NZFunGi/micro-radar/include/EmbeddedAirportCodes.h

#pragma once

// ICAO -> IATA airport code lookup, generated from OurAirports' public
// dataset (https://davidmegginson.github.io/ourairports-data/airports.csv,
// public domain) via a one-off filter (keep rows with both a valid 4-char
// ICAO and 3-char IATA code, sorted by ICAO for binary search). Regenerate
// by re-running that filter against a fresh copy of the CSV if this ever
// needs updating - not something this project re-derives at build time.
//
// Exists because OpenSky's /api/routes is ICAO-only (confirmed against its
// docs, not assumed) - RouteLookupManager tries hexdb.io first, which has a
// native IATA endpoint and needs no conversion, and only reaches for this
// table to convert OpenSky's ICAO fallback result to IATA for a consistent
// display format regardless of which source actually resolved a route.

#include <cstddef>
#include <cstring>

struct AirportCode {
    char icao[5]; // 4 chars + null terminator
    char iata[4]; // 3 chars + null terminator
};

constexpr size_t EMBEDDED_AIRPORT_CODE_COUNT = 7819;

// Sorted by icao - EmbeddedAirportLookup() below relies on this for binary search.
static const AirportCode EMBEDDED_AIRPORT_CODES[EMBEDDED_AIRPORT_CODE_COUNT] = {
    {"AGAF", "AFT"}, {"AGAR", "RNA"}, {"AGAT", "ATD"}, {"AGBA", "VEV"}, {"AGBT", "BPF"}, {"AGEV", "GEF"},
    {"AGGA", "AKS"}, {"AGGB", "BNY"}, {"AGGC", "CHY"}, {"AGGE", "BAS"}, {"AGGF", "FRE"}, {"AGGH", "HIR"},
    {"AGGI", "MBU"}, {"AGGJ", "AVU"}, {"AGGK", "IRA"}, {"AGGL", "SCZ"}, {"AGGM", "MUA"}, {"AGGN", "GZO"},
    {"AGGO", "MNY"}, {"AGGP", "PRS"}, {"AGGR", "RNL"}, {"AGGS", "EGM"}, {"AGGT", "NNB"}, {"AGGU", "RUS"},
    {"AGGV", "VAO"}, {"AGGY", "XYA"}, {"AGKG", "KGE"}, {"AGKU", "KUE"}, {"AGKW", "KWS"}, {"AGLM", "LLM"},
    {"AGNA", "NAZ"}, {"AGOB", "MHM"}, {"AGOK", "GTA"}, {"AGRC", "RIN"}, {"AGRM", "RBV"}, {"AGTI", "TLG"},
    {"AGVH", "VIU"}, {"ANYN", "INU"}, {"AYAA", "AMF"}, {"AYAE", "UAE"}, {"AYAF", "AFR"}, {"AYAG", "AUP"},
    {"AYAI", "ATP"}, {"AYAK", "AIH"}, {"AYAM", "AMU"}, {"AYAN", "ADC"}, {"AYAO", "AIE"}, {"AYAQ", "KPM"},
    {"AYAT", "AUJ"}, {"AYAW", "AWB"}, {"AYAX", "AEK"}, {"AYAY", "AYU"}, {"AYBA", "VMU"}, {"AYBC", "BCP"},
    {"AYBD", "BNM"}, {"AYBF", "BMZ"}, {"AYBG", "BDZ"}, {"AYBH", "BSP"}, {"AYBI", "BWP"}, {"AYBK", "BUA"},
    {"AYBL", "BAA"}, {"AYBM", "OPU"}, {"AYBO", "BMH"}, {"AYBP", "BPD"}, {"AYBQ", "BPK"}, {"AYBR", "BRP"},
    {"AYBU", "BUL"}, {"AYBZ", "XBN"}, {"AYCB", "CVB"}, {"AYCG", "CGC"}, {"AYCH", "CMU"}, {"AYCS", "SQT"},
    {"AYDB", "DBP"}, {"AYDE", "DER"}, {"AYDI", "BNT"}, {"AYDK", "MDM"}, {"AYDL", "KPF"}, {"AYDN", "DNU"},
    {"AYDO", "DOI"}, {"AYDR", "DOO"}, {"AYDU", "DAU"}, {"AYEA", "KRU"}, {"AYEB", "EMS"}, {"AYED", "XYR"},
    {"AYEE", "EMI"}, {"AYEF", "EFG"}, {"AYEH", "MHY"}, {"AYEL", "EPT"}, {"AYEN", "EGA"}, {"AYEO", "EMO"},
    {"AYER", "ERU"}, {"AYES", "MFZ"}, {"AYET", "BOT"}, {"AYEV", "ERE"}, {"AYEW", "SWE"}, {"AYFA", "FNE"},
    {"AYFI", "FIN"}, {"AYFR", "FAQ"}, {"AYFU", "FUM"}, {"AYGA", "GKA"}, {"AYGC", "GEW"}, {"AYGF", "GUG"},
    {"AYGG", "GRL"}, {"AYGI", "GAR"}, {"AYGJ", "GAZ"}, {"AYGL", "GOE"}, {"AYGN", "GUR"}, {"AYGP", "GAP"},
    {"AYGR", "PNP"}, {"AYGS", "GBC"}, {"AYGT", "GMI"}, {"AYGU", "AKG"}, {"AYGV", "GVI"}, {"AYGX", "GOC"},
    {"AYHB", "HBD"}, {"AYHE", "HNI"}, {"AYHF", "HYF"}, {"AYHH", "HNN"}, {"AYHK", "HKN"}, {"AYHO", "HIT"},
    {"AYHU", "HWA"}, {"AYIA", "IIS"}, {"AYID", "IDN"}, {"AYII", "IMN"}, {"AYIM", "KGM"}, {"AYIO", "IMD"},
    {"AYIQ", "KIE"}, {"AYIW", "WSA"}, {"AYIX", "WIU"}, {"AYIY", "MPX"}, {"AYJO", "KGH"}, {"AYJS", "JOP"},
    {"AYKA", "LSA"}, {"AYKB", "KBM"}, {"AYKC", "KDR"}, {"AYKD", "KMF"}, {"AYKG", "KPA"}, {"AYKH", "KAQ"},
    {"AYKI", "UNG"}, {"AYKJ", "KNE"}, {"AYKK", "KRI"}, {"AYKM", "KMA"}, {"AYKO", "KKD"}, {"AYKQ", "KGW"},
    {"AYKR", "KRX"}, {"AYKT", "KZF"}, {"AYKU", "KUQ"}, {"AYKV", "KVG"}, {"AYKW", "KWO"}, {"AYKY", "LNV"},
    {"AYLB", "LAB"}, {"AYLG", "KEG"}, {"AYLI", "KII"}, {"AYLL", "LGN"}, {"AYLM", "LMY"}, {"AYLN", "LNM"},
    {"AYLO", "LWI"}, {"AYLP", "LPN"}, {"AYLS", "LNG"}, {"AYLT", "LNC"}, {"AYLU", "LMI"}, {"AYLX", "LSJ"},
    {"AYMA", "MRM"}, {"AYMB", "OBM"}, {"AYMC", "MYX"}, {"AYMD", "MAG"}, {"AYMH", "HGU"}, {"AYMI", "MXK"},
    {"AYMJ", "MPG"}, {"AYML", "GUV"}, {"AYMN", "MDU"}, {"AYMO", "MAS"}, {"AYMP", "MLQ"}, {"AYMQ", "MQO"},
    {"AYMR", "MXH"}, {"AYMS", "MIS"}, {"AYMV", "MKN"}, {"AYMW", "MWG"}, {"AYMZ", "MPU"}, {"AYNA", "NKN"},
    {"AYNB", "KEX"}, {"AYNC", "NDN"}, {"AYND", "AUI"}, {"AYNE", "GBF"}, {"AYNI", "NUG"}, {"AYNJ", "NDI"},
    {"AYNM", "KSB"}, {"AYNN", "KDP"}, {"AYNO", "NMN"}, {"AYNS", "BXZ"}, {"AYNU", "UKU"}, {"AYNX", "ATN"},
    {"AYNY", "NBA"}, {"AYNZ", "LAE"}, {"AYOB", "OBX"}, {"AYOE", "KGB"}, {"AYOF", "OKV"}, {"AYOG", "OGE"},
    {"AYOJ", "OKP"}, {"AYOK", "HOC"}, {"AYOL", "KQL"}, {"AYOM", "OSE"}, {"AYOO", "KOM"}, {"AYOP", "KSP"},
    {"AYOQ", "KCJ"}, {"AYOV", "OLQ"}, {"AYOW", "KDE"}, {"AYPB", "PLE"}, {"AYPC", "PGB"}, {"AYPD", "PDI"},
    {"AYPE", "APR"}, {"AYPG", "PGN"}, {"AYPJ", "PMP"}, {"AYPO", "MPF"}, {"AYPQ", "PMN"}, {"AYPY", "POM"},
    {"AYQA", "KRJ"}, {"AYQL", "TLP"}, {"AYQO", "SPH"}, {"AYQQ", "ONB"}, {"AYQS", "SXA"}, {"AYRA", "KIQ"},
    {"AYRE", "RBP"}, {"AYRG", "RMN"}, {"AYRI", "KMR"}, {"AYRK", "RKU"}, {"AYRM", "MWI"}, {"AYRO", "KOR"},
    {"AYSA", "SBE"}, {"AYSD", "SDI"}, {"AYSE", "NIS"}, {"AYSF", "SFU"}, {"AYSG", "SIL"}, {"AYSH", "SBV"},
    {"AYSJ", "SIM"}, {"AYSK", "SGK"}, {"AYSL", "SXH"}, {"AYSO", "SBC"}, {"AYSP", "SMH"}, {"AYSS", "TDS"},
    {"AYSU", "SKC"}, {"AYSV", "SXW"}, {"AYSW", "SWG"}, {"AYSX", "MBV"}, {"AYTA", "TIZ"}, {"AYTB", "TBG"},
    {"AYTE", "TFM"}, {"AYTF", "TDB"}, {"AYTG", "TGL"}, {"AYTH", "TFB"}, {"AYTI", "TPI"}, {"AYTK", "RAB"},
    {"AYTN", "TKW"}, {"AYTO", "KDQ"}, {"AYTP", "TEP"}, {"AYTR", "TBQ"}, {"AYTS", "TSW"}, {"AYTT", "TRJ"},
    {"AYTU", "TFI"}, {"AYTV", "TBE"}, {"AYTW", "TWY"}, {"AYTY", "TEO"}, {"AYTZ", "TKB"}, {"AYUC", "UMC"},
    {"AYUE", "URU"}, {"AYUI", "UBI"}, {"AYUM", "AUV"}, {"AYUP", "GLP"}, {"AYUR", "UPR"}, {"AYUY", "KUX"},
    {"AYUZ", "UVO"}, {"AYVL", "TLW"}, {"AYVM", "TCJ"}, {"AYVN", "VAI"}, {"AYVO", "TON"}, {"AYVW", "WUV"},
    {"AYWB", "WAO"}, {"AYWC", "WTT"}, {"AYWD", "WBM"}, {"AYWF", "WAJ"}, {"AYWG", "AGL"}, {"AYWH", "WNU"},
    {"AYWJ", "WBC"}, {"AYWK", "WWK"}, {"AYWO", "WOA"}, {"AYWQ", "WKN"}, {"AYWS", "WSU"}, {"AYWT", "WTP"},
    {"AYWU", "WUG"}, {"AYXE", "YVD"}, {"AYXI", "SMJ"}, {"AYXO", "TLO"}, {"AYXP", "WPM"}, {"AYXW", "WEP"},
    {"AYYE", "KYX"}, {"AYYK", "YEQ"}, {"AYYL", "TCK"}, {"AYYM", "LNF"}, {"AYYO", "RAX"}, {"AYYP", "KPE"},
    {"AYYR", "KSX"}, {"AYZA", "ZEN"}, {"AYZI", "SWR"}, {"AYZN", "SIZ"}, {"AYZS", "OSG"}, {"BGAA", "JEG"},
    {"BGBW", "UAK"}, {"BGCH", "JCH"}, {"BGCO", "CNP"}, {"BGGH", "GOH"}, {"BGIG", "QFI"}, {"BGJN", "JAV"},
    {"BGKK", "KUS"}, {"BGMQ", "JSU"}, {"BGPT", "JFR"}, {"BGQO", "JJU"}, {"BGQQ", "NAQ"}, {"BGSF", "SFJ"},
    {"BGSG", "SGG"}, {"BGSI", "SRK"}, {"BGSO", "QOQ"}, {"BGSS", "JHS"}, {"BGST", "SAE"}, {"BGSV", "SVR"},
    {"BGTA", "TQA"}, {"BGTL", "THU"}, {"BGTN", "TQI"}, {"BGTQ", "XEQ"}, {"BGUK", "JUV"}, {"BGUM", "UMD"},
    {"BGUQ", "JQA"}, {"BGUT", "JUK"}, {"BIAR", "AEY"}, {"BIBD", "BIU"}, {"BIBF", "BGJ"}, {"BIBL", "BLO"},
    {"BIBV", "BXV"}, {"BIDV", "DJU"}, {"BIEG", "EGS"}, {"BIFM", "FAG"}, {"BIGF", "GUU"}, {"BIGJ", "GJR"},
    {"BIGR", "GRY"}, {"BIHK", "HVK"}, {"BIHN", "HFN"}, {"BIHU", "HZK"}, {"BIIS", "IFJ"}, {"BIKF", "KEF"},
    {"BIKP", "OPA"}, {"BIKR", "SAK"}, {"BINF", "NOR"}, {"BIRE", "RHA"}, {"BIRF", "OLI"}, {"BIRG", "RFN"},
    {"BIRK", "RKV"}, {"BIRL", "MVA"}, {"BISI", "SIJ"}, {"BIST", "SYK"}, {"BITE", "TEY"}, {"BITN", "THO"},
    {"BIVM", "VEY"}, {"BIVO", "VPN"}, {"BKPR", "PRN"}, {"CBBC", "ZEL"}, {"CYAB", "YAB"}, {"CYAC", "YAC"},
    {"CYAD", "YAR"}, {"CYAG", "YAG"}, {"CYAH", "YAH"}, {"CYAL", "YAL"}, {"CYAM", "YAM"}, {"CYAQ", "XKS"},
    {"CYAS", "YKG"}, {"CYAT", "YAT"}, {"CYAY", "YAY"}, {"CYAZ", "YAZ"}, {"CYBA", "YBA"}, {"CYBB", "YBB"},
    {"CYBC", "YBC"}, {"CYBD", "QBC"}, {"CYBE", "YBE"}, {"CYBF", "YBY"}, {"CYBG", "YBG"}, {"CYBK", "YBK"},
    {"CYBL", "YBL"}, {"CYBQ", "XTL"}, {"CYBR", "YBR"}, {"CYBT", "YBT"}, {"CYBV", "YBV"}, {"CYBX", "YBX"},
    {"CYCA", "YRF"}, {"CYCB", "YCB"}, {"CYCC", "YCC"}, {"CYCD", "YCD"}, {"CYCE", "YCE"}, {"CYCG", "YCG"},
    {"CYCH", "YCH"}, {"CYCK", "XCM"}, {"CYCL", "YCL"}, {"CYCN", "YCN"}, {"CYCO", "YCO"}, {"CYCQ", "YCQ"},
    {"CYCR", "YCR"}, {"CYCS", "YCS"}, {"CYCT", "YCT"}, {"CYCW", "YCW"}, {"CYCY", "YCY"}, {"CYCZ", "YCZ"},
    {"CYDA", "YDA"}, {"CYDB", "YDB"}, {"CYDF", "YDF"}, {"CYDL", "YDL"}, {"CYDM", "XRR"}, {"CYDN", "YDN"},
    {"CYDO", "YDO"}, {"CYDP", "YDP"}, {"CYDQ", "YDQ"}, {"CYEG", "YEG"}, {"CYEK", "YEK"}, {"CYEL", "YEL"},
    {"CYEM", "YEM"}, {"CYEN", "YEN"}, {"CYER", "YER"}, {"CYET", "YET"}, {"CYEU", "YEU"}, {"CYEV", "YEV"},
    {"CYEY", "YEY"}, {"CYFA", "YFA"}, {"CYFB", "YFB"}, {"CYFC", "YFC"}, {"CYFE", "YFE"}, {"CYFH", "YFH"},
    {"CYFJ", "YTM"}, {"CYFO", "YFO"}, {"CYFR", "YFR"}, {"CYFS", "YFS"}, {"CYFT", "YMN"}, {"CYGB", "YGB"},
    {"CYGH", "YGH"}, {"CYGK", "YGK"}, {"CYGL", "YGL"}, {"CYGM", "YGM"}, {"CYGO", "YGO"}, {"CYGP", "YGP"},
    {"CYGQ", "YGQ"}, {"CYGR", "YGR"}, {"CYGT", "YGT"}, {"CYGV", "YGV"}, {"CYGW", "YGW"}, {"CYGX", "YGX"},
    {"CYGZ", "YGZ"}, {"CYHA", "YQC"}, {"CYHB", "YHB"}, {"CYHC", "CXH"}, {"CYHD", "YHD"}, {"CYHE", "YHE"},
    {"CYHF", "YHF"}, {"CYHH", "YNS"}, {"CYHI", "YHI"}, {"CYHK", "YHK"}, {"CYHM", "YHM"}, {"CYHN", "YHN"},
    {"CYHO", "YHO"}, {"CYHP", "YHP"}, {"CYHR", "YHR"}, {"CYHT", "YHT"}, {"CYHU", "YHU"}, {"CYHY", "YHY"},
    {"CYHZ", "YHZ"}, {"CYIB", "YIB"}, {"CYID", "YDG"}, {"CYIF", "YIF"}, {"CYIK", "YIK"}, {"CYIO", "YIO"},
    {"CYIV", "YIV"}, {"CYJA", "YJA"}, {"CYJF", "YJF"}, {"CYJN", "YJN"}, {"CYJT", "YJT"}, {"CYKA", "YKA"},
    {"CYKC", "YKC"}, {"CYKD", "LAK"}, {"CYKF", "YKF"}, {"CYKG", "YWB"}, {"CYKJ", "YKJ"}, {"CYKL", "YKL"},
    {"CYKM", "YKD"}, {"CYKO", "AKV"}, {"CYKP", "YOG"}, {"CYKQ", "YKQ"}, {"CYKX", "YKX"}, {"CYKY", "YKY"},
    {"CYLA", "YPJ"}, {"CYLB", "YLB"}, {"CYLC", "YLC"}, {"CYLD", "YLD"}, {"CYLH", "YLH"}, {"CYLJ", "YLJ"},
    {"CYLK", "YSG"}, {"CYLL", "YLL"}, {"CYLQ", "YLQ"}, {"CYLR", "YLR"}, {"CYLS", "YLK"}, {"CYLT", "YLT"},
    {"CYLU", "XGR"}, {"CYLW", "YLW"}, {"CYMA", "YMA"}, {"CYME", "YME"}, {"CYMG", "YMG"}, {"CYMH", "YMH"},
    {"CYMJ", "YMJ"}, {"CYML", "YML"}, {"CYMM", "YMM"}, {"CYMO", "YMO"}, {"CYMT", "YMT"}, {"CYMU", "YUD"},
    {"CYMW", "YMW"}, {"CYMX", "YMX"}, {"CYNA", "YNA"}, {"CYNC", "YNC"}, {"CYND", "YND"}, {"CYNE", "YNE"},
    {"CYNH", "YNH"}, {"CYNJ", "YLY"}, {"CYNL", "YNL"}, {"CYNM", "YNM"}, {"CYNR", "HZP"}, {"CYOA", "YOA"},
    {"CYOC", "YOC"}, {"CYOD", "YOD"}, {"CYOH", "YOH"}, {"CYOJ", "YOJ"}, {"CYOO", "YOO"}, {"CYOP", "YOP"},
    {"CYOS", "YOS"}, {"CYOW", "YOW"}, {"CYPA", "YPA"}, {"CYPC", "YPC"}, {"CYPD", "YPS"}, {"CYPE", "YPE"},
    {"CYPG", "YPG"}, {"CYPH", "YPH"}, {"CYPL", "YPL"}, {"CYPM", "YPM"}, {"CYPN", "YPN"}, {"CYPO", "YPO"},
    {"CYPQ", "YPQ"}, {"CYPR", "YPR"}, {"CYPW", "YPW"}, {"CYPX", "YPX"}, {"CYPY", "YPY"}, {"CYPZ", "YPZ"},
    {"CYQA", "YQA"}, {"CYQB", "YQB"}, {"CYQD", "YQD"}, {"CYQF", "YQF"}, {"CYQG", "YQG"}, {"CYQH", "YQH"},
    {"CYQI", "YQI"}, {"CYQK", "YQK"}, {"CYQL", "YQL"}, {"CYQM", "YQM"}, {"CYQN", "YQN"}, {"CYQQ", "YQQ"},
    {"CYQR", "YQR"}, {"CYQS", "YQS"}, {"CYQT", "YQT"}, {"CYQU", "YQU"}, {"CYQV", "YQV"}, {"CYQW", "YQW"},
    {"CYQX", "YQX"}, {"CYQY", "YQY"}, {"CYQZ", "YQZ"}, {"CYRA", "YRA"}, {"CYRB", "YRB"}, {"CYRI", "YRI"},
    {"CYRJ", "YRJ"}, {"CYRL", "YRL"}, {"CYRM", "YRM"}, {"CYRO", "YRO"}, {"CYRQ", "YRQ"}, {"CYRS", "YRS"},
    {"CYRT", "YRT"}, {"CYRV", "YRV"}, {"CYSB", "YSB"}, {"CYSC", "YSC"}, {"CYSD", "YSD"}, {"CYSE", "YSE"},
    {"CYSF", "YSF"}, {"CYSH", "YSH"}, {"CYSJ", "YSJ"}, {"CYSK", "YSK"}, {"CYSL", "YSL"}, {"CYSM", "YSM"},
    {"CYSN", "YCM"}, {"CYSP", "YSP"}, {"CYST", "YST"}, {"CYSU", "YSU"}, {"CYSY", "YSY"}, {"CYTA", "YTA"},
    {"CYTE", "YTE"}, {"CYTF", "YTF"}, {"CYTH", "YTH"}, {"CYTL", "YTL"}, {"CYTQ", "YTQ"}, {"CYTR", "YTR"},
    {"CYTS", "YTS"}, {"CYTZ", "YTZ"}, {"CYUB", "YUB"}, {"CYUL", "YUL"}, {"CYUT", "YUT"}, {"CYUX", "YUX"},
    {"CYUY", "YUY"}, {"CYVB", "YVB"}, {"CYVC", "YVC"}, {"CYVG", "YVG"}, {"CYVK", "YVE"}, {"CYVL", "YCK"},
    {"CYVM", "YVM"}, {"CYVO", "YVO"}, {"CYVP", "YVP"}, {"CYVQ", "YVQ"}, {"CYVR", "YVR"}, {"CYVT", "YVT"},
    {"CYVV", "YVV"}, {"CYVZ", "YVZ"}, {"CYWA", "YWA"}, {"CYWE", "YFJ"}, {"CYWG", "YWG"}, {"CYWH", "YWH"},
    {"CYWJ", "YWJ"}, {"CYWK", "YWK"}, {"CYWL", "YWL"}, {"CYWP", "YWP"}, {"CYWY", "YWY"}, {"CYXC", "YXC"},
    {"CYXE", "YXE"}, {"CYXH", "YXH"}, {"CYXJ", "YXJ"}, {"CYXK", "YXK"}, {"CYXL", "YXL"}, {"CYXN", "YXN"},
    {"CYXP", "YXP"}, {"CYXQ", "YXQ"}, {"CYXR", "YXR"}, {"CYXS", "YXS"}, {"CYXT", "YXT"}, {"CYXU", "YXU"},
    {"CYXX", "YXX"}, {"CYXY", "YXY"}, {"CYXZ", "YXZ"}, {"CYYB", "YYB"}, {"CYYC", "YYC"}, {"CYYD", "YYD"},
    {"CYYE", "YYE"}, {"CYYF", "YYF"}, {"CYYG", "YYG"}, {"CYYH", "YYH"}, {"CYYJ", "YYJ"}, {"CYYL", "YYL"},
    {"CYYM", "YYM"}, {"CYYN", "YYN"}, {"CYYQ", "YYQ"}, {"CYYR", "YYR"}, {"CYYT", "YYT"}, {"CYYU", "YYU"},
    {"CYYW", "YYW"}, {"CYYY", "YYY"}, {"CYYZ", "YYZ"}, {"CYZE", "YZE"}, {"CYZF", "YZF"}, {"CYZG", "YZG"},
    {"CYZH", "YZH"}, {"CYZP", "YZP"}, {"CYZR", "YZR"}, {"CYZS", "YZS"}, {"CYZT", "YZT"}, {"CYZU", "YZU"},
    {"CYZV", "YZV"}, {"CYZW", "YZW"}, {"CYZX", "YZX"}, {"CZAC", "ZAC"}, {"CZAM", "YSN"}, {"CZBB", "YDT"},
    {"CZBD", "ILF"}, {"CZBF", "ZBF"}, {"CZBM", "ZBM"}, {"CZEE", "KES"}, {"CZEM", "ZEM"}, {"CZFA", "ZFA"},
    {"CZFD", "ZFD"}, {"CZFG", "XPK"}, {"CZFM", "ZFM"}, {"CZFN", "ZFN"}, {"CZGF", "ZGF"}, {"CZGI", "ZGI"},
    {"CZGR", "ZGR"}, {"CZHP", "ZHP"}, {"CZJG", "ZJG"}, {"CZJN", "ZJN"}, {"CZKE", "ZKE"}, {"CZLQ", "YTD"},
    {"CZMD", "MSA"}, {"CZML", "ZMH"}, {"CZMN", "PIW"}, {"CZMT", "ZMT"}, {"CZNG", "XPP"}, {"CZPB", "ZPB"},
    {"CZPC", "WPC"}, {"CZPO", "ZPO"}, {"CZRJ", "ZRJ"}, {"CZSJ", "ZSJ"}, {"CZSN", "XSI"}, {"CZST", "ZST"},
    {"CZSW", "ZSW"}, {"CZTA", "YDV"}, {"CZTM", "ZTM"}, {"CZUC", "ZUC"}, {"CZUM", "ZUM"}, {"CZWH", "XLB"},
    {"CZWL", "ZWL"}, {"DAAD", "BUJ"}, {"DAAE", "BJA"}, {"DAAG", "ALG"}, {"DAAJ", "DJG"}, {"DAAP", "VVZ"},
    {"DAAS", "QSF"}, {"DAAT", "TMR"}, {"DAAV", "GJL"}, {"DAAY", "MZW"}, {"DABB", "AAE"}, {"DABC", "CZL"},
    {"DABS", "TEE"}, {"DABT", "BLJ"}, {"DAFH", "HRM"}, {"DAOB", "TID"}, {"DAOF", "TIN"}, {"DAOI", "CFK"},
    {"DAOL", "TAF"}, {"DAON", "TLM"}, {"DAOO", "ORN"}, {"DAOR", "CBH"}, {"DAOS", "BFW"}, {"DAOV", "MUW"},
    {"DAOY", "EBH"}, {"DATG", "INF"}, {"DATM", "BMW"}, {"DAUA", "AZR"}, {"DAUB", "BSK"}, {"DAUE", "ELG"},
    {"DAUG", "GHA"}, {"DAUH", "HME"}, {"DAUI", "INZ"}, {"DAUK", "TGR"}, {"DAUL", "LOO"}, {"DAUO", "ELU"},
    {"DAUT", "TMX"}, {"DAUU", "OGX"}, {"DAUZ", "IAM"}, {"DBBB", "COO"}, {"DBBD", "DJA"}, {"DBBK", "KDC"},
    {"DBBN", "NAE"}, {"DBBP", "PKO"}, {"DBBS", "SVF"}, {"DFCA", "XKY"}, {"DFCC", "OUG"}, {"DFCJ", "XDJ"},
    {"DFCL", "XLU"}, {"DFCP", "PUP"}, {"DFEA", "XBO"}, {"DFEB", "XBG"}, {"DFED", "DIP"}, {"DFEE", "DOR"},
    {"DFEF", "FNG"}, {"DFEG", "XGG"}, {"DFEL", "XKA"}, {"DFEM", "TMQ"}, {"DFEP", "XPA"}, {"DFER", "ARL"},
    {"DFES", "XSE"}, {"DFET", "TEG"}, {"DFEZ", "XZA"}, {"DFFD", "OUA"}, {"DFOB", "BNR"}, {"DFOD", "DGU"},
    {"DFOG", "XGA"}, {"DFON", "XNU"}, {"DFOO", "BOY"}, {"DFOT", "TUQ"}, {"DFOU", "XDE"}, {"DFOY", "XAR"},
    {"DGAA", "ACC"}, {"DGLE", "TML"}, {"DGLW", "WZA"}, {"DGSI", "KMS"}, {"DGSN", "NYI"}, {"DGTK", "TKD"},
    {"DIAO", "ABO"}, {"DIAP", "ABJ"}, {"DIAU", "OGO"}, {"DIBI", "BXI"}, {"DIBK", "BYK"}, {"DIBN", "BQO"},
    {"DIBU", "BDK"}, {"DIDK", "DIM"}, {"DIDL", "DJO"}, {"DIGA", "GGN"}, {"DIGL", "GGO"}, {"DIGN", "BBV"},
    {"DIKO", "HGO"}, {"DIMN", "MJC"}, {"DIOD", "KEO"}, {"DIOF", "OFI"}, {"DISG", "SEO"}, {"DISP", "SPY"},
    {"DISS", "ZSS"}, {"DITB", "TXU"}, {"DITM", "TOZ"}, {"DIYO", "ASK"}, {"DNAA", "ABV"}, {"DNAI", "QUO"},
    {"DNAK", "AKR"}, {"DNAS", "ABB"}, {"DNBC", "BCU"}, {"DNBE", "BNI"}, {"DNCA", "CBQ"}, {"DNEN", "ENU"},
    {"DNGO", "GMO"}, {"DNIB", "IBA"}, {"DNIL", "ILR"}, {"DNIM", "QOW"}, {"DNJO", "JOS"}, {"DNKA", "KAD"},
    {"DNKN", "KAN"}, {"DNKT", "DKA"}, {"DNMA", "MIU"}, {"DNMK", "MDI"}, {"DNMM", "LOS"}, {"DNMN", "MXJ"},
    {"DNPM", "PHG"}, {"DNPO", "PHC"}, {"DNSO", "SKO"}, {"DNSU", "QRW"}, {"DNYO", "YOL"}, {"DNZA", "ZAR"},
    {"DRRM", "MFQ"}, {"DRRN", "NIM"}, {"DRRT", "THZ"}, {"DRZA", "AJY"}, {"DRZL", "RLT"}, {"DRZR", "ZND"},
    {"DTKA", "TBJ"}, {"DTMB", "MIR"}, {"DTNH", "NBE"}, {"DTTA", "TUN"}, {"DTTF", "GAF"}, {"DTTG", "GAE"},
    {"DTTJ", "DJE"}, {"DTTR", "EBM"}, {"DTTX", "SFA"}, {"DTTZ", "TOE"}, {"DXNG", "LRL"}, {"DXXX", "LFW"},
    {"EBAW", "ANR"}, {"EBBR", "BRU"}, {"EBCI", "CRL"}, {"EBKT", "KJK"}, {"EBLG", "LGG"}, {"EBOS", "OST"},
    {"EBZR", "OBL"}, {"EDAC", "AOC"}, {"EDAH", "HDF"}, {"EDAU", "IES"}, {"EDAX", "REB"}, {"EDBC", "CSO"},
    {"EDBH", "BBH"}, {"EDBN", "FNB"}, {"EDCG", "GTI"}, {"EDCK", "KOQ"}, {"EDCP", "PEF"}, {"EDDB", "BER"},
    {"EDDC", "DRS"}, {"EDDE", "ERF"}, {"EDDF", "FRA"}, {"EDDG", "FMO"}, {"EDDH", "HAM"}, {"EDDK", "CGN"},
    {"EDDL", "DUS"}, {"EDDM", "MUC"}, {"EDDN", "NUE"}, {"EDDP", "LEJ"}, {"EDDR", "SCN"}, {"EDDS", "STR"},
    {"EDDV", "HAJ"}, {"EDDW", "BRE"}, {"EDFH", "HHN"}, {"EDFM", "MHG"}, {"EDGE", "EIB"}, {"EDGS", "SGE"},
    {"EDHI", "XFW"}, {"EDHK", "KEL"}, {"EDHL", "LBC"}, {"EDHN", "EUM"}, {"EDJA", "FMM"}, {"EDKA", "AAH"},
    {"EDLE", "ESS"}, {"EDLI", "BFE"}, {"EDLN", "MGL"}, {"EDLP", "PAD"}, {"EDLV", "NRN"}, {"EDLW", "DTM"},
    {"EDMA", "AGB"}, {"EDMO", "OBF"}, {"EDMS", "RBM"}, {"EDNY", "FDH"}, {"EDQD", "BYU"}, {"EDQE", "URD"},
    {"EDQG", "GHF"}, {"EDQM", "HOQ"}, {"EDRB", "BBJ"}, {"EDRZ", "ZQW"}, {"EDSB", "FKB"}, {"EDTL", "LHA"},
    {"EDVE", "BWE"}, {"EDVK", "KSF"}, {"EDWE", "EME"}, {"EDWG", "AGE"}, {"EDWI", "WVN"}, {"EDWJ", "JUI"},
    {"EDWL", "LGO"}, {"EDWR", "BMK"}, {"EDWS", "NOD"}, {"EDWU", "VAC"}, {"EDWY", "NRD"}, {"EDWZ", "BMR"},
    {"EDXB", "HEI"}, {"EDXF", "FLF"}, {"EDXH", "HGL"}, {"EDXJ", "QHU"}, {"EDXO", "PSH"}, {"EDXW", "GWT"},
    {"EDXY", "OHR"}, {"EECL", "CHE"}, {"EEKA", "KDL"}, {"EEKE", "URE"}, {"EEPU", "EPU"}, {"EETN", "TLL"},
    {"EETU", "TAY"}, {"EFET", "ENF"}, {"EFHA", "KEV"}, {"EFHK", "HEL"}, {"EFHV", "HYV"}, {"EFIT", "KTQ"},
    {"EFIV", "IVL"}, {"EFJO", "JOE"}, {"EFJY", "JYV"}, {"EFKA", "KAU"}, {"EFKE", "KEM"}, {"EFKI", "KAJ"},
    {"EFKJ", "KHJ"}, {"EFKK", "KOK"}, {"EFKS", "KAO"}, {"EFKT", "KTT"}, {"EFKU", "KUO"}, {"EFLP", "LPP"},
    {"EFMA", "MHQ"}, {"EFMI", "MIK"}, {"EFOU", "OUL"}, {"EFPO", "POR"}, {"EFRO", "RVN"}, {"EFSA", "SVL"},
    {"EFSI", "SJY"}, {"EFSO", "SOT"}, {"EFTP", "TMP"}, {"EFTU", "TKU"}, {"EFUT", "UTI"}, {"EFVA", "VAA"},
    {"EFVR", "VRK"}, {"EFYL", "YLI"}, {"EGAA", "BFS"}, {"EGAB", "ENK"}, {"EGAC", "BHD"}, {"EGAE", "LDY"},
    {"EGBB", "BHX"}, {"EGBJ", "GLO"}, {"EGBK", "ORM"}, {"EGBN", "NQT"}, {"EGBP", "GBA"}, {"EGCC", "MAN"},
    {"EGDJ", "UPV"}, {"EGDY", "YEO"}, {"EGEC", "CAL"}, {"EGED", "EOI"}, {"EGEF", "FIE"}, {"EGEH", "WHS"},
    {"EGEI", "SKL"}, {"EGEL", "COL"}, {"EGEN", "NRL"}, {"EGEO", "OBN"}, {"EGEP", "PPW"}, {"EGER", "SOY"},
    {"EGES", "NDY"}, {"EGET", "LWK"}, {"EGEW", "WRY"}, {"EGEY", "CSA"}, {"EGFE", "HAW"}, {"EGFF", "CWL"},
    {"EGFH", "SWS"}, {"EGGD", "BRS"}, {"EGGP", "LPL"}, {"EGGW", "LTN"}, {"EGHC", "LEQ"}, {"EGHE", "ISC"},
    {"EGHH", "BOH"}, {"EGHI", "SOU"}, {"EGHJ", "BBP"}, {"EGHK", "PZE"}, {"EGHQ", "NQY"}, {"EGHR", "QUG"},
    {"EGJA", "ACI"}, {"EGJB", "GCI"}, {"EGJJ", "JER"}, {"EGKA", "ESH"}, {"EGKB", "BQH"}, {"EGKK", "LGW"},
    {"EGLC", "LCY"}, {"EGLF", "FAB"}, {"EGLK", "BBS"}, {"EGLL", "LHR"}, {"EGMC", "SEN"}, {"EGMD", "LYX"},
    {"EGNC", "CAX"}, {"EGNH", "BLK"}, {"EGNJ", "HUY"}, {"EGNL", "BWF"}, {"EGNM", "LBA"}, {"EGNO", "WRT"},
    {"EGNR", "CEG"}, {"EGNS", "IOM"}, {"EGNT", "NCL"}, {"EGNV", "MME"}, {"EGNX", "EMA"}, {"EGOV", "VLY"},
    {"EGPA", "KOI"}, {"EGPB", "LSI"}, {"EGPC", "WIC"}, {"EGPD", "ABZ"}, {"EGPE", "INV"}, {"EGPF", "GLA"},
    {"EGPH", "EDI"}, {"EGPI", "ILY"}, {"EGPK", "PIK"}, {"EGPL", "BEB"}, {"EGPN", "DND"}, {"EGPO", "SYY"},
    {"EGPR", "BRR"}, {"EGPT", "PSL"}, {"EGPU", "TRE"}, {"EGQL", "ADX"}, {"EGQS", "LMO"}, {"EGSC", "CBG"},
    {"EGSH", "NWI"}, {"EGSS", "STN"}, {"EGTB", "HYC"}, {"EGTE", "EXT"}, {"EGTK", "OXF"}, {"EGTO", "RCS"},
    {"EGUB", "BEX"}, {"EGUL", "LKZ"}, {"EGUN", "MHZ"}, {"EGUY", "QUY"}, {"EGVA", "FFD"}, {"EGVN", "BZZ"},
    {"EGVO", "ODH"}, {"EGWU", "NHT"}, {"EGXC", "QCY"}, {"EGXH", "BEQ"}, {"EGXW", "WTN"}, {"EGYM", "KNF"},
    {"EGYP", "MPN"}, {"EHAM", "AMS"}, {"EHBK", "MST"}, {"EHEH", "EIN"}, {"EHGG", "GRQ"}, {"EHGR", "GLZ"},
    {"EHKD", "DHR"}, {"EHLE", "LEY"}, {"EHLW", "LWR"}, {"EHRD", "RTM"}, {"EHTW", "ENS"}, {"EHVK", "UDE"},
    {"EHWO", "WOE"}, {"EIBN", "BYT"}, {"EIBT", "BLY"}, {"EICA", "NNR"}, {"EICK", "ORK"}, {"EIDL", "CFN"},
    {"EIDW", "DUB"}, {"EIIM", "IOR"}, {"EIIR", "INQ"}, {"EIKK", "KKY"}, {"EIKN", "NOC"}, {"EIKY", "KIR"},
    {"EIMN", "IIA"}, {"EINN", "SNN"}, {"EISG", "SXL"}, {"EIWF", "WAT"}, {"EKAH", "AAR"}, {"EKBI", "BLL"},
    {"EKCH", "CPH"}, {"EKEB", "EBJ"}, {"EKKA", "KRP"}, {"EKLS", "BYR"}, {"EKMB", "MRW"}, {"EKOD", "ODE"},
    {"EKRK", "RKE"}, {"EKRN", "RNN"}, {"EKSB", "SGD"}, {"EKSN", "CNL"}, {"EKSP", "SKS"}, {"EKSV", "SQW"},
    {"EKTS", "TED"}, {"EKVG", "FAE"}, {"EKVJ", "STA"}, {"EKYT", "AAL"}, {"ELLX", "LUX"}, {"ENAL", "AES"},
    {"ENAN", "ANX"}, {"ENAT", "ALF"}, {"ENBL", "FDE"}, {"ENBN", "BNN"}, {"ENBO", "BOO"}, {"ENBR", "BGO"},
    {"ENBS", "BJF"}, {"ENBV", "BVG"}, {"ENCN", "KRS"}, {"ENDU", "BDU"}, {"ENEV", "EVE"}, {"ENFL", "FRO"},
    {"ENGM", "OSL"}, {"ENHA", "HMR"}, {"ENHD", "HAU"}, {"ENHF", "HFT"}, {"ENHK", "HAA"}, {"ENHV", "HVG"},
    {"ENKB", "KSU"}, {"ENKL", "GLL"}, {"ENKR", "KKN"}, {"ENLK", "LKN"}, {"ENMH", "MEH"}, {"ENML", "MOL"},
    {"ENMS", "MJF"}, {"ENNA", "LKL"}, {"ENNM", "OSY"}, {"ENNO", "NTB"}, {"ENOL", "OLA"}, {"ENOV", "HOV"},
    {"ENRA", "MQN"}, {"ENRM", "RVK"}, {"ENRO", "RRS"}, {"ENRS", "RET"}, {"ENSB", "LYR"}, {"ENSD", "SDN"},
    {"ENSG", "SOG"}, {"ENSH", "SVJ"}, {"ENSK", "SKN"}, {"ENSO", "SRP"}, {"ENSR", "SOJ"}, {"ENSS", "VAW"},
    {"ENST", "SSJ"}, {"ENTC", "TOS"}, {"ENTO", "TRF"}, {"ENVA", "TRD"}, {"ENVD", "VDS"}, {"ENZV", "SVG"},
    {"EPBY", "BZG"}, {"EPGD", "GDN"}, {"EPKK", "KRK"}, {"EPKT", "KTW"}, {"EPLB", "LUZ"}, {"EPLL", "LCJ"},
    {"EPMO", "WMI"}, {"EPPO", "POZ"}, {"EPRA", "RDO"}, {"EPRZ", "RZE"}, {"EPSC", "SZZ"}, {"EPSY", "SZY"},
    {"EPWA", "WAW"}, {"EPWR", "WRO"}, {"EPZG", "IEG"}, {"ESDF", "RNB"}, {"ESGG", "GOT"}, {"ESGJ", "JKG"},
    {"ESGL", "LDK"}, {"ESGP", "GSE"}, {"ESGR", "KVB"}, {"ESGT", "THN"}, {"ESKK", "KSK"}, {"ESKM", "MXX"},
    {"ESKN", "NYO"}, {"ESKS", "SCR"}, {"ESMK", "KID"}, {"ESMO", "OSK"}, {"ESMQ", "KLR"}, {"ESMS", "MMX"},
    {"ESMT", "HAD"}, {"ESMX", "VXO"}, {"ESND", "EVG"}, {"ESNG", "GEV"}, {"ESNH", "HUV"}, {"ESNK", "KRF"},
    {"ESNL", "LYC"}, {"ESNN", "SDL"}, {"ESNO", "OER"}, {"ESNQ", "KRN"}, {"ESNS", "SFT"}, {"ESNU", "UME"},
    {"ESNV", "VHM"}, {"ESNX", "AJR"}, {"ESNY", "SOO"}, {"ESNZ", "OSD"}, {"ESOE", "ORB"}, {"ESOH", "HFS"},
    {"ESOK", "KSD"}, {"ESOW", "VST"}, {"ESPA", "LLA"}, {"ESSA", "ARN"}, {"ESSB", "BMA"}, {"ESSD", "BLE"},
    {"ESSF", "HLF"}, {"ESSL", "LPI"}, {"ESSP", "NRK"}, {"ESST", "TYF"}, {"ESSU", "EKT"}, {"ESSV", "VBY"},
    {"ESSW", "VVK"}, {"ESTA", "AGH"}, {"ESUD", "SQO"}, {"ESUE", "IDB"}, {"ESUP", "PJA"}, {"ESUT", "HMV"},
    {"ETAD", "SPM"}, {"ETAR", "RMS"}, {"ETHF", "FRZ"}, {"ETIK", "ILH"}, {"ETMN", "FCN"}, {"ETNG", "GKE"},
    {"ETNL", "RLG"}, {"ETNS", "WBG"}, {"ETOU", "WIE"}, {"ETSI", "IGS"}, {"EVLA", "LPX"}, {"EVRA", "RIX"},
    {"EVVA", "VNT"}, {"EYKA", "KUN"}, {"EYPA", "PLQ"}, {"EYPP", "PNV"}, {"EYSA", "SQQ"}, {"EYVI", "VNO"},
    {"FAAB", "ALJ"}, {"FAAG", "AGZ"}, {"FAAL", "ADY"}, {"FAAR", "ASS"}, {"FABE", "BIY"}, {"FABL", "BFN"},
    {"FABU", "UTE"}, {"FACD", "CDO"}, {"FACT", "CPT"}, {"FADK", "DUK"}, {"FADQ", "PZL"}, {"FAEL", "ELS"},
    {"FAEM", "EMG"}, {"FAER", "ELL"}, {"FAFB", "FCB"}, {"FAGC", "GCJ"}, {"FAGG", "GRJ"}, {"FAGI", "GIY"},
    {"FAGM", "QRA"}, {"FAHL", "HLW"}, {"FAHR", "HRS"}, {"FAHS", "HDS"}, {"FAKD", "KXE"}, {"FAKM", "KIM"},
    {"FAKN", "MQP"}, {"FAKP", "KOF"}, {"FAKU", "KMH"}, {"FAKZ", "KLZ"}, {"FALA", "HLA"}, {"FALC", "LMR"},
    {"FALD", "LDZ"}, {"FALE", "DUR"}, {"FALO", "LCD"}, {"FALW", "SDB"}, {"FALY", "LAY"}, {"FAMD", "AAM"},
    {"FAMG", "MGH"}, {"FAMM", "MBD"}, {"FAMN", "LLE"}, {"FAMO", "MZY"}, {"FAMU", "MZQ"}, {"FANC", "NCS"},
    {"FANG", "NGL"}, {"FANS", "NLP"}, {"FAOB", "OVG"}, {"FAOH", "OUH"}, {"FAOR", "JNB"}, {"FAPA", "AFD"},
    {"FAPE", "PLZ"}, {"FAPG", "PBZ"}, {"FAPH", "PHW"}, {"FAPJ", "JOH"}, {"FAPK", "PRK"}, {"FAPM", "PZB"},
    {"FAPN", "NTY"}, {"FAPP", "PTG"}, {"FAPS", "PCF"}, {"FAQT", "UTW"}, {"FARB", "RCB"}, {"FARI", "RVO"},
    {"FARS", "ROD"}, {"FASB", "SBU"}, {"FASC", "ZEC"}, {"FASS", "SIS"}, {"FASZ", "SZK"}, {"FATH", "THY"},
    {"FATN", "TCU"}, {"FATZ", "LTA"}, {"FAUL", "ULD"}, {"FAUP", "UTN"}, {"FAUS", "ULX"}, {"FAUT", "UTT"},
    {"FAVB", "VRU"}, {"FAVG", "VIR"}, {"FAVR", "VRE"}, {"FAVY", "VYD"}, {"FAWB", "PRY"}, {"FAWK", "WKF"},
    {"FAWM", "WEL"}, {"FBGZ", "GNZ"}, {"FBJW", "JWA"}, {"FBKE", "BBK"}, {"FBKR", "KHW"}, {"FBMN", "MUB"},
    {"FBOR", "ORP"}, {"FBPM", "FRW"}, {"FBSK", "GBE"}, {"FBSN", "SXN"}, {"FBSP", "PKW"}, {"FBSV", "SVT"},
    {"FBSW", "SWX"}, {"FBTL", "TLD"}, {"FBTS", "TBY"}, {"FCBB", "BZV"}, {"FCBD", "DJM"}, {"FCBK", "KNJ"},
    {"FCBL", "LCO"}, {"FCBM", "MUY"}, {"FCBS", "SIB"}, {"FCBY", "NKY"}, {"FCBZ", "ANJ"}, {"FCMM", "MSX"},
    {"FCOB", "BOE"}, {"FCOD", "OLL"}, {"FCOE", "EWO"}, {"FCOG", "GMM"}, {"FCOI", "ION"}, {"FCOK", "KEE"},
    {"FCOM", "MKJ"}, {"FCOO", "FTX"}, {"FCOS", "SOE"}, {"FCOT", "BTB"}, {"FCOU", "OUE"}, {"FCPA", "KMK"},
    {"FCPD", "DIS"}, {"FCPP", "PNR"}, {"FDMS", "MTS"}, {"FDSK", "SHO"}, {"FEFC", "CRF"}, {"FEFF", "BGF"},
    {"FEFG", "BGU"}, {"FEFI", "IRO"}, {"FEFM", "BBY"}, {"FEFN", "NDL"}, {"FEFO", "BOP"}, {"FEFR", "BIV"},
    {"FEFS", "BSN"}, {"FEFT", "BBT"}, {"FEFW", "ODA"}, {"FEFY", "AIG"}, {"FEFZ", "IMO"}, {"FEGE", "MKI"},
    {"FEGF", "BTG"}, {"FEGL", "GDI"}, {"FEGM", "BMF"}, {"FEGO", "ODJ"}, {"FEGR", "RFA"}, {"FEGU", "BCF"},
    {"FEGZ", "BOZ"}, {"FGAN", "NBN"}, {"FGBT", "BSG"}, {"FGCO", "OCS"}, {"FGMY", "GEM"}, {"FGSL", "SSG"},
    {"FHAW", "ASI"}, {"FHSH", "HLE"}, {"FIMP", "MRU"}, {"FIMR", "RRG"}, {"FKKB", "KBI"}, {"FKKC", "TKC"},
    {"FKKD", "DLA"}, {"FKKF", "MMF"}, {"FKKG", "BLC"}, {"FKKH", "KLE"}, {"FKKI", "OUR"}, {"FKKJ", "GXX"},
    {"FKKL", "MVR"}, {"FKKM", "FOM"}, {"FKKN", "NGE"}, {"FKKO", "BTA"}, {"FKKR", "GOU"}, {"FKKS", "DSC"},
    {"FKKU", "BFX"}, {"FKKV", "BPC"}, {"FKKW", "EBW"}, {"FKKY", "YAO"}, {"FKYS", "NSI"}, {"FLBA", "MMQ"},
    {"FLCP", "CIP"}, {"FLCU", "CGX"}, {"FLHN", "LVI"}, {"FLKE", "CGJ"}, {"FLKK", "LUN"}, {"FLKL", "KLB"},
    {"FLKO", "KMZ"}, {"FLKS", "KAA"}, {"FLKY", "ZKB"}, {"FLLK", "LXU"}, {"FLMA", "MNS"}, {"FLMF", "MFU"},
    {"FLMG", "MNR"}, {"FLNA", "ZGM"}, {"FLSK", "NLA"}, {"FLSN", "SXG"}, {"FLSO", "KIW"}, {"FLSS", "SJQ"},
    {"FLSW", "SLI"}, {"FLZB", "BBZ"}, {"FMCH", "HAH"}, {"FMCI", "NWA"}, {"FMCV", "AJN"}, {"FMCZ", "DZA"},
    {"FMEE", "RUN"}, {"FMEP", "ZSE"}, {"FMFE", "OHB"}, {"FMMB", "AMY"}, {"FMMC", "WML"}, {"FMME", "ATJ"},
    {"FMMG", "WAQ"}, {"FMMH", "VVB"}, {"FMMI", "TNR"}, {"FMMK", "JVA"}, {"FMML", "BMD"}, {"FMMN", "ZVA"},
    {"FMMO", "MXT"}, {"FMMQ", "ILK"}, {"FMMR", "TVA"}, {"FMMS", "SMS"}, {"FMMT", "TMM"}, {"FMMU", "WTA"},
    {"FMMV", "MOQ"}, {"FMMX", "WTS"}, {"FMMY", "VAT"}, {"FMMZ", "WAM"}, {"FMNA", "DIE"}, {"FMNC", "WMR"},
    {"FMND", "ZWA"}, {"FMNE", "AMB"}, {"FMNF", "WBD"}, {"FMNG", "WPB"}, {"FMNH", "ANM"}, {"FMNL", "HVA"},
    {"FMNM", "MJN"}, {"FMNN", "NOS"}, {"FMNO", "DWB"}, {"FMNP", "WMP"}, {"FMNQ", "BPY"}, {"FMNR", "WMN"},
    {"FMNS", "SVB"}, {"FMNT", "TTS"}, {"FMNV", "VOH"}, {"FMNW", "WAI"}, {"FMNX", "WMA"}, {"FMSB", "WBO"},
    {"FMSC", "WMD"}, {"FMSD", "FTU"}, {"FMSF", "WFI"}, {"FMSG", "RVA"}, {"FMSI", "IHO"}, {"FMSJ", "MJA"},
    {"FMSK", "WVK"}, {"FMSL", "OVA"}, {"FMSM", "MNJ"}, {"FMSN", "TDV"}, {"FMSR", "MXM"}, {"FMST", "TLE"},
    {"FMSU", "VND"}, {"FMSV", "BKU"}, {"FMSY", "AMP"}, {"FMSZ", "WAK"}, {"FNAM", "AZZ"}, {"FNBC", "SSY"},
    {"FNBG", "BUG"}, {"FNBJ", "NBJ"}, {"FNBL", "GGC"}, {"FNCA", "CAB"}, {"FNCF", "CFF"}, {"FNCH", "PGI"},
    {"FNCP", "KNP"}, {"FNCT", "CBT"}, {"FNCV", "CTI"}, {"FNCZ", "CAV"}, {"FNDU", "DUE"}, {"FNGI", "VPE"},
    {"FNHU", "NOV"}, {"FNJM", "JMB"}, {"FNKU", "SVP"}, {"FNLB", "LLT"}, {"FNLK", "LBZ"}, {"FNLU", "LAD"},
    {"FNLZ", "LZM"}, {"FNMA", "MEG"}, {"FNME", "SPP"}, {"FNMO", "MSZ"}, {"FNNG", "GXG"}, {"FNPA", "PBN"},
    {"FNSA", "VHC"}, {"FNSO", "SZA"}, {"FNSU", "NDD"}, {"FNUA", "UAL"}, {"FNUB", "SDD"}, {"FNUE", "LUO"},
    {"FNUG", "UGO"}, {"FNWK", "CEO"}, {"FNXA", "XGN"}, {"FNZE", "ARZ"}, {"FNZG", "NZA"}, {"FOGA", "AKE"},
    {"FOGB", "BGB"}, {"FOGE", "KDN"}, {"FOGF", "FOU"}, {"FOGG", "MBC"}, {"FOGI", "MGX"}, {"FOGJ", "KDJ"},
    {"FOGK", "KOU"}, {"FOGM", "MJL"}, {"FOGO", "OYE"}, {"FOGQ", "OKN"}, {"FOGR", "LBQ"}, {"FOGV", "MVX"},
    {"FOGW", "AWE"}, {"FOGX", "GAX"}, {"FOOB", "BMM"}, {"FOOD", "MFF"}, {"FOOE", "MKB"}, {"FOOG", "POG"},
    {"FOOH", "OMB"}, {"FOOI", "IGE"}, {"FOOK", "MKU"}, {"FOOL", "LBV"}, {"FOOM", "MZC"}, {"FOON", "MVB"},
    {"FOOR", "LTL"}, {"FOOT", "TCH"}, {"FOOY", "MYB"}, {"FPPR", "PCP"}, {"FPST", "TMS"}, {"FQAG", "ANO"},
    {"FQBR", "BEW"}, {"FQCB", "FXO"}, {"FQCH", "VPY"}, {"FQIA", "IHC"}, {"FQIB", "IBO"}, {"FQIN", "INH"},
    {"FQLC", "VXC"}, {"FQLU", "LFB"}, {"FQMA", "MPM"}, {"FQMD", "MUD"}, {"FQMP", "MZB"}, {"FQNC", "MNC"},
    {"FQNP", "APL"}, {"FQPB", "POL"}, {"FQPO", "PDD"}, {"FQQL", "UEL"}, {"FQTT", "TET"}, {"FQVL", "VNX"},
    {"FQXA", "VJB"}, {"FSDR", "DES"}, {"FSIA", "SEZ"}, {"FSPP", "PRI"}, {"FSSB", "BDI"}, {"FSSD", "DEI"},
    {"FSSF", "FRK"}, {"FTTA", "SRH"}, {"FTTB", "OGR"}, {"FTTC", "AEH"}, {"FTTD", "MQQ"}, {"FTTH", "LTC"},
    {"FTTI", "ATV"}, {"FTTJ", "NDJ"}, {"FTTK", "BKR"}, {"FTTL", "OTC"}, {"FTTM", "MVO"}, {"FTTN", "AMC"},
    {"FTTP", "PLF"}, {"FTTS", "OUT"}, {"FTTU", "AMO"}, {"FTTY", "FYT"}, {"FVCH", "CHJ"}, {"FVCZ", "BFO"},
    {"FVFA", "VFA"}, {"FVJN", "BUQ"}, {"FVKB", "KAB"}, {"FVMH", "MJW"}, {"FVMU", "UTA"}, {"FVMV", "MVZ"},
    {"FVRG", "HRE"}, {"FVTL", "GWE"}, {"FVWN", "HWN"}, {"FVWT", "WKI"}, {"FWCD", "CEH"}, {"FWCL", "BLZ"},
    {"FWCM", "CMK"}, {"FWDW", "DWA"}, {"FWKA", "KGJ"}, {"FWKG", "KBQ"}, {"FWKI", "LLW"}, {"FWLK", "LIX"},
    {"FWMY", "MYZ"}, {"FWSM", "LMB"}, {"FWUU", "ZZU"}, {"FXLK", "LEF"}, {"FXLR", "LRB"}, {"FXLS", "LES"},
    {"FXMA", "MSG"}, {"FXMF", "MFC"}, {"FXMK", "MKH"}, {"FXMM", "MSU"}, {"FXNK", "NKU"}, {"FXPG", "PEL"},
    {"FXQG", "UTG"}, {"FXQN", "UNE"}, {"FXSH", "SHK"}, {"FXSK", "SKQ"}, {"FXSM", "SOK"}, {"FXSS", "SHZ"},
    {"FXTA", "THB"}, {"FXTK", "TKO"}, {"FYAA", "AIW"}, {"FYAR", "ADI"}, {"FYGB", "GOG"}, {"FYGF", "GFY"},
    {"FYHI", "HAL"}, {"FYKB", "KAS"}, {"FYKM", "MPA"}, {"FYKT", "KMP"}, {"FYLS", "LHU"}, {"FYLZ", "LUD"},
    {"FYME", "MJO"}, {"FYMG", "MQG"}, {"FYMO", "OKU"}, {"FYNA", "NNI"}, {"FYOA", "OND"}, {"FYOE", "OMG"},
    {"FYOG", "OMD"}, {"FYOO", "OKF"}, {"FYOP", "OPW"}, {"FYOS", "OHI"}, {"FYOW", "OTJ"}, {"FYRU", "NDU"},
    {"FYSA", "RHN"}, {"FYSM", "SWP"}, {"FYSS", "SZM"}, {"FYTE", "TCY"}, {"FYTM", "TSB"}, {"FYWB", "WVB"},
    {"FYWE", "ERS"}, {"FYWH", "WDH"}, {"FZAA", "FIH"}, {"FZAB", "NLO"}, {"FZAG", "MNB"}, {"FZAJ", "BOA"},
    {"FZAL", "LZI"}, {"FZAM", "MAT"}, {"FZAR", "NKL"}, {"FZBA", "INO"}, {"FZBI", "NIO"}, {"FZBO", "FDU"},
    {"FZBT", "KRZ"}, {"FZCA", "KKW"}, {"FZCB", "IDF"}, {"FZCV", "MSM"}, {"FZEA", "MDK"}, {"FZEN", "BSU"},
    {"FZFA", "LIE"}, {"FZFD", "BDT"}, {"FZFK", "GMA"}, {"FZFP", "KLI"}, {"FZFU", "BMB"}, {"FZGA", "LIQ"},
    {"FZGN", "BNB"}, {"FZGV", "IKL"}, {"FZIC", "FKI"}, {"FZIR", "YAN"}, {"FZJH", "IRP"}, {"FZKA", "BUX"},
    {"FZKJ", "BZU"}, {"FZMA", "BKY"}, {"FZNA", "GOM"}, {"FZNP", "BNC"}, {"FZOA", "KND"}, {"FZOD", "KLY"},
    {"FZOP", "PUN"}, {"FZQA", "FBM"}, {"FZQC", "PWO"}, {"FZQG", "KEC"}, {"FZQM", "KWZ"}, {"FZRA", "MNO"},
    {"FZRB", "BDV"}, {"FZRF", "FMI"}, {"FZRM", "KBO"}, {"FZRQ", "KOO"}, {"FZSB", "KMN"}, {"FZSK", "KAP"},
    {"FZTK", "KNM"}, {"FZUA", "KGA"}, {"FZUG", "LZA"}, {"FZUK", "TSH"}, {"FZVA", "LJA"}, {"FZVI", "LBO"},
    {"FZVM", "MEW"}, {"FZVR", "BAN"}, {"FZVS", "PFR"}, {"FZWA", "MJM"}, {"FZWT", "KBN"}, {"GABS", "BKO"},
    {"GAGM", "GUD"}, {"GAGO", "GAQ"}, {"GAKA", "KNZ"}, {"GAKD", "KYS"}, {"GAMB", "MZI"}, {"GANK", "NRM"},
    {"GANR", "NIX"}, {"GASO", "KSS"}, {"GATB", "TOM"}, {"GAYE", "EYL"}, {"GBYD", "BJL"}, {"GCFV", "FUE"},
    {"GCGM", "GMZ"}, {"GCHI", "VDE"}, {"GCLA", "SPC"}, {"GCLP", "LPA"}, {"GCRR", "ACE"}, {"GCTS", "TFS"},
    {"GCXO", "TFN"}, {"GECE", "JCU"}, {"GEML", "MLN"}, {"GFBO", "KBS"}, {"GFGK", "GBK"}, {"GFHA", "HGS"},
    {"GFKB", "KBA"}, {"GFKE", "KEN"}, {"GFLL", "FNA"}, {"GFYE", "WYE"}, {"GGBU", "BQE"}, {"GGOV", "OXB"},
    {"GLBU", "UCN"}, {"GLCP", "CPA"}, {"GLGE", "SNI"}, {"GLMR", "MLW"}, {"GLNA", "NIA"}, {"GLRB", "ROB"},
    {"GLST", "SAZ"}, {"GLTN", "THC"}, {"GLVA", "VOI"}, {"GMAD", "AGA"}, {"GMAG", "GLN"}, {"GMAT", "TTA"},
    {"GMAZ", "OZG"}, {"GMFB", "UAR"}, {"GMFF", "FEZ"}, {"GMFK", "ERH"}, {"GMFM", "MEK"}, {"GMFO", "OUD"},
    {"GMMA", "SMW"}, {"GMMB", "GMD"}, {"GMMD", "BEM"}, {"GMME", "RBA"}, {"GMMH", "VIL"}, {"GMMI", "ESU"},
    {"GMML", "EUN"}, {"GMMN", "CMN"}, {"GMMP", "NNA"}, {"GMMW", "NDR"}, {"GMMX", "RAK"}, {"GMMZ", "OZZ"},
    {"GMTA", "AHU"}, {"GMTN", "TTU"}, {"GMTT", "TNG"}, {"GOBD", "DSS"}, {"GODK", "KDA"}, {"GOGG", "ZIG"},
    {"GOGS", "CSK"}, {"GOOK", "KLC"}, {"GOOY", "DKR"}, {"GOSM", "MAX"}, {"GOSP", "POD"}, {"GOSR", "RDT"},
    {"GOSS", "XLS"}, {"GOTB", "BXE"}, {"GOTK", "KGG"}, {"GOTS", "SMY"}, {"GOTT", "TUD"}, {"GQNA", "AEO"},
    {"GQNB", "OTL"}, {"GQNC", "THI"}, {"GQND", "TIY"}, {"GQNE", "BGH"}, {"GQNF", "KFA"}, {"GQNH", "TMD"},
    {"GQNI", "EMN"}, {"GQNJ", "AJJ"}, {"GQNK", "KED"}, {"GQNL", "MOM"}, {"GQNO", "NKC"}, {"GQNS", "SEY"},
    {"GQNT", "THT"}, {"GQPA", "ATR"}, {"GQPF", "FGD"}, {"GQPP", "NDB"}, {"GQPZ", "OUZ"}, {"GUCY", "CKY"},
    {"GUFA", "FIG"}, {"GUFH", "FAA"}, {"GUKU", "KSI"}, {"GULB", "LEK"}, {"GUMA", "MCA"}, {"GUNZ", "NZE"},
    {"GUOK", "BKJ"}, {"GUSB", "SBI"}, {"GUSI", "GII"}, {"GVAC", "SID"}, {"GVAN", "NTO"}, {"GVBA", "BVC"},
    {"GVMA", "MMO"}, {"GVMT", "MTI"}, {"GVNP", "RAI"}, {"GVSF", "SFL"}, {"GVSN", "SNE"}, {"GVSV", "VXE"},
    {"GXUD", "KNN"}, {"HAAB", "ADD"}, {"HAAM", "AMH"}, {"HAAX", "AXU"}, {"HABC", "BCO"}, {"HABD", "BJR"},
    {"HABE", "BEI"}, {"HADC", "DSE"}, {"HADD", "DEM"}, {"HADM", "DBM"}, {"HADR", "DIR"}, {"HADT", "DBT"},
    {"HAFN", "FNH"}, {"HAGB", "GOB"}, {"HAGH", "GNN"}, {"HAGM", "GMB"}, {"HAGN", "GDQ"}, {"HAGO", "GDE"},
    {"HAGR", "GOR"}, {"HAHM", "QHR"}, {"HAHU", "HUE"}, {"HAJJ", "JIJ"}, {"HAJM", "JIM"}, {"HAKD", "ABK"},
    {"HAKL", "LFO"}, {"HALA", "AWA"}, {"HALL", "LLI"}, {"HAMA", "MKS"}, {"HAMK", "MQX"}, {"HAMM", "ETE"},
    {"HAMN", "NDM"}, {"HAMR", "MUJ"}, {"HAMT", "MTF"}, {"HANG", "EGL"}, {"HANJ", "NEJ"}, {"HANK", "NEK"},
    {"HAPW", "PWI"}, {"HASD", "SXU"}, {"HASK", "SKR"}, {"HASL", "HIL"}, {"HASM", "SZE"}, {"HASO", "ASO"},
    {"HASR", "SHC"}, {"HATP", "TIE"}, {"HAWR", "WRA"}, {"HBBA", "BJM"}, {"HBBE", "GID"}, {"HBBO", "KRE"},
    {"HCAD", "AAD"}, {"HCGR", "GGR"}, {"HCMA", "ALU"}, {"HCMB", "BIB"}, {"HCMC", "CXN"}, {"HCMD", "BSY"},
    {"HCME", "HCM"}, {"HCMF", "BSA"}, {"HCMG", "GSR"}, {"HCMH", "HGA"}, {"HCMI", "BBO"}, {"HCMJ", "LGX"},
    {"HCMK", "KMU"}, {"HCMM", "MGQ"}, {"HCMN", "BLW"}, {"HCMO", "CMO"}, {"HCMR", "GLK"}, {"HCMS", "CMS"},
    {"HCMU", "ERA"}, {"HCMV", "BUO"}, {"HDAM", "JIB"}, {"HDAS", "AII"}, {"HDMO", "MHI"}, {"HDOB", "OBC"},
    {"HDTJ", "TDJ"}, {"HEAL", "DBB"}, {"HEAR", "AAC"}, {"HEAT", "ATZ"}, {"HEAX", "HBE"}, {"HEBL", "ABS"},
    {"HEBR", "EES"}, {"HECA", "CAI"}, {"HECP", "CCE"}, {"HEDK", "DAK"}, {"HEGN", "HRG"}, {"HEGR", "EGH"},
    {"HEKG", "UVL"}, {"HELX", "LXR"}, {"HEMA", "RMF"}, {"HEMM", "MUH"}, {"HEOW", "GSQ"}, {"HEPS", "PSD"},
    {"HESC", "SKV"}, {"HESG", "HMB"}, {"HESH", "SSH"}, {"HESN", "ASW"}, {"HESX", "SPX"}, {"HETB", "TCP"},
    {"HETR", "ELT"}, {"HHAS", "ASM"}, {"HHMS", "MSW"}, {"HHSB", "ASA"}, {"HHTS", "TES"}, {"HJJJ", "JUB"},
    {"HKAM", "ASV"}, {"HKEL", "EDL"}, {"HKES", "EYS"}, {"HKFG", "KLK"}, {"HKGA", "GAS"}, {"HKHO", "HOA"},
    {"HKIU", "KIU"}, {"HKJK", "NBO"}, {"HKKE", "KEU"}, {"HKKG", "GGM"}, {"HKKI", "KIS"}, {"HKKL", "ILU"},
    {"HKKR", "KEY"}, {"HKKT", "KTL"}, {"HKLK", "LKG"}, {"HKLO", "LOK"}, {"HKLU", "LAU"}, {"HKLY", "LOY"},
    {"HKMA", "NDE"}, {"HKMB", "RBT"}, {"HKMK", "JJM"}, {"HKML", "MYD"}, {"HKMO", "MBA"}, {"HKMS", "MRE"},
    {"HKMY", "OYL"}, {"HKNI", "NYE"}, {"HKNK", "NUU"}, {"HKNL", "NYK"}, {"HKNW", "WIL"}, {"HKOK", "OLX"},
    {"HKOY", "OSJ"}, {"HKSB", "UAS"}, {"HKSJ", "MDR"}, {"HKUK", "UKA"}, {"HKWJ", "WJR"}, {"HKWY", "KWY"},
    {"HLGD", "SRX"}, {"HLGT", "GHT"}, {"HLKF", "AKF"}, {"HLLB", "BEN"}, {"HLLM", "MJI"}, {"HLLQ", "LAQ"},
    {"HLLS", "SEB"}, {"HLMB", "LMQ"}, {"HLMS", "MRA"}, {"HLNR", "NFR"}, {"HLON", "HUQ"}, {"HLTD", "LTD"},
    {"HLTQ", "TOB"}, {"HLUB", "QUB"}, {"HLZN", "ZIS"}, {"HLZW", "WAX"}, {"HRYG", "GYI"}, {"HRYI", "BTQ"},
    {"HRYR", "KGL"}, {"HRYU", "RHG"}, {"HRZA", "KME"}, {"HSAT", "ATB"}, {"HSDB", "EDB"}, {"HSDN", "DOG"},
    {"HSDZ", "RSS"}, {"HSFS", "ELF"}, {"HSGG", "DNX"}, {"HSGN", "EGN"}, {"HSHG", "HEG"}, {"HSKA", "KSL"},
    {"HSKG", "GBU"}, {"HSLI", "KDX"}, {"HSMN", "MWE"}, {"HSNH", "NUD"}, {"HSNN", "UYL"}, {"HSNW", "NHF"},
    {"HSOB", "EBD"}, {"HSPN", "PZU"}, {"HSSK", "KRT"}, {"HSSM", "MAK"}, {"HSSW", "WHF"}, {"HSWW", "WUU"},
    {"HSZA", "ZLX"}, {"HTAR", "ARK"}, {"HTBU", "BKZ"}, {"HTDA", "DAR"}, {"HTDO", "DOD"}, {"HTGE", "GTC"},
    {"HTGR", "GTZ"}, {"HTGW", "MBI"}, {"HTIR", "IRI"}, {"HTKA", "TKQ"}, {"HTKI", "KIY"}, {"HTKJ", "JRO"},
    {"HTLI", "LDI"}, {"HTLM", "LKY"}, {"HTMA", "MFA"}, {"HTMD", "MWN"}, {"HTMI", "XMI"}, {"HTMP", "NPY"},
    {"HTMS", "QSI"}, {"HTMT", "MYW"}, {"HTMU", "MUZ"}, {"HTMW", "MWZ"}, {"HTNA", "NCH"}, {"HTNJ", "JOM"},
    {"HTPE", "PMA"}, {"HTSN", "SEU"}, {"HTSO", "SGX"}, {"HTSU", "SUT"}, {"HTSY", "SHY"}, {"HTTB", "TBO"},
    {"HTTG", "TGT"}, {"HTZA", "ZNZ"}, {"HUAR", "RUA"}, {"HUEN", "EBB"}, {"HUGU", "ULU"}, {"HUJI", "JIN"},
    {"HUKI", "KXO"}, {"HUKS", "KSE"}, {"HUMA", "MBQ"}, {"HUMI", "KCU"}, {"HUPA", "PAF"}, {"HUSO", "SRT"},
    {"HUTO", "TRY"}, {"KAAF", "AAF"}, {"KABE", "ABE"}, {"KABI", "ABI"}, {"KABQ", "ABQ"}, {"KABR", "ABR"},
    {"KABY", "ABY"}, {"KACB", "ACB"}, {"KACK", "ACK"}, {"KACT", "ACT"}, {"KACV", "ACV"}, {"KACY", "ACY"},
    {"KADG", "ADG"}, {"KADH", "ADT"}, {"KADM", "ADM"}, {"KADS", "ADS"}, {"KADW", "ADW"}, {"KAEL", "AEL"},
    {"KAEX", "AEX"}, {"KAFF", "AFF"}, {"KAFJ", "WSG"}, {"KAFN", "AFN"}, {"KAFO", "AFO"}, {"KAFW", "AFW"},
    {"KAGC", "AGC"}, {"KAGO", "AGO"}, {"KAGS", "AGS"}, {"KAHC", "AHC"}, {"KAHH", "AHH"}, {"KAHN", "AHN"},
    {"KAIA", "AIA"}, {"KAID", "AID"}, {"KAIK", "AIK"}, {"KAIO", "AIO"}, {"KAIV", "AIV"}, {"KAIZ", "AIZ"},
    {"KAKO", "AKO"}, {"KAKR", "AKC"}, {"KALB", "ALB"}, {"KALI", "ALI"}, {"KALM", "ALM"}, {"KALN", "ALN"},
    {"KALO", "ALO"}, {"KALS", "ALS"}, {"KALW", "ALW"}, {"KALX", "ALX"}, {"KAMA", "AMA"}, {"KAMN", "AMN"},
    {"KAMW", "AMW"}, {"KANB", "ANB"}, {"KAND", "AND"}, {"KANK", "SLT"}, {"KANP", "ANP"}, {"KANQ", "ANQ"},
    {"KANW", "ANW"}, {"KANY", "ANY"}, {"KAOH", "AOH"}, {"KAOO", "AOO"}, {"KAPA", "APA"}, {"KAPC", "APC"},
    {"KAPF", "APF"}, {"KAPG", "APG"}, {"KAPH", "APH"}, {"KAPN", "APN"}, {"KAPT", "APT"}, {"KAPV", "APV"},
    {"KARA", "ARA"}, {"KARB", "ARB"}, {"KARG", "ARG"}, {"KARM", "WHT"}, {"KARR", "AUZ"}, {"KART", "ART"},
    {"KARV", "ARV"}, {"KARW", "BFT"}, {"KASE", "ASE"}, {"KASG", "SPZ"}, {"KASH", "ASH"}, {"KASL", "ASL"},
    {"KASN", "ASN"}, {"KAST", "AST"}, {"KASX", "ASX"}, {"KASY", "ASY"}, {"KATL", "ATL"}, {"KATS", "ATS"},
    {"KATW", "ATW"}, {"KATY", "ATY"}, {"KAUG", "AUG"}, {"KAUM", "AUM"}, {"KAUN", "AUN"}, {"KAUO", "AUO"},
    {"KAUS", "AUS"}, {"KAUW", "AUW"}, {"KAVL", "AVL"}, {"KAVO", "AVO"}, {"KAVP", "AVP"}, {"KAVQ", "AVW"},
    {"KAVX", "AVX"}, {"KAWM", "AWM"}, {"KAXA", "AXG"}, {"KAXN", "AXN"}, {"KAXS", "AXS"}, {"KAXV", "AXV"},
    {"KAXX", "AXX"}, {"KAYS", "AYS"}, {"KAZO", "AZO"}, {"KBAB", "BAB"}, {"KBAD", "BAD"}, {"KBAF", "BAF"},
    {"KBAK", "CLU"}, {"KBAM", "BAM"}, {"KBBB", "BBB"}, {"KBBD", "BBD"}, {"KBBG", "BKG"}, {"KBBP", "BTN"},
    {"KBBW", "BBW"}, {"KBCB", "BCB"}, {"KBCE", "BCE"}, {"KBCT", "BCT"}, {"KBDE", "BDE"}, {"KBDG", "BDG"},
    {"KBDH", "ILL"}, {"KBDL", "BDL"}, {"KBDR", "BDR"}, {"KBDU", "WBU"}, {"KBEC", "BEC"}, {"KBED", "BED"},
    {"KBEH", "BEH"}, {"KBFD", "BFD"}, {"KBFF", "BFF"}, {"KBFI", "BFI"}, {"KBFL", "BFL"}, {"KBFM", "BFM"},
    {"KBFR", "BFR"}, {"KBGD", "BGD"}, {"KBGE", "BGE"}, {"KBGM", "BGM"}, {"KBGR", "BGR"}, {"KBHB", "BHB"},
    {"KBHM", "BHM"}, {"KBID", "BID"}, {"KBIE", "BIE"}, {"KBIF", "BIF"}, {"KBIH", "BIH"}, {"KBIL", "BIL"},
    {"KBIS", "BIS"}, {"KBIX", "BIX"}, {"KBJC", "BJC"}, {"KBJI", "BJI"}, {"KBJJ", "BJJ"}, {"KBKD", "BKD"},
    {"KBKE", "BKE"}, {"KBKF", "BFK"}, {"KBKL", "BKL"}, {"KBKN", "BWL"}, {"KBKT", "BKT"}, {"KBKW", "BKW"},
    {"KBKX", "BKX"}, {"KBLF", "BLF"}, {"KBLH", "BLH"}, {"KBLI", "BLI"}, {"KBLM", "BLM"}, {"KBLU", "BLU"},
    {"KBLV", "BLV"}, {"KBMC", "BMC"}, {"KBMG", "BMG"}, {"KBMI", "BMI"}, {"KBML", "BML"}, {"KBMT", "BMT"},
    {"KBNA", "BNA"}, {"KBNG", "BNG"}, {"KBNL", "BNL"}, {"KBNO", "BNO"}, {"KBNW", "BNW"}, {"KBOI", "BOI"},
    {"KBOK", "BOK"}, {"KBOS", "BOS"}, {"KBOW", "BOW"}, {"KBPD", "XFT"}, {"KBPG", "HCA"}, {"KBPI", "BPI"},
    {"KBPK", "WMH"}, {"KBPT", "BPT"}, {"KBQK", "BQK"}, {"KBRD", "BRD"}, {"KBRL", "BRL"}, {"KBRO", "BRO"},
    {"KBRY", "BRY"}, {"KBTF", "BTF"}, {"KBTL", "BTL"}, {"KBTM", "BTM"}, {"KBTN", "TTO"}, {"KBTP", "BTP"},
    {"KBTR", "BTR"}, {"KBTV", "BTV"}, {"KBTY", "BTY"}, {"KBUB", "BUB"}, {"KBUF", "BUF"}, {"KBUM", "BUM"},
    {"KBUR", "BUR"}, {"KBVI", "BFP"}, {"KBVO", "BVO"}, {"KBVS", "MVW"}, {"KBVU", "BLD"}, {"KBVX", "BVX"},
    {"KBVY", "BVY"}, {"KBWC", "BWC"}, {"KBWD", "BWD"}, {"KBWG", "BWG"}, {"KBWI", "BWI"}, {"KBWP", "WAH"},
    {"KBXA", "BXA"}, {"KBXK", "BXK"}, {"KBXM", "NHZ"}, {"KBYG", "BYG"}, {"KBYH", "BYH"}, {"KBYI", "BYI"},
    {"KBYS", "BYS"}, {"KBYY", "BBC"}, {"KBZN", "BZN"}, {"KCAD", "CAD"}, {"KCAE", "CAE"}, {"KCAG", "CIG"},
    {"KCAK", "CAK"}, {"KCAO", "CAO"}, {"KCAR", "CAR"}, {"KCBE", "CBE"}, {"KCBF", "CBF"}, {"KCBK", "CBK"},
    {"KCBM", "CBM"}, {"KCCB", "CCB"}, {"KCCR", "CCR"}, {"KCCY", "CCY"}, {"KCDA", "LLX"}, {"KCDC", "CDC"},
    {"KCDH", "CDH"}, {"KCDK", "CDK"}, {"KCDN", "CDN"}, {"KCDR", "CDR"}, {"KCDS", "CDS"}, {"KCDW", "CDW"},
    {"KCEA", "CEA"}, {"KCEC", "CEC"}, {"KCEU", "CEU"}, {"KCEV", "CEV"}, {"KCEW", "CEW"}, {"KCEY", "CEY"},
    {"KCEZ", "CEZ"}, {"KCFD", "CFD"}, {"KCFS", "TZC"}, {"KCFT", "CFT"}, {"KCFV", "CFV"}, {"KCGE", "CGE"},
    {"KCGF", "CGF"}, {"KCGI", "CGI"}, {"KCGS", "CGS"}, {"KCGZ", "CGZ"}, {"KCHA", "CHA"}, {"KCHK", "CHK"},
    {"KCHO", "CHO"}, {"KCHS", "CHS"}, {"KCIC", "CIC"}, {"KCID", "CID"}, {"KCIN", "CIN"}, {"KCIR", "CIR"},
    {"KCIU", "CIU"}, {"KCKA", "CKA"}, {"KCKB", "CKB"}, {"KCKC", "GRM"}, {"KCKM", "CKM"}, {"KCKN", "CKN"},
    {"KCKV", "CKV"}, {"KCLE", "CLE"}, {"KCLI", "CLI"}, {"KCLK", "CLK"}, {"KCLL", "CLL"}, {"KCLM", "CLM"},
    {"KCLR", "CLR"}, {"KCLS", "CLS"}, {"KCLT", "CLT"}, {"KCLW", "CLW"}, {"KCMH", "CMH"}, {"KCMI", "CMI"},
    {"KCMX", "CMX"}, {"KCMY", "CMY"}, {"KCNH", "CNH"}, {"KCNK", "CNK"}, {"KCNM", "CNM"}, {"KCNO", "CNO"},
    {"KCNU", "CNU"}, {"KCNW", "CNW"}, {"KCNY", "CNY"}, {"KCOD", "COD"}, {"KCOE", "COE"}, {"KCOF", "COF"},
    {"KCOI", "COI"}, {"KCOM", "COM"}, {"KCON", "CON"}, {"KCOS", "COS"}, {"KCOT", "COT"}, {"KCOU", "COU"},
    {"KCPM", "CPM"}, {"KCPR", "CPR"}, {"KCPS", "CPS"}, {"KCQW", "HCW"}, {"KCRE", "CRE"}, {"KCRG", "CRG"},
    {"KCRP", "CRP"}, {"KCRQ", "CLD"}, {"KCRS", "CRS"}, {"KCRT", "CRT"}, {"KCRW", "CRW"}, {"KCRX", "CRX"},
    {"KCSG", "CSG"}, {"KCSM", "CSM"}, {"KCSQ", "CSQ"}, {"KCSV", "CSV"}, {"KCTB", "CTB"}, {"KCTY", "CTY"},
    {"KCTZ", "CTZ"}, {"KCUB", "CUB"}, {"KCUH", "CUH"}, {"KCVG", "CVG"}, {"KCVH", "HLI"}, {"KCVK", "CKK"},
    {"KCVN", "CVN"}, {"KCVO", "CVO"}, {"KCVS", "CVS"}, {"KCWA", "CWA"}, {"KCWC", "KIP"}, {"KCWF", "CWF"},
    {"KCWI", "CWI"}, {"KCXL", "CXL"}, {"KCXO", "CXO"}, {"KCXP", "CSN"}, {"KCXY", "HAR"}, {"KCYS", "CYS"},
    {"KCZK", "CZK"}, {"KCZT", "CZT"}, {"KDAA", "DAA"}, {"KDAB", "DAB"}, {"KDAG", "DAG"}, {"KDAL", "DAL"},
    {"KDAN", "DAN"}, {"KDAY", "DAY"}, {"KDBN", "DBN"}, {"KDBQ", "DBQ"}, {"KDCA", "DCA"}, {"KDCU", "DCU"},
    {"KDDC", "DDC"}, {"KDEC", "DEC"}, {"KDEH", "DEH"}, {"KDEN", "DEN"}, {"KDFI", "DFI"}, {"KDFW", "DFW"},
    {"KDGL", "DGL"}, {"KDGW", "DGW"}, {"KDHN", "DHN"}, {"KDHT", "DHT"}, {"KDIK", "DIK"}, {"KDJT", "PBI"},
    {"KDKK", "DKK"}, {"KDLC", "DLL"}, {"KDLF", "DLF"}, {"KDLH", "DLH"}, {"KDLN", "DLN"}, {"KDLS", "DLS"},
    {"KDMA", "DMA"}, {"KDMN", "DMN"}, {"KDMO", "DMO"}, {"KDNL", "DNL"}, {"KDNN", "DNN"}, {"KDNS", "DNS"},
    {"KDNV", "DNV"}, {"KDOV", "DOV"}, {"KDPA", "DPA"}, {"KDPG", "DPG"}, {"KDRA", "DRA"}, {"KDRI", "DRI"},
    {"KDRM", "DRE"}, {"KDRO", "DRO"}, {"KDRT", "DRT"}, {"KDSM", "DSM"}, {"KDSV", "DSV"}, {"KDTA", "DTA"},
    {"KDTL", "DTL"}, {"KDTN", "DTN"}, {"KDTS", "DSI"}, {"KDTW", "DTW"}, {"KDUA", "DUA"}, {"KDUC", "DUC"},
    {"KDUG", "DUG"}, {"KDUJ", "DUJ"}, {"KDVL", "DVL"}, {"KDVN", "DVN"}, {"KDVO", "NOT"}, {"KDVP", "NSL"},
    {"KDVT", "DVT"}, {"KDWH", "DWH"}, {"KDXR", "DXR"}, {"KDYL", "DYL"}, {"KDYS", "DYS"}, {"KEAN", "EAN"},
    {"KEAR", "EAR"}, {"KEAT", "EAT"}, {"KEAU", "EAU"}, {"KEBS", "EBS"}, {"KECG", "ECG"}, {"KECP", "ECP"},
    {"KECS", "ECS"}, {"KEDE", "EDE"}, {"KEDN", "ETS"}, {"KEDW", "EDW"}, {"KEED", "EED"}, {"KEEN", "EEN"},
    {"KEFD", "EFD"}, {"KEFK", "EFK"}, {"KEFW", "EFW"}, {"KEGE", "EGE"}, {"KEGI", "EGI"}, {"KEGV", "EGV"},
    {"KEKA", "EKA"}, {"KEKM", "EKI"}, {"KEKN", "EKN"}, {"KEKO", "EKO"}, {"KEKX", "EKX"}, {"KELA", "ELA"},
    {"KELD", "ELD"}, {"KELK", "ELK"}, {"KELM", "ELM"}, {"KELN", "ELN"}, {"KELO", "LYU"}, {"KELP", "ELP"},
    {"KELY", "ELY"}, {"KELZ", "ELZ"}, {"KEMM", "EMM"}, {"KEMP", "EMP"}, {"KEMT", "EMT"}, {"KEND", "END"},
    {"KENL", "ENL"}, {"KENV", "ENV"}, {"KENW", "ENW"}, {"KEOK", "EOK"}, {"KEOS", "EOS"}, {"KEPH", "EPH"},
    {"KEQA", "EDK"}, {"KERI", "ERI"}, {"KERR", "ERR"}, {"KERV", "ERV"}, {"KESC", "ESC"}, {"KESF", "ESF"},
    {"KESN", "ESN"}, {"KEST", "EST"}, {"KESW", "ESW"}, {"KETB", "ETB"}, {"KETN", "ETN"}, {"KEUF", "EUF"},
    {"KEUG", "EUG"}, {"KEVM", "EVM"}, {"KEVV", "EVV"}, {"KEVW", "EVW"}, {"KEWB", "EWB"}, {"KEWK", "EWK"},
    {"KEWN", "EWN"}, {"KEWR", "EWR"}, {"KEYW", "EYW"}, {"KFAF", "FAF"}, {"KFAM", "FAM"}, {"KFAR", "FAR"},
    {"KFAT", "FAT"}, {"KFAY", "FAY"}, {"KFBG", "FBG"}, {"KFBL", "FBL"}, {"KFBR", "FBR"}, {"KFBY", "FBY"},
    {"KFCH", "FCH"}, {"KFCM", "FCM"}, {"KFCS", "FCS"}, {"KFCY", "FCY"}, {"KFDK", "FDK"}, {"KFDR", "FDR"},
    {"KFDY", "FDY"}, {"KFEP", "FEP"}, {"KFET", "FET"}, {"KFFA", "FFA"}, {"KFFL", "FFL"}, {"KFFM", "FFM"},
    {"KFFO", "FFO"}, {"KFFT", "FFT"}, {"KFFZ", "MSC"}, {"KFHR", "FRD"}, {"KFHU", "FHU"}, {"KFKL", "FKL"},
    {"KFKN", "FKN"}, {"KFLD", "FLD"}, {"KFLG", "FLG"}, {"KFLL", "FLL"}, {"KFLO", "FLO"}, {"KFLP", "FLP"},
    {"KFLV", "FLV"}, {"KFLX", "FLX"}, {"KFME", "FME"}, {"KFMH", "FMH"}, {"KFMN", "FMN"}, {"KFMY", "FMY"},
    {"KFNL", "FNL"}, {"KFNT", "FNT"}, {"KFOD", "FOD"}, {"KFOE", "FOE"}, {"KFOK", "FOK"}, {"KFOM", "FIL"},
    {"KFPR", "FPR"}, {"KFRG", "FRG"}, {"KFRH", "FRH"}, {"KFRI", "FRI"}, {"KFRM", "FRM"}, {"KFRR", "FRR"},
    {"KFSD", "FSD"}, {"KFSI", "FSI"}, {"KFSK", "FSK"}, {"KFSM", "FSM"}, {"KFST", "FST"}, {"KFSU", "FSU"},
    {"KFSW", "FMS"}, {"KFTK", "FTK"}, {"KFTW", "FTW"}, {"KFTY", "FTY"}, {"KFUL", "FUL"}, {"KFVE", "WFK"},
    {"KFWA", "FWA"}, {"KFXE", "FXE"}, {"KFXY", "FXY"}, {"KFYM", "FYM"}, {"KFYV", "FYV"}, {"KGAB", "GAB"},
    {"KGAD", "GAD"}, {"KGAG", "GAG"}, {"KGAI", "GAI"}, {"KGBD", "GBD"}, {"KGBG", "GBG"}, {"KGBR", "GBR"},
    {"KGCC", "GCC"}, {"KGCD", "JDA"}, {"KGCK", "GCK"}, {"KGCN", "GCN"}, {"KGCY", "GCY"}, {"KGDM", "GDM"},
    {"KGDV", "GDV"}, {"KGDW", "GDW"}, {"KGED", "GED"}, {"KGEG", "GEG"}, {"KGEY", "GEY"}, {"KGFD", "GFD"},
    {"KGFK", "GFK"}, {"KGFL", "GFL"}, {"KGGE", "GGE"}, {"KGGG", "GGG"}, {"KGGW", "GGW"}, {"KGHM", "GHM"},
    {"KGIC", "IDH"}, {"KGIF", "GIF"}, {"KGJT", "GJT"}, {"KGKJ", "MEJ"}, {"KGKT", "GKT"}, {"KGLD", "GLD"},
    {"KGLE", "GLE"}, {"KGLH", "GLH"}, {"KGLR", "GLR"}, {"KGLS", "GLS"}, {"KGLW", "GLW"}, {"KGMU", "GMU"},
    {"KGNG", "GNG"}, {"KGNT", "GNT"}, {"KGNV", "GNV"}, {"KGOK", "GOK"}, {"KGON", "GON"}, {"KGPI", "FCA"},
    {"KGPT", "GPT"}, {"KGPZ", "GPZ"}, {"KGQQ", "GQQ"}, {"KGRB", "GRB"}, {"KGRD", "GRD"}, {"KGRE", "GRE"},
    {"KGRF", "GRF"}, {"KGRI", "GRI"}, {"KGRK", "GRK"}, {"KGRN", "GRN"}, {"KGRR", "GRR"}, {"KGSB", "GSB"},
    {"KGSH", "GSH"}, {"KGSO", "GSO"}, {"KGSP", "GSP"}, {"KGTF", "GTF"}, {"KGTG", "GTG"}, {"KGTR", "GTR"},
    {"KGUC", "GUC"}, {"KGUP", "GUP"}, {"KGUS", "GUS"}, {"KGUY", "GUY"}, {"KGVE", "GVE"}, {"KGVL", "GVL"},
    {"KGVT", "GVT"}, {"KGWO", "GWO"}, {"KGWS", "GWS"}, {"KGXY", "GXY"}, {"KGYH", "GDC"}, {"KGYI", "PNX"},
    {"KGYR", "GYR"}, {"KGYY", "GYY"}, {"KHAB", "HAB"}, {"KHAF", "HAF"}, {"KHAI", "HAI"}, {"KHAO", "HAO"},
    {"KHBG", "HBG"}, {"KHBR", "HBR"}, {"KHDE", "HDE"}, {"KHDN", "HDN"}, {"KHEE", "HEE"}, {"KHEF", "MNZ"},
    {"KHEZ", "HEZ"}, {"KHFD", "HFD"}, {"KHFF", "HFF"}, {"KHGR", "HGR"}, {"KHHR", "HHR"}, {"KHHW", "HUJ"},
    {"KHIB", "HIB"}, {"KHIE", "HIE"}, {"KHIF", "HIF"}, {"KHII", "HII"}, {"KHIO", "HIO"}, {"KHKA", "HKA"},
    {"KHKS", "HKS"}, {"KHKY", "HKY"}, {"KHLB", "HLB"}, {"KHLC", "HLC"}, {"KHLG", "HLG"}, {"KHLN", "HLN"},
    {"KHLR", "HLR"}, {"KHMN", "HMN"}, {"KHMT", "HMT"}, {"KHNB", "HNB"}, {"KHND", "HSH"}, {"KHOB", "HOB"},
    {"KHON", "HON"}, {"KHOP", "HOP"}, {"KHOT", "HOT"}, {"KHOU", "HOU"}, {"KHPN", "HPN"}, {"KHPT", "HPT"},
    {"KHPY", "HPY"}, {"KHQM", "HQM"}, {"KHRI", "HES"}, {"KHRL", "HRL"}, {"KHRO", "HRO"}, {"KHSB", "HSB"},
    {"KHSE", "HNC"}, {"KHSI", "HSI"}, {"KHSP", "HSP"}, {"KHST", "HST"}, {"KHSV", "HSV"}, {"KHTH", "HTH"},
    {"KHTL", "HTL"}, {"KHTS", "HTS"}, {"KHTW", "HTW"}, {"KHUA", "HUA"}, {"KHUL", "HUL"}, {"KHUM", "HUM"},
    {"KHUT", "HUT"}, {"KHVE", "HVE"}, {"KHVN", "HVN"}, {"KHVR", "HVR"}, {"KHVS", "HVS"}, {"KHWD", "HWD"},
    {"KHWO", "HWO"}, {"KHWV", "WSH"}, {"KHXD", "HHH"}, {"KHYA", "HYA"}, {"KHYR", "HYR"}, {"KHYS", "HYS"},
    {"KHZL", "HZL"}, {"KHZY", "JFN"}, {"KIAB", "IAB"}, {"KIAD", "IAD"}, {"KIAG", "IAG"}, {"KIAH", "IAH"},
    {"KICL", "ICL"}, {"KICT", "ICT"}, {"KIDA", "IDA"}, {"KIDG", "IDG"}, {"KIDI", "IDI"}, {"KIDP", "IDP"},
    {"KIEN", "XPR"}, {"KIFA", "IFA"}, {"KIFP", "IFP"}, {"KIGM", "IGM"}, {"KIJX", "IJX"}, {"KIKK", "IKK"},
    {"KILE", "ILE"}, {"KILG", "ILG"}, {"KILM", "ILM"}, {"KILN", "ILN"}, {"KIML", "IML"}, {"KIMM", "IMM"},
    {"KIMS", "MDN"}, {"KIMT", "IMT"}, {"KIND", "IND"}, {"KINK", "INK"}, {"KINL", "INL"}, {"KINS", "INS"},
    {"KINT", "INT"}, {"KINW", "INW"}, {"KIOW", "IOW"}, {"KIPL", "IPL"}, {"KIPT", "IPT"}, {"KIRK", "IRK"},
    {"KIRS", "IRS"}, {"KISM", "ISM"}, {"KISO", "ISO"}, {"KISP", "ISP"}, {"KISQ", "ISQ"}, {"KISW", "ISW"},
    {"KITH", "ITH"}, {"KIWA", "AZA"}, {"KIWD", "IWD"}, {"KIWI", "ISS"}, {"KIWS", "IWS"}, {"KIXD", "JCI"},
    {"KIYK", "IYK"}, {"KIZA", "SQA"}, {"KIZG", "FRY"}, {"KJAC", "JAC"}, {"KJAN", "JAN"}, {"KJAS", "JAS"},
    {"KJAX", "JAX"}, {"KJBR", "JBR"}, {"KJCT", "JCT"}, {"KJDN", "JDN"}, {"KJEF", "JEF"}, {"KJFK", "JFK"},
    {"KJHW", "JHW"}, {"KJKA", "GUF"}, {"KJLN", "JLN"}, {"KJMS", "JMS"}, {"KJOT", "JOT"}, {"KJPX", "HTO"},
    {"KJQF", "USA"}, {"KJSO", "JKV"}, {"KJST", "JST"}, {"KJVL", "JVL"}, {"KJXN", "JXN"}, {"KKIC", "KIC"},
    {"KKLS", "KLS"}, {"KKNB", "KNB"}, {"KLAA", "LAA"}, {"KLAF", "LAF"}, {"KLAL", "LAL"}, {"KLAM", "LAM"},
    {"KLAN", "LAN"}, {"KLAR", "LAR"}, {"KLAS", "LAS"}, {"KLAW", "LAW"}, {"KLAX", "LAX"}, {"KLBB", "LBB"},
    {"KLBE", "LBE"}, {"KLBF", "LBF"}, {"KLBL", "LBL"}, {"KLBT", "LBT"}, {"KLBX", "LJN"}, {"KLCH", "LCH"},
    {"KLCI", "LCI"}, {"KLCK", "LCK"}, {"KLCQ", "LCQ"}, {"KLDJ", "LDJ"}, {"KLDM", "LDM"}, {"KLEB", "LEB"},
    {"KLEE", "LEE"}, {"KLEM", "LEM"}, {"KLEW", "LEW"}, {"KLEX", "LEX"}, {"KLFI", "LFI"}, {"KLFK", "LFK"},
    {"KLFT", "LFT"}, {"KLGA", "LGA"}, {"KLGB", "LGB"}, {"KLGC", "LGC"}, {"KLGD", "LGD"}, {"KLGF", "LGF"},
    {"KLGU", "LGU"}, {"KLHV", "LHV"}, {"KLHW", "LIY"}, {"KLHZ", "LFN"}, {"KLIC", "LIC"}, {"KLIT", "LIT"},
    {"KLKP", "LKP"}, {"KLKU", "LOW"}, {"KLKV", "LKV"}, {"KLLJ", "CHL"}, {"KLMS", "LMS"}, {"KLMT", "LMT"},
    {"KLNA", "LNA"}, {"KLND", "LND"}, {"KLNK", "LNK"}, {"KLNN", "LNN"}, {"KLNP", "LNP"}, {"KLNR", "LNR"},
    {"KLNS", "LNS"}, {"KLOL", "LOL"}, {"KLOM", "BBX"}, {"KLOT", "LOT"}, {"KLOU", "LOU"}, {"KLOZ", "LOZ"},
    {"KLPC", "LPC"}, {"KLQK", "LQK"}, {"KLRD", "LRD"}, {"KLRF", "LRF"}, {"KLRJ", "LRJ"}, {"KLRU", "LRU"},
    {"KLSB", "LSB"}, {"KLSE", "LSE"}, {"KLSF", "LSF"}, {"KLSK", "LSK"}, {"KLSN", "LSN"}, {"KLSV", "LSV"},
    {"KLTS", "LTS"}, {"KLUF", "LUF"}, {"KLUK", "LUK"}, {"KLUL", "LUL"}, {"KLVK", "LVK"}, {"KLVL", "LVL"},
    {"KLVM", "LVM"}, {"KLVS", "LVS"}, {"KLWB", "LWB"}, {"KLWC", "LWC"}, {"KLWL", "LWL"}, {"KLWM", "LWM"},
    {"KLWS", "LWS"}, {"KLWT", "LWT"}, {"KLWV", "LWV"}, {"KLXN", "LXN"}, {"KLXV", "LXV"}, {"KLYH", "LYH"},
    {"KLYO", "LYO"}, {"KLZU", "LZU"}, {"KMAC", "MAC"}, {"KMAE", "MAE"}, {"KMAF", "MAF"}, {"KMAW", "MAW"},
    {"KMBG", "MBG"}, {"KMBL", "MBL"}, {"KMBO", "DXE"}, {"KMBS", "MBS"}, {"KMBY", "MBY"}, {"KMCB", "MCB"},
    {"KMCC", "MCC"}, {"KMCD", "MCD"}, {"KMCE", "MCE"}, {"KMCF", "MCF"}, {"KMCI", "MCI"}, {"KMCK", "MCK"},
    {"KMCN", "MCN"}, {"KMCO", "MCO"}, {"KMCW", "MCW"}, {"KMDD", "MDD"}, {"KMDH", "MDH"}, {"KMDS", "XMD"},
    {"KMDT", "MDT"}, {"KMDW", "MDW"}, {"KMDZ", "MDF"}, {"KMEB", "MXE"}, {"KMEI", "MEI"}, {"KMEM", "MEM"},
    {"KMER", "MER"}, {"KMEV", "MEV"}, {"KMFD", "MFD"}, {"KMFE", "MFE"}, {"KMFI", "MFI"}, {"KMFR", "MFR"},
    {"KMFV", "MFV"}, {"KMGC", "MGC"}, {"KMGE", "MGE"}, {"KMGJ", "MGJ"}, {"KMGM", "MGM"}, {"KMGR", "MGR"},
    {"KMGW", "MGW"}, {"KMGY", "MGY"}, {"KMHE", "MHE"}, {"KMHK", "MHK"}, {"KMHL", "MHL"}, {"KMHR", "MHR"},
    {"KMHT", "MHT"}, {"KMHV", "MHV"}, {"KMIA", "MIA"}, {"KMIB", "MIB"}, {"KMIC", "MIC"}, {"KMIE", "MIE"},
    {"KMIO", "MIO"}, {"KMIT", "MIT"}, {"KMIV", "MIV"}, {"KMIW", "MIW"}, {"KMJQ", "MJQ"}, {"KMJX", "MJX"},
    {"KMKC", "MKC"}, {"KMKE", "MKE"}, {"KMKG", "MKG"}, {"KMKL", "MKL"}, {"KMKO", "MKO"}, {"KMKT", "MKT"},
    {"KMKY", "MRK"}, {"KMLB", "MLB"}, {"KMLC", "MLC"}, {"KMLD", "MLD"}, {"KMLE", "MIQ"}, {"KMLF", "MLF"},
    {"KMLI", "MLI"}, {"KMLJ", "MLJ"}, {"KMLS", "MLS"}, {"KMLT", "MLT"}, {"KMLU", "MLU"}, {"KMMH", "MMH"},
    {"KMMI", "MMI"}, {"KMML", "MML"}, {"KMMS", "MMS"}, {"KMMT", "MMT"}, {"KMMU", "MMU"}, {"KMNM", "MNM"},
    {"KMNN", "MNN"}, {"KMOB", "MOB"}, {"KMOD", "MOD"}, {"KMOP", "MOP"}, {"KMOR", "MOR"}, {"KMOT", "MOT"},
    {"KMOX", "MOX"}, {"KMPI", "RMY"}, {"KMPJ", "MPJ"}, {"KMPO", "MPO"}, {"KMPR", "MPR"}, {"KMPV", "MPV"},
    {"KMPZ", "MPZ"}, {"KMQB", "MQB"}, {"KMQI", "MEO"}, {"KMQS", "CTH"}, {"KMQW", "MQW"}, {"KMQY", "MQY"},
    {"KMRB", "MRB"}, {"KMRC", "MRC"}, {"KMRF", "MRF"}, {"KMRN", "MRN"}, {"KMRY", "MRY"}, {"KMSL", "MSL"},
    {"KMSN", "MSN"}, {"KMSO", "MSO"}, {"KMSP", "MSP"}, {"KMSS", "MSS"}, {"KMSV", "MSV"}, {"KMSY", "MSY"},
    {"KMTC", "MTC"}, {"KMTH", "MTH"}, {"KMTJ", "MTJ"}, {"KMTN", "MTN"}, {"KMTO", "MTO"}, {"KMTP", "MTP"},
    {"KMTW", "MTW"}, {"KMUI", "MUI"}, {"KMUL", "MUL"}, {"KMUO", "MUO"}, {"KMUT", "MUT"}, {"KMVC", "MVC"},
    {"KMVE", "MVE"}, {"KMVL", "MVL"}, {"KMVN", "MVN"}, {"KMVY", "MVY"}, {"KMWA", "MWA"}, {"KMWC", "MWC"},
    {"KMWH", "MWH"}, {"KMWL", "MWL"}, {"KMWM", "MWM"}, {"KMWO", "MWO"}, {"KMXA", "MXA"}, {"KMXF", "MXF"},
    {"KMXO", "MXO"}, {"KMYF", "MYF"}, {"KMYL", "MYL"}, {"KMYR", "MYR"}, {"KMYV", "MYV"}, {"KMZJ", "MZJ"},
    {"KMZZ", "MZZ"}, {"KNBG", "NBG"}, {"KNBJ", "NHX"}, {"KNDY", "DGN"}, {"KNEL", "NEL"}, {"KNEN", "NEN"},
    {"KNEW", "NEW"}, {"KNFL", "NFL"}, {"KNFW", "FWH"}, {"KNGP", "NGP"}, {"KNGU", "NGU"}, {"KNGW", "NGW"},
    {"KNHK", "NHK"}, {"KNIP", "NIP"}, {"KNJK", "NJK"}, {"KNKX", "NKX"}, {"KNLC", "NLC"}, {"KNPA", "NPA"},
    {"KNQA", "NQA"}, {"KNQI", "NQI"}, {"KNQX", "NQX"}, {"KNRB", "NRB"}, {"KNRS", "NRS"}, {"KNSE", "NSE"},
    {"KNTD", "NTD"}, {"KNTU", "NTU"}, {"KNUQ", "NUQ"}, {"KNUW", "NUW"}, {"KNVD", "NVD"}, {"KNYG", "NYG"},
    {"KNYL", "YUM"}, {"KNZY", "NZY"}, {"KOAJ", "OAJ"}, {"KOAK", "OAK"}, {"KOAR", "OAR"}, {"KOBE", "OBE"},
    {"KOCF", "OCF"}, {"KOCH", "OCH"}, {"KOCW", "OCW"}, {"KOEO", "OEO"}, {"KOFF", "OFF"}, {"KOFK", "OFK"},
    {"KOGA", "OGA"}, {"KOGB", "OGB"}, {"KOGD", "OGD"}, {"KOGS", "OGS"}, {"KOIC", "OIC"}, {"KOJC", "OJC"},
    {"KOKB", "OCN"}, {"KOKC", "OKC"}, {"KOKH", "ODW"}, {"KOKK", "OKK"}, {"KOKM", "OKM"}, {"KOKS", "OKS"},
    {"KOKV", "WGO"}, {"KOLD", "OLD"}, {"KOLE", "OLE"}, {"KOLF", "OLF"}, {"KOLM", "OLM"}, {"KOLS", "OLS"},
    {"KOLU", "OLU"}, {"KOLV", "OLV"}, {"KOLY", "OLY"}, {"KOMA", "OMA"}, {"KOMK", "OMK"}, {"KONA", "ONA"},
    {"KONL", "ONL"}, {"KONM", "ONM"}, {"KONO", "ONO"}, {"KONP", "ONP"}, {"KONT", "ONT"}, {"KONY", "ONY"},
    {"KOOA", "OOA"}, {"KOPF", "OPF"}, {"KOPL", "OPL"}, {"KOQU", "NCO"}, {"KORD", "ORD"}, {"KORF", "ORF"},
    {"KORH", "ORH"}, {"KORL", "ORL"}, {"KORS", "ESD"}, {"KOSA", "MPS"}, {"KOSC", "OSC"}, {"KOSH", "OSH"},
    {"KOSU", "OSU"}, {"KOSX", "OSX"}, {"KOTG", "OTG"}, {"KOTH", "OTH"}, {"KOTM", "OTM"}, {"KOUN", "OUN"},
    {"KOVE", "OVE"}, {"KOWA", "OWA"}, {"KOWB", "OWB"}, {"KOWD", "OWD"}, {"KOWK", "OWK"}, {"KOXB", "OCE"},
    {"KOXC", "OXC"}, {"KOXD", "OXD"}, {"KOXR", "OXR"}, {"KOYM", "STQ"}, {"KOZA", "OZA"}, {"KOZR", "OZR"},
    {"KPAE", "PAE"}, {"KPAH", "PAH"}, {"KPAM", "PAM"}, {"KPAN", "PJB"}, {"KPAO", "PAO"}, {"KPBF", "PBF"},
    {"KPBG", "PBG"}, {"KPBX", "PVL"}, {"KPDC", "PCD"}, {"KPDK", "PDK"}, {"KPDT", "PDT"}, {"KPDX", "PDX"},
    {"KPEQ", "PEQ"}, {"KPFC", "PFC"}, {"KPGA", "PGA"}, {"KPGD", "PGD"}, {"KPGR", "PGR"}, {"KPGV", "PGV"},
    {"KPHD", "PHD"}, {"KPHF", "PHF"}, {"KPHH", "ADR"}, {"KPHK", "PHK"}, {"KPHL", "PHL"}, {"KPHN", "PHN"},
    {"KPHP", "PHP"}, {"KPHT", "PHT"}, {"KPHX", "PHX"}, {"KPIA", "PIA"}, {"KPIB", "PIB"}, {"KPIE", "PIE"},
    {"KPIH", "PIH"}, {"KPIM", "PIM"}, {"KPIR", "PIR"}, {"KPIT", "PIT"}, {"KPKB", "PKB"}, {"KPKD", "PKD"},
    {"KPKF", "PKF"}, {"KPLK", "PLK"}, {"KPLN", "PLN"}, {"KPLR", "PLR"}, {"KPMB", "PMB"}, {"KPMD", "PMD"},
    {"KPMH", "PMH"}, {"KPMP", "PPM"}, {"KPNA", "PWY"}, {"KPNC", "PNC"}, {"KPNE", "PNE"}, {"KPNN", "PNN"},
    {"KPNS", "PNS"}, {"KPOB", "POB"}, {"KPOC", "POC"}, {"KPOE", "POE"}, {"KPOF", "POF"}, {"KPOH", "POH"},
    {"KPOU", "POU"}, {"KPOY", "POY"}, {"KPPA", "PPA"}, {"KPPF", "PPF"}, {"KPPO", "LPO"}, {"KPQI", "PQI"},
    {"KPQL", "PGL"}, {"KPRB", "PRB"}, {"KPRC", "PRC"}, {"KPRO", "PRO"}, {"KPRX", "PRX"}, {"KPSB", "PSB"},
    {"KPSC", "PSC"}, {"KPSF", "PSF"}, {"KPSK", "PSK"}, {"KPSM", "PSM"}, {"KPSN", "PSN"}, {"KPSO", "PGO"},
    {"KPSP", "PSP"}, {"KPSX", "PSX"}, {"KPTB", "PTB"}, {"KPTK", "PTK"}, {"KPTN", "PTN"}, {"KPTS", "PTS"},
    {"KPTT", "PTT"}, {"KPTV", "PTV"}, {"KPTW", "PTW"}, {"KPUB", "PUB"}, {"KPUC", "PUC"}, {"KPUW", "PUW"},
    {"KPVC", "PVC"}, {"KPVD", "PVD"}, {"KPVF", "PVF"}, {"KPVU", "PVU"}, {"KPVW", "PVW"}, {"KPWA", "PWA"},
    {"KPWD", "PWD"}, {"KPWM", "PWM"}, {"KPWT", "PWT"}, {"KPYM", "PYM"}, {"KRAC", "RAC"}, {"KRAL", "RAL"},
    {"KRAP", "RAP"}, {"KRBD", "RBD"}, {"KRBG", "RBG"}, {"KRBL", "RBL"}, {"KRBW", "RBW"}, {"KRCA", "RCA"},
    {"KRCK", "RCK"}, {"KRCR", "RCR"}, {"KRDD", "RDD"}, {"KRDG", "RDG"}, {"KRDM", "RDM"}, {"KRDR", "RDR"},
    {"KRDU", "RDU"}, {"KREO", "REO"}, {"KRFD", "RFD"}, {"KRFG", "RFG"}, {"KRHI", "RHI"}, {"KRHV", "RHV"},
    {"KRIC", "RIC"}, {"KRID", "RID"}, {"KRIF", "RIF"}, {"KRIL", "RIL"}, {"KRIR", "RIR"}, {"KRIV", "RIV"},
    {"KRIW", "RIW"}, {"KRKD", "RKD"}, {"KRKP", "RKP"}, {"KRKR", "RKR"}, {"KRKS", "RKS"}, {"KRKW", "RKW"},
    {"KRLD", "RLD"}, {"KRME", "RME"}, {"KRMG", "RMG"}, {"KRNC", "RNC"}, {"KRND", "RND"}, {"KRNH", "RNH"},
    {"KRNO", "RNO"}, {"KRNT", "RNT"}, {"KROA", "ROA"}, {"KROC", "ROC"}, {"KROG", "ROG"}, {"KROW", "ROW"},
    {"KROX", "ROX"}, {"KRPD", "RIE"}, {"KRPX", "RPX"}, {"KRQB", "WBR"}, {"KRRL", "RRL"}, {"KRRT", "RRT"},
    {"KRSL", "RSL"}, {"KRSN", "RSN"}, {"KRST", "RST"}, {"KRSW", "RSW"}, {"KRTN", "RTN"}, {"KRUQ", "SRW"},
    {"KRUT", "RUT"}, {"KRVL", "RED"}, {"KRVS", "RVS"}, {"KRWF", "RWF"}, {"KRWI", "RWI"}, {"KRWL", "RWL"},
    {"KRXE", "RXE"}, {"KRZL", "RNZ"}, {"KSAA", "SAA"}, {"KSAC", "SAC"}, {"KSAD", "SAD"}, {"KSAF", "SAF"},
    {"KSAN", "SAN"}, {"KSAR", "SAR"}, {"KSAS", "SAS"}, {"KSAT", "SAT"}, {"KSAV", "SAV"}, {"KSAW", "MQT"},
    {"KSBA", "SBA"}, {"KSBD", "SBD"}, {"KSBM", "SBM"}, {"KSBN", "SBN"}, {"KSBP", "SBP"}, {"KSBS", "SBS"},
    {"KSBX", "SBX"}, {"KSBY", "SBY"}, {"KSCB", "SCB"}, {"KSCH", "SCH"}, {"KSCK", "SCK"}, {"KSDF", "SDF"},
    {"KSDL", "SCF"}, {"KSDM", "SDM"}, {"KSDY", "SDY"}, {"KSEA", "SEA"}, {"KSEE", "SEE"}, {"KSEF", "SEF"},
    {"KSEG", "SEG"}, {"KSEM", "SEM"}, {"KSEP", "SEP"}, {"KSER", "SER"}, {"KSEZ", "SDX"}, {"KSFB", "SFB"},
    {"KSFF", "SFF"}, {"KSFM", "SFM"}, {"KSFO", "SFO"}, {"KSFZ", "SFZ"}, {"KSGF", "SGF"}, {"KSGH", "SGH"},
    {"KSGJ", "UST"}, {"KSGR", "SGR"}, {"KSGT", "SGT"}, {"KSGU", "SGU"}, {"KSHD", "SHD"}, {"KSHN", "SHN"},
    {"KSHR", "SHR"}, {"KSHV", "SHV"}, {"KSIK", "SIK"}, {"KSIV", "SIV"}, {"KSIY", "SIY"}, {"KSJC", "SJC"},
    {"KSJN", "SJN"}, {"KSJT", "SJT"}, {"KSKA", "SKA"}, {"KSKF", "SKF"}, {"KSKX", "TSM"}, {"KSLB", "SLB"},
    {"KSLC", "SLC"}, {"KSLE", "SLE"}, {"KSLG", "SLG"}, {"KSLK", "SLK"}, {"KSLN", "SLN"}, {"KSLO", "SLO"},
    {"KSLR", "SLR"}, {"KSMD", "SMD"}, {"KSME", "SME"}, {"KSMF", "SMF"}, {"KSMN", "SMN"}, {"KSMO", "SMO"},
    {"KSMS", "SUM"}, {"KSMX", "SMX"}, {"KSNA", "SNA"}, {"KSNK", "SNK"}, {"KSNL", "SNL"}, {"KSNS", "SNS"},
    {"KSNY", "SNY"}, {"KSOP", "SOP"}, {"KSOW", "SOW"}, {"KSPA", "SPA"}, {"KSPF", "SPF"}, {"KSPG", "SPG"},
    {"KSPI", "SPI"}, {"KSPS", "SPS"}, {"KSPW", "SPW"}, {"KSQI", "SQI"}, {"KSQL", "SQL"}, {"KSRC", "SRC"},
    {"KSRQ", "SRQ"}, {"KSRR", "RUI"}, {"KSSC", "SSC"}, {"KSSF", "SSF"}, {"KSSI", "SSI"}, {"KSTC", "STC"},
    {"KSTE", "STE"}, {"KSTJ", "STJ"}, {"KSTK", "STK"}, {"KSTL", "STL"}, {"KSTP", "STP"}, {"KSTS", "STS"},
    {"KSUA", "SUA"}, {"KSUD", "SUD"}, {"KSUE", "SUE"}, {"KSUN", "SUN"}, {"KSUS", "SUS"}, {"KSUU", "SUU"},
    {"KSUW", "SUW"}, {"KSUX", "SUX"}, {"KSVC", "SVC"}, {"KSVE", "SVE"}, {"KSVH", "SVH"}, {"KSVN", "SVN"},
    {"KSWF", "SWF"}, {"KSWO", "SWO"}, {"KSWW", "SWW"}, {"KSYI", "SYI"}, {"KSYN", "SYN"}, {"KSYR", "SYR"},
    {"KSYV", "SYV"}, {"KSZL", "SZL"}, {"KSZN", "SZN"}, {"KSZP", "SZP"}, {"KTAD", "TAD"}, {"KTBN", "TBN"},
    {"KTBR", "TBR"}, {"KTCC", "TCC"}, {"KTCL", "TCL"}, {"KTCM", "TCM"}, {"KTCS", "TCS"}, {"KTDO", "TDO"},
    {"KTDW", "TDW"}, {"KTDZ", "TDZ"}, {"KTEB", "TEB"}, {"KTEX", "TEX"}, {"KTHA", "THA"}, {"KTHM", "THM"},
    {"KTHV", "THV"}, {"KTIK", "TIK"}, {"KTIW", "TIW"}, {"KTIX", "TIX"}, {"KTKI", "DTX"}, {"KTKX", "KNT"},
    {"KTLH", "TLH"}, {"KTLR", "TLR"}, {"KTMA", "TMA"}, {"KTMB", "TMB"}, {"KTMK", "OTK"}, {"KTNP", "TNP"},
    {"KTNT", "TNT"}, {"KTNU", "TNU"}, {"KTNX", "XSD"}, {"KTOA", "TOA"}, {"KTOC", "TOC"}, {"KTOI", "TOI"},
    {"KTOL", "TOL"}, {"KTOP", "TOP"}, {"KTOR", "TOR"}, {"KTPA", "TPA"}, {"KTPF", "TPF"}, {"KTPH", "TPH"},
    {"KTPL", "TPL"}, {"KTRI", "TRI"}, {"KTRK", "TKF"}, {"KTRL", "TRL"}, {"KTRM", "TRM"}, {"KTRX", "TRX"},
    {"KTSP", "TSP"}, {"KTTD", "TTD"}, {"KTTN", "TTN"}, {"KTUL", "TUL"}, {"KTUP", "TUP"}, {"KTUS", "TUS"},
    {"KTVC", "TVC"}, {"KTVF", "TVF"}, {"KTVI", "TVI"}, {"KTVL", "TVL"}, {"KTWF", "TWF"}, {"KTXK", "TXK"},
    {"KTYL", "TYZ"}, {"KTYR", "TYR"}, {"KTYS", "TYS"}, {"KUBS", "UBS"}, {"KUCY", "UCY"}, {"KUDD", "UDD"},
    {"KUES", "UES"}, {"KUGN", "UGN"}, {"KUIL", "UIL"}, {"KUIN", "UIN"}, {"KUKF", "IKB"}, {"KUKI", "UKI"},
    {"KUKT", "UKT"}, {"KULM", "ULM"}, {"KUNI", "ATO"}, {"KUNU", "UNU"}, {"KUNV", "SCE"}, {"KUOS", "UOS"},
    {"KUOX", "UOX"}, {"KUTA", "UTM"}, {"KUTS", "HTV"}, {"KUUU", "NPT"}, {"KUVA", "UVA"}, {"KUZA", "RKH"},
    {"KVAD", "VAD"}, {"KVAY", "LLY"}, {"KVBG", "VBG"}, {"KVCT", "VCT"}, {"KVCV", "VCV"}, {"KVDI", "VDI"},
    {"KVEL", "VEL"}, {"KVGT", "VGT"}, {"KVHN", "VHN"}, {"KVIH", "VIH"}, {"KVIS", "VIS"}, {"KVJI", "VJI"},
    {"KVKS", "VKS"}, {"KVLA", "VLA"}, {"KVLD", "VLD"}, {"KVNC", "VNC"}, {"KVNY", "VNY"}, {"KVOK", "VOK"},
    {"KVPS", "VPS"}, {"KVPZ", "VPZ"}, {"KVQQ", "VQQ"}, {"KVRB", "VRB"}, {"KVSF", "VSF"}, {"KVTN", "VTN"},
    {"KVYS", "VYS"}, {"KWAL", "WAL"}, {"KWAY", "WAY"}, {"KWBW", "WBW"}, {"KWDG", "WDG"}, {"KWDR", "WDR"},
    {"KWEA", "WEA"}, {"KWHP", "WHP"}, {"KWJF", "WJF"}, {"KWLD", "WLD"}, {"KWLW", "WLW"}, {"KWMC", "WMC"},
    {"KWRB", "WRB"}, {"KWRI", "WRI"}, {"KWRL", "WRL"}, {"KWST", "WST"}, {"KWVI", "WVI"}, {"KWVL", "WVL"},
    {"KWWD", "WWD"}, {"KWWR", "WWR"}, {"KWYS", "WYS"}, {"KXNA", "XNA"}, {"KXWA", "XWA"}, {"KYIP", "YIP"},
    {"KYKM", "YKM"}, {"KYKN", "YKN"}, {"KYNG", "YNG"}, {"KZPH", "ZPH"}, {"KZZV", "ZZV"}, {"LAKU", "KFZ"},
    {"LATI", "TIA"}, {"LBBG", "BOJ"}, {"LBGO", "GOZ"}, {"LBPD", "PDV"}, {"LBRS", "ROU"}, {"LBSF", "SOF"},
    {"LBWN", "VAR"}, {"LCEN", "ECN"}, {"LCGK", "GEC"}, {"LCLK", "LCA"}, {"LCPH", "PFO"}, {"LCRA", "AKT"},
    {"LDDU", "DBV"}, {"LDLO", "LSZ"}, {"LDOS", "OSI"}, {"LDPL", "PUY"}, {"LDRI", "RJK"}, {"LDSB", "BWK"},
    {"LDSP", "SPU"}, {"LDZA", "ZAG"}, {"LDZD", "ZAD"}, {"LEAB", "ABC"}, {"LEAL", "ALC"}, {"LEAM", "LEI"},
    {"LEAS", "OVD"}, {"LEBA", "ODB"}, {"LEBB", "BIO"}, {"LEBG", "RGS"}, {"LEBL", "BCN"}, {"LEBZ", "BJZ"},
    {"LECH", "CDT"}, {"LECO", "LCG"}, {"LEDA", "ILD"}, {"LEGE", "GRO"}, {"LEGR", "GRX"}, {"LEHC", "HSK"},
    {"LEIB", "IBZ"}, {"LEJR", "XRY"}, {"LELN", "LEN"}, {"LEMD", "MAD"}, {"LEMG", "AGP"}, {"LEMH", "MAH"},
    {"LEMI", "RMU"}, {"LEMO", "OZP"}, {"LEPA", "PMI"}, {"LEPP", "PNA"}, {"LERL", "CQM"}, {"LERS", "REU"},
    {"LERT", "ROZ"}, {"LESA", "SLM"}, {"LESO", "EAS"}, {"LEST", "SCQ"}, {"LESU", "LEU"}, {"LETL", "TEV"},
    {"LETO", "TOJ"}, {"LEVC", "VLC"}, {"LEVD", "VLL"}, {"LEVT", "VIT"}, {"LEVX", "VGO"}, {"LEXJ", "SDR"},
    {"LEZG", "ZAZ"}, {"LEZL", "SVQ"}, {"LFAB", "DPE"}, {"LFAC", "CQF"}, {"LFAQ", "BYF"}, {"LFAT", "LTQ"},
    {"LFBA", "AGF"}, {"LFBD", "BOD"}, {"LFBE", "EGC"}, {"LFBG", "CNG"}, {"LFBH", "LRH"}, {"LFBI", "PIS"},
    {"LFBK", "MCU"}, {"LFBL", "LIG"}, {"LFBN", "NIT"}, {"LFBO", "TLS"}, {"LFBP", "PUF"}, {"LFBT", "LDE"},
    {"LFBU", "ANG"}, {"LFBX", "PGX"}, {"LFBZ", "BIQ"}, {"LFCC", "ZAO"}, {"LFCI", "LBI"}, {"LFCK", "DCM"},
    {"LFCR", "RDZ"}, {"LFCY", "RYN"}, {"LFDN", "RCO"}, {"LFEA", "BIC"}, {"LFEC", "OUI"}, {"LFEY", "IDY"},
    {"LFGA", "CMR"}, {"LFGJ", "DLE"}, {"LFHM", "MVV"}, {"LFHO", "OBS"}, {"LFHP", "LPY"}, {"LFHU", "AHZ"},
    {"LFJL", "ETZ"}, {"LFJR", "ANE"}, {"LFKB", "BIA"}, {"LFKC", "CLY"}, {"LFKF", "FSC"}, {"LFKJ", "AJA"},
    {"LFKO", "PRP"}, {"LFKS", "SOZ"}, {"LFKX", "MFX"}, {"LFLA", "AUF"}, {"LFLB", "CMF"}, {"LFLC", "CFE"},
    {"LFLD", "BOU"}, {"LFLJ", "CVF"}, {"LFLL", "LYS"}, {"LFLN", "SYT"}, {"LFLO", "RNE"}, {"LFLP", "NCY"},
    {"LFLS", "GNB"}, {"LFLU", "VAF"}, {"LFLV", "VHY"}, {"LFLW", "AUR"}, {"LFLX", "CHR"}, {"LFLY", "LYN"},
    {"LFMD", "CEQ"}, {"LFMH", "EBU"}, {"LFMK", "CCF"}, {"LFML", "MRS"}, {"LFMN", "NCE"}, {"LFMP", "PGF"},
    {"LFMQ", "CTT"}, {"LFMR", "BAE"}, {"LFMT", "MPL"}, {"LFMU", "BZR"}, {"LFMV", "AVN"}, {"LFNA", "GAT"},
    {"LFNB", "MEN"}, {"LFNC", "SCP"}, {"LFOB", "BVA"}, {"LFOE", "EVX"}, {"LFOH", "LEH"}, {"LFOK", "XCR"},
    {"LFOO", "LSO"}, {"LFOP", "URO"}, {"LFOT", "TUF"}, {"LFOU", "CET"}, {"LFOV", "LVA"}, {"LFOZ", "ORE"},
    {"LFPB", "LBG"}, {"LFPC", "CSF"}, {"LFPG", "CDG"}, {"LFPN", "TNF"}, {"LFPO", "ORY"}, {"LFPT", "POX"},
    {"LFQG", "NVS"}, {"LFQQ", "LIL"}, {"LFQT", "HZB"}, {"LFRB", "BES"}, {"LFRC", "CER"}, {"LFRD", "DNR"},
    {"LFRE", "LBY"}, {"LFRF", "GFR"}, {"LFRG", "DOL"}, {"LFRH", "LRT"}, {"LFRI", "EDM"}, {"LFRJ", "LDV"},
    {"LFRK", "CFR"}, {"LFRM", "LME"}, {"LFRN", "RNS"}, {"LFRO", "LAI"}, {"LFRQ", "UIP"}, {"LFRS", "NTE"},
    {"LFRT", "SBK"}, {"LFRU", "MXN"}, {"LFRV", "VNE"}, {"LFRZ", "SNR"}, {"LFSB", "BSL"}, {"LFSD", "DIJ"},
    {"LFSG", "EPL"}, {"LFSL", "BVE"}, {"LFSN", "ENC"}, {"LFST", "SXB"}, {"LFTH", "TLN"}, {"LFTW", "FNI"},
    {"LFTZ", "LTT"}, {"LFVM", "MQC"}, {"LFVP", "FSP"}, {"LGAD", "PYR"}, {"LGAL", "AXD"}, {"LGAV", "ATH"},
    {"LGBL", "VOL"}, {"LGHI", "JKH"}, {"LGIK", "JIK"}, {"LGIO", "IOA"}, {"LGIR", "HER"}, {"LGKA", "KSO"},
    {"LGKC", "KIT"}, {"LGKF", "EFL"}, {"LGKJ", "KZS"}, {"LGKL", "KLX"}, {"LGKO", "KGS"}, {"LGKP", "AOK"},
    {"LGKR", "CFU"}, {"LGKS", "KSJ"}, {"LGKV", "KVA"}, {"LGKY", "JKL"}, {"LGKZ", "KZI"}, {"LGLE", "LRS"},
    {"LGLM", "LXS"}, {"LGLR", "LRA"}, {"LGMK", "JMK"}, {"LGML", "MLO"}, {"LGMT", "MJT"}, {"LGNX", "JNX"},
    {"LGPA", "PAS"}, {"LGPL", "JTY"}, {"LGPZ", "PVK"}, {"LGRP", "RHO"}, {"LGRX", "GPA"}, {"LGSA", "CHQ"},
    {"LGSK", "JSI"}, {"LGSM", "SMI"}, {"LGSO", "JSY"}, {"LGSR", "JTR"}, {"LGST", "JSH"}, {"LGSY", "SKU"},
    {"LGTS", "SKG"}, {"LGZA", "ZTH"}, {"LHBP", "BUD"}, {"LHDC", "DEB"}, {"LHPP", "PEV"}, {"LHSM", "SOB"},
    {"LIBC", "CRV"}, {"LIBD", "BRI"}, {"LIBF", "FOG"}, {"LIBG", "TAR"}, {"LIBN", "LCC"}, {"LIBP", "PSR"},
    {"LIBR", "BDS"}, {"LICA", "SUF"}, {"LICB", "CIY"}, {"LICC", "CTA"}, {"LICD", "LMP"}, {"LICG", "PNL"},
    {"LICJ", "PMO"}, {"LICR", "REG"}, {"LICT", "TPS"}, {"LIDB", "BLX"}, {"LIDR", "RAN"}, {"LIEA", "AHO"},
    {"LIED", "DCI"}, {"LIEE", "CAG"}, {"LIEO", "OLB"}, {"LIER", "FNU"}, {"LIMC", "MXP"}, {"LIME", "BGY"},
    {"LIMF", "TRN"}, {"LIMJ", "GOA"}, {"LIML", "LIN"}, {"LIMP", "PMF"}, {"LIMW", "AOT"}, {"LIMZ", "CUF"},
    {"LINI", "TQR"}, {"LIPA", "AVB"}, {"LIPB", "BZO"}, {"LIPE", "BLQ"}, {"LIPH", "TSF"}, {"LIPK", "FRL"},
    {"LIPO", "VBS"}, {"LIPQ", "TRS"}, {"LIPR", "RMI"}, {"LIPX", "VRN"}, {"LIPY", "AOI"}, {"LIPZ", "VCE"},
    {"LIRA", "CIA"}, {"LIRF", "FCO"}, {"LIRI", "QSR"}, {"LIRJ", "EBA"}, {"LIRN", "NAP"}, {"LIRP", "PSA"},
    {"LIRQ", "FLR"}, {"LIRS", "GRS"}, {"LIRZ", "PEG"}, {"LJLJ", "LJU"}, {"LJMB", "MBX"}, {"LJPZ", "POW"},
    {"LKCS", "JCL"}, {"LKKU", "UHE"}, {"LKKV", "KLV"}, {"LKMH", "HRA"}, {"LKMT", "OSR"}, {"LKOL", "OLO"},
    {"LKPD", "PED"}, {"LKPO", "PRV"}, {"LKPR", "PRG"}, {"LKTB", "BRQ"}, {"LKVO", "VOD"}, {"LKZA", "ZBE"},
    {"LLBG", "TLV"}, {"LLBS", "BEV"}, {"LLER", "ETM"}, {"LLEY", "EIY"}, {"LLHA", "HFA"}, {"LLIB", "RPN"},
    {"LLKS", "KSW"}, {"LLMR", "MIP"}, {"LLMZ", "MTZ"}, {"LLNV", "VTM"}, {"LLOV", "VDA"}, {"LMMG", "GZM"},
    {"LMML", "MLA"}, {"LNMC", "MCM"}, {"LOIC", "ANT"}, {"LOIH", "HOH"}, {"LOWG", "GRZ"}, {"LOWI", "INN"},
    {"LOWK", "KLU"}, {"LOWL", "LNZ"}, {"LOWS", "SZG"}, {"LOWW", "VIE"}, {"LPAZ", "SMA"}, {"LPBG", "BGC"},
    {"LPBJ", "BYJ"}, {"LPCR", "CVU"}, {"LPCS", "CAT"}, {"LPFL", "FLW"}, {"LPFR", "FAO"}, {"LPGR", "GRW"},
    {"LPHR", "HOR"}, {"LPLA", "TER"}, {"LPMA", "FNC"}, {"LPPD", "PDL"}, {"LPPI", "PIX"}, {"LPPM", "PRM"},
    {"LPPR", "OPO"}, {"LPPS", "PXO"}, {"LPPT", "LIS"}, {"LPSJ", "SJZ"}, {"LPVR", "VRL"}, {"LPVZ", "VSE"},
    {"LQBK", "BNX"}, {"LQMO", "OMO"}, {"LQSA", "SJJ"}, {"LQTZ", "TZL"}, {"LRAR", "ARW"}, {"LRBC", "BCM"},
    {"LRBM", "BAY"}, {"LRBS", "BBU"}, {"LRBV", "GHV"}, {"LRCK", "CND"}, {"LRCL", "CLJ"}, {"LRCS", "CSB"},
    {"LRCV", "CRA"}, {"LRIA", "IAS"}, {"LROD", "OMR"}, {"LROP", "OTP"}, {"LRSB", "SBZ"}, {"LRSM", "SUJ"},
    {"LRSV", "SCV"}, {"LRTC", "TCE"}, {"LRTM", "TGM"}, {"LRTR", "TSR"}, {"LSGG", "GVA"}, {"LSGS", "SIR"},
    {"LSME", "EML"}, {"LSMP", "VIP"}, {"LSZA", "LUG"}, {"LSZB", "BRN"}, {"LSZC", "BXO"}, {"LSZH", "ZRH"},
    {"LSZR", "ACH"}, {"LSZS", "SMV"}, {"LTAC", "ESB"}, {"LTAD", "ANK"}, {"LTAF", "ADA"}, {"LTAG", "UAB"},
    {"LTAH", "AFY"}, {"LTAI", "AYT"}, {"LTAJ", "GZT"}, {"LTAL", "KFS"}, {"LTAN", "KYA"}, {"LTAP", "MZH"},
    {"LTAR", "VAS"}, {"LTAS", "ONQ"}, {"LTAT", "MLX"}, {"LTAU", "ASR"}, {"LTAW", "TJK"}, {"LTAY", "DNZ"},
    {"LTAZ", "NAV"}, {"LTBA", "ISL"}, {"LTBD", "CII"}, {"LTBF", "BZI"}, {"LTBG", "BDM"}, {"LTBH", "CKZ"},
    {"LTBI", "ESK"}, {"LTBJ", "ADB"}, {"LTBO", "USQ"}, {"LTBQ", "KCO"}, {"LTBR", "YEI"}, {"LTBS", "DLM"},
    {"LTBU", "TEQ"}, {"LTBV", "BXN"}, {"LTBY", "AOE"}, {"LTBZ", "KZR"}, {"LTCA", "EZS"}, {"LTCB", "OGU"},
    {"LTCC", "DIY"}, {"LTCD", "ERC"}, {"LTCE", "ERZ"}, {"LTCF", "KSY"}, {"LTCG", "TZX"}, {"LTCI", "VAN"},
    {"LTCJ", "BAL"}, {"LTCK", "MSR"}, {"LTCL", "SXZ"}, {"LTCM", "NOP"}, {"LTCN", "KCM"}, {"LTCO", "AJI"},
    {"LTCP", "ADF"}, {"LTCR", "MQM"}, {"LTCS", "GNY"}, {"LTCT", "IGD"}, {"LTCU", "BGG"}, {"LTCV", "NKT"},
    {"LTCW", "YKO"}, {"LTDA", "HTY"}, {"LTDB", "COV"}, {"LTFB", "IZM"}, {"LTFC", "ISE"}, {"LTFD", "EDO"},
    {"LTFE", "BJV"}, {"LTFG", "GZP"}, {"LTFH", "SZF"}, {"LTFJ", "SAW"}, {"LTFK", "GKD"}, {"LTFM", "IST"},
    {"LTFO", "RZV"}, {"LUBL", "BZY"}, {"LUKK", "RMO"}, {"LWOH", "OHD"}, {"LWSK", "SKP"}, {"LXGB", "GIB"},
    {"LYBE", "BEG"}, {"LYBR", "IVG"}, {"LYBT", "BJY"}, {"LYKV", "KVO"}, {"LYNI", "INI"}, {"LYPG", "TGD"},
    {"LYTV", "TIV"}, {"LYUZ", "UZC"}, {"LZIB", "BTS"}, {"LZKZ", "KSC"}, {"LZLU", "LUE"}, {"LZPP", "PZY"},
    {"LZPW", "POV"}, {"LZSL", "SLD"}, {"LZTT", "TAT"}, {"LZZI", "ILZ"}, {"MBGT", "GDT"}, {"MBMC", "MDS"},
    {"MBNC", "NCA"}, {"MBPI", "PIC"}, {"MBPV", "PLS"}, {"MBSC", "XSC"}, {"MBSY", "SLX"}, {"MDBH", "BRX"},
    {"MDCR", "CBJ"}, {"MDCY", "AZS"}, {"MDCZ", "COZ"}, {"MDJB", "JBQ"}, {"MDLR", "LRM"}, {"MDPC", "PUJ"},
    {"MDPP", "POP"}, {"MDSD", "SDQ"}, {"MDST", "STI"}, {"MGCB", "CBV"}, {"MGCR", "CMM"}, {"MGCT", "CTF"},
    {"MGGT", "GUA"}, {"MGHT", "HUG"}, {"MGMM", "FRS"}, {"MGPB", "PBR"}, {"MGPG", "PKJ"}, {"MGPP", "PON"},
    {"MGQC", "AQB"}, {"MGQZ", "AAZ"}, {"MGRB", "RUV"}, {"MGRD", "LCF"}, {"MGRT", "RER"}, {"MGSJ", "GSJ"},
    {"MHAH", "AHS"}, {"MHCS", "CYL"}, {"MHEA", "OAN"}, {"MHGE", "CAA"}, {"MHIR", "IRN"}, {"MHJU", "JUT"},
    {"MHLC", "LCE"}, {"MHLE", "LEZ"}, {"MHLM", "SAP"}, {"MHNJ", "GJA"}, {"MHPC", "PCH"}, {"MHPL", "PEU"},
    {"MHPR", "XPL"}, {"MHRO", "RTB"}, {"MHTE", "TEA"}, {"MHTG", "TGU"}, {"MHTJ", "TJI"}, {"MHUL", "SCD"},
    {"MHUT", "UII"}, {"MHYR", "ORO"}, {"MKBS", "OCJ"}, {"MKJP", "KIN"}, {"MKJS", "MBJ"}, {"MKKJ", "POT"},
    {"MKNG", "NEG"}, {"MKTP", "KTP"}, {"MMAA", "ACA"}, {"MMAN", "NTR"}, {"MMAS", "AGU"}, {"MMBT", "HUX"},
    {"MMCA", "CNA"}, {"MMCB", "CVJ"}, {"MMCC", "ACN"}, {"MMCE", "CME"}, {"MMCG", "NCG"}, {"MMCL", "CUL"},
    {"MMCM", "CTM"}, {"MMCN", "CEN"}, {"MMCO", "CJT"}, {"MMCP", "CPE"}, {"MMCS", "CJS"}, {"MMCT", "CZA"},
    {"MMCU", "CUU"}, {"MMCV", "CVM"}, {"MMCY", "CYW"}, {"MMCZ", "CZM"}, {"MMDA", "CUA"}, {"MMDM", "MMC"},
    {"MMDO", "DGO"}, {"MMEP", "TPQ"}, {"MMES", "ESE"}, {"MMGL", "GDL"}, {"MMGM", "GYM"}, {"MMGR", "GUB"},
    {"MMHC", "TCN"}, {"MMHO", "HMO"}, {"MMIA", "CLQ"}, {"MMIM", "ISJ"}, {"MMIO", "SLW"}, {"MMIT", "IZT"},
    {"MMJA", "JAL"}, {"MMJC", "AZP"}, {"MMLC", "LZC"}, {"MMLM", "LMM"}, {"MMLO", "BJX"}, {"MMLP", "LAP"},
    {"MMLT", "LTO"}, {"MMMA", "MAM"}, {"MMMD", "MID"}, {"MMMG", "MUG"}, {"MMML", "MXL"}, {"MMMM", "MLM"},
    {"MMMT", "MTT"}, {"MMMV", "LOV"}, {"MMMX", "MEX"}, {"MMMY", "MTY"}, {"MMMZ", "MZT"}, {"MMNG", "NOG"},
    {"MMNL", "NLD"}, {"MMOX", "OAX"}, {"MMPA", "PAZ"}, {"MMPB", "PBC"}, {"MMPE", "PPE"}, {"MMPG", "PDS"},
    {"MMPL", "PCO"}, {"MMPN", "UPN"}, {"MMPQ", "PQM"}, {"MMPR", "PVR"}, {"MMPS", "PXM"}, {"MMQT", "QRO"},
    {"MMRX", "REX"}, {"MMSD", "SJD"}, {"MMSF", "SFH"}, {"MMSL", "CSW"}, {"MMSM", "NLU"}, {"MMSP", "SLP"},
    {"MMSZ", "SCX"}, {"MMTC", "TRC"}, {"MMTG", "TGZ"}, {"MMTJ", "TIJ"}, {"MMTL", "TQO"}, {"MMTM", "TAM"},
    {"MMTN", "TSL"}, {"MMTO", "TLC"}, {"MMTP", "TAP"}, {"MMTU", "TUY"}, {"MMUN", "CUN"}, {"MMVA", "VSA"},
    {"MMVR", "VER"}, {"MMZC", "ZCL"}, {"MMZH", "ZIH"}, {"MMZM", "ZMM"}, {"MMZO", "ZLO"}, {"MNBL", "BEF"},
    {"MNBZ", "BZA"}, {"MNCE", "ECI"}, {"MNCI", "RNI"}, {"MNMG", "MGA"}, {"MNPC", "PUZ"}, {"MNRT", "RFS"},
    {"MNSC", "NCR"}, {"MNSI", "SIU"}, {"MNWP", "WSP"}, {"MPBO", "BOC"}, {"MPCE", "CTD"}, {"MPCH", "CHX"},
    {"MPDA", "DAV"}, {"MPEJ", "ONX"}, {"MPJE", "JQE"}, {"MPMG", "PAC"}, {"MPOA", "PUE"}, {"MPPA", "BLB"},
    {"MPPD", "PDM"}, {"MPPI", "BFQ"}, {"MPRA", "OTD"}, {"MPSA", "SYP"}, {"MPSM", "RIH"}, {"MPTO", "PTY"},
    {"MPWN", "NBL"}, {"MRAN", "FON"}, {"MRBA", "BAI"}, {"MRBC", "BCL"}, {"MRCC", "OTR"}, {"MRCH", "JAP"},
    {"MRCR", "PLD"}, {"MRDK", "DRK"}, {"MRGF", "GLF"}, {"MRGP", "GPL"}, {"MRIA", "PBP"}, {"MRLB", "LIR"},
    {"MRLC", "LSL"}, {"MRLM", "LIO"}, {"MRMJ", "CSC"}, {"MRNC", "NCT"}, {"MRNS", "NOB"}, {"MROC", "SJO"},
    {"MRPJ", "PJM"}, {"MRPM", "PMZ"}, {"MRPV", "SYQ"}, {"MRQP", "XQP"}, {"MRRF", "RFR"}, {"MRSI", "IPZ"},
    {"MRSV", "TOO"}, {"MRTM", "TNO"}, {"MRTR", "TMU"}, {"MRUP", "UPL"}, {"MSLP", "SAL"}, {"MSSS", "ILS"},
    {"MTCA", "CYA"}, {"MTCH", "CAP"}, {"MTJA", "JAK"}, {"MTJE", "JEE"}, {"MTPP", "PAP"}, {"MTPX", "PAX"},
    {"MUBA", "BCA"}, {"MUBR", "BWW"}, {"MUBY", "BYM"}, {"MUCA", "AVI"}, {"MUCC", "CCC"}, {"MUCF", "CFG"},
    {"MUCL", "CYO"}, {"MUCM", "CMW"}, {"MUCU", "SCU"}, {"MUGM", "NBW"}, {"MUGT", "GAO"}, {"MUHA", "HAV"},
    {"MUHG", "HOG"}, {"MUKW", "VRO"}, {"MUMO", "MOA"}, {"MUMZ", "MZO"}, {"MUNG", "GER"}, {"MUPB", "UPB"},
    {"MUSC", "SNU"}, {"MUSJ", "SNJ"}, {"MUSN", "SZJ"}, {"MUSS", "USS"}, {"MUTD", "TND"}, {"MUVR", "VRA"},
    {"MUVT", "VTU"}, {"MWCB", "CYB"}, {"MWCL", "LYB"}, {"MWCR", "GCM"}, {"MYAB", "MAY"}, {"MYAF", "ASD"},
    {"MYAK", "TZN"}, {"MYAM", "MHH"}, {"MYAN", "SAQ"}, {"MYAP", "AXP"}, {"MYAT", "TCB"}, {"MYAW", "WKR"},
    {"MYBC", "CCZ"}, {"MYBG", "GHC"}, {"MYBS", "BIM"}, {"MYCA", "ATC"}, {"MYCB", "TBI"}, {"MYCC", "CXY"},
    {"MYCI", "CRI"}, {"MYCP", "PWN"}, {"MYEF", "GGT"}, {"MYEH", "ELH"}, {"MYEM", "GHB"}, {"MYEN", "NMC"},
    {"MYER", "RSD"}, {"MYES", "TYM"}, {"MYGF", "FPO"}, {"MYGW", "WTD"}, {"MYIG", "IGA"}, {"MYLD", "LGI"},
    {"MYLS", "SML"}, {"MYMM", "MYG"}, {"MYNN", "NAS"}, {"MYRD", "DCT"}, {"MYRP", "RCY"}, {"MYSM", "ZSA"},
    {"MZBE", "TZA"}, {"MZBG", "BGK"}, {"MZBZ", "BZE"}, {"MZCK", "CUK"}, {"MZCP", "CYC"}, {"MZCZ", "CZH"},
    {"MZPB", "DGA"}, {"MZPG", "PND"}, {"MZPL", "PLJ"}, {"MZSP", "SPR"}, {"MZSV", "INB"}, {"MZTH", "ORZ"},
    {"NCAI", "AIT"}, {"NCAT", "AIU"}, {"NCMG", "MGS"}, {"NCMH", "MHX"}, {"NCMK", "MUK"}, {"NCMR", "MOI"},
    {"NCPK", "PZK"}, {"NCPY", "PYE"}, {"NCRG", "RAR"}, {"NFCI", "ICI"}, {"NFCS", "CST"}, {"NFFN", "NAN"},
    {"NFFO", "PTF"}, {"NFFR", "RBI"}, {"NFKD", "KDV"}, {"NFMA", "MNF"}, {"NFMO", "MFJ"}, {"NFNA", "SUV"},
    {"NFNB", "LEV"}, {"NFND", "PHR"}, {"NFNG", "NGI"}, {"NFNH", "LUC"}, {"NFNK", "LKB"}, {"NFNL", "LBS"},
    {"NFNM", "TVU"}, {"NFNO", "KXF"}, {"NFNR", "RTA"}, {"NFNS", "SVU"}, {"NFNW", "KAY"}, {"NFOL", "ONU"},
    {"NFSW", "YAS"}, {"NFTE", "EUA"}, {"NFTF", "TBU"}, {"NFTL", "HPA"}, {"NFTO", "NFO"}, {"NFTP", "NTT"},
    {"NFTV", "VAV"}, {"NFVB", "VBV"}, {"NFVL", "VTF"}, {"NGAB", "ABF"}, {"NGBR", "BEZ"}, {"NGFU", "FUN"},
    {"NGKT", "KUC"}, {"NGMA", "MNK"}, {"NGMK", "MZK"}, {"NGMN", "MTK"}, {"NGNU", "NIG"}, {"NGON", "OOT"},
    {"NGTA", "TRW"}, {"NGTB", "AEA"}, {"NGTE", "TBF"}, {"NGTM", "TMN"}, {"NGTO", "NON"}, {"NGTR", "AIS"},
    {"NGTS", "TSU"}, {"NGTU", "BBG"}, {"NGUK", "AAK"}, {"NIUE", "IUE"}, {"NLWF", "FUT"}, {"NLWW", "WLS"},
    {"NSAS", "OFU"}, {"NSAU", "AAU"}, {"NSFA", "APW"}, {"NSFI", "FGI"}, {"NSFQ", "FTI"}, {"NSMA", "MXS"},
    {"NSTU", "PPG"}, {"NTAA", "PPT"}, {"NTAM", "RMT"}, {"NTAR", "RUR"}, {"NTAT", "TUB"}, {"NTAV", "RVV"},
    {"NTGA", "AAA"}, {"NTGB", "FGU"}, {"NTGC", "TIH"}, {"NTGD", "APK"}, {"NTGE", "REA"}, {"NTGF", "FAV"},
    {"NTGH", "HHZ"}, {"NTGI", "XMH"}, {"NTGJ", "GMR"}, {"NTGK", "KKR"}, {"NTGM", "MKP"}, {"NTGN", "NAU"},
    {"NTGO", "TKV"}, {"NTGP", "PKP"}, {"NTGQ", "PUK"}, {"NTGT", "TKP"}, {"NTGU", "AXR"}, {"NTGV", "MVT"},
    {"NTGW", "NUK"}, {"NTGY", "ZTA"}, {"NTHE", "AHE"}, {"NTKA", "KHZ"}, {"NTKF", "FAC"}, {"NTKH", "FHZ"},
    {"NTKK", "RKA"}, {"NTKM", "TJN"}, {"NTKN", "NIU"}, {"NTKO", "RRR"}, {"NTKR", "TKX"}, {"NTKT", "KXU"},
    {"NTMD", "NHV"}, {"NTMN", "AUQ"}, {"NTMP", "UAP"}, {"NTMU", "UAH"}, {"NTTB", "BOB"}, {"NTTE", "TTI"},
    {"NTTG", "RGI"}, {"NTTH", "HUH"}, {"NTTM", "MOZ"}, {"NTTO", "HOI"}, {"NTTP", "MAU"}, {"NTTR", "RFP"},
    {"NTTU", "TPX"}, {"NTTX", "UOA"}, {"NTUV", "VHZ"}, {"NVSA", "MTV"}, {"NVSC", "SLH"}, {"NVSD", "TOH"},
    {"NVSE", "EAE"}, {"NVSF", "CCV"}, {"NVSG", "LOD"}, {"NVSH", "SSR"}, {"NVSI", "PBJ"}, {"NVSL", "LPM"},
    {"NVSM", "LNB"}, {"NVSN", "MWF"}, {"NVSO", "LNE"}, {"NVSP", "NUS"}, {"NVSQ", "ZGU"}, {"NVSR", "RCL"},
    {"NVSS", "SON"}, {"NVST", "TGH"}, {"NVSU", "ULB"}, {"NVSV", "VLS"}, {"NVSW", "WLH"}, {"NVSX", "SWJ"},
    {"NVSZ", "OLJ"}, {"NVVA", "AUY"}, {"NVVB", "AWD"}, {"NVVD", "DLY"}, {"NVVF", "FTA"}, {"NVVI", "IPA"},
    {"NVVV", "VLI"}, {"NVVW", "TAH"}, {"NWWA", "TGJ"}, {"NWWC", "BMY"}, {"NWWD", "KNQ"}, {"NWWE", "ILP"},
    {"NWWK", "KOC"}, {"NWWL", "LIF"}, {"NWWM", "GEA"}, {"NWWP", "PUV"}, {"NWWQ", "PDC"}, {"NWWR", "MEE"},
    {"NWWU", "TOU"}, {"NWWV", "UVE"}, {"NWWW", "NOU"}, {"NZAA", "AKL"}, {"NZAP", "TUO"}, {"NZAR", "AMZ"},
    {"NZAS", "ASG"}, {"NZCH", "CHC"}, {"NZCI", "CHT"}, {"NZCX", "CMV"}, {"NZDA", "DGR"}, {"NZDN", "DUD"},
    {"NZGB", "GBZ"}, {"NZGM", "GMN"}, {"NZGS", "GIS"}, {"NZGT", "GTN"}, {"NZHK", "HKK"}, {"NZHN", "HLZ"},
    {"NZKE", "WIK"}, {"NZKI", "KBZ"}, {"NZKK", "KKE"}, {"NZKO", "KKO"}, {"NZKT", "KAT"}, {"NZLX", "ALR"},
    {"NZMA", "MTA"}, {"NZMC", "MON"}, {"NZMF", "MFN"}, {"NZMK", "MZP"}, {"NZMO", "TEU"}, {"NZMS", "MRO"},
    {"NZNP", "NPL"}, {"NZNR", "NPE"}, {"NZNS", "NSN"}, {"NZNV", "IVC"}, {"NZOH", "OHA"}, {"NZOU", "OAM"},
    {"NZPM", "PMR"}, {"NZPN", "PCN"}, {"NZPP", "PPQ"}, {"NZQN", "ZQN"}, {"NZRA", "RAG"}, {"NZRC", "SZS"},
    {"NZRO", "ROT"}, {"NZTG", "TRG"}, {"NZTH", "TMZ"}, {"NZTK", "KTF"}, {"NZTO", "TKZ"}, {"NZTU", "TIU"},
    {"NZUK", "TWZ"}, {"NZWB", "BHE"}, {"NZWF", "WKA"}, {"NZWK", "WHK"}, {"NZWN", "WLG"}, {"NZWO", "WIR"},
    {"NZWR", "WRE"}, {"NZWS", "WSZ"}, {"NZWT", "WTZ"}, {"NZWU", "WAG"}, {"OABN", "BIN"}, {"OABT", "BST"},
    {"OACC", "CCN"}, {"OADS", "SBF"}, {"OADY", "DWR"}, {"OADZ", "DAZ"}, {"OAFR", "FAH"}, {"OAFZ", "FBD"},
    {"OAGN", "GZI"}, {"OAGZ", "GRG"}, {"OAHN", "KWH"}, {"OAHR", "HEA"}, {"OAIX", "OAI"}, {"OAJL", "JAA"},
    {"OAKB", "KBL"}, {"OAKN", "KDH"}, {"OAKS", "KHT"}, {"OAMN", "MMZ"}, {"OAMS", "MZR"}, {"OANZ", "IMZ"},
    {"OAOG", "URN"}, {"OAQN", "LQN"}, {"OARG", "URZ"}, {"OARZ", "KUR"}, {"OASA", "OAS"}, {"OASD", "OAH"},
    {"OASH", "OAA"}, {"OASL", "OLR"}, {"OASN", "SGA"}, {"OATN", "TII"}, {"OATQ", "TQN"}, {"OAUZ", "UND"},
    {"OAZI", "OAZ"}, {"OBBI", "BAH"}, {"OEAB", "AHB"}, {"OEAH", "HOF"}, {"OEAO", "ULH"}, {"OEBA", "ABT"},
    {"OEBH", "BHH"}, {"OEDF", "DMM"}, {"OEDM", "DWD"}, {"OEDR", "DHA"}, {"OEGN", "GIZ"}, {"OEGS", "ELQ"},
    {"OEGT", "URY"}, {"OEHL", "HAS"}, {"OEJN", "JED"}, {"OEKK", "KMC"}, {"OEKM", "KMX"}, {"OEMA", "MED"},
    {"OENG", "EAM"}, {"OENN", "NUM"}, {"OEPA", "AQI"}, {"OEPS", "AKH"}, {"OERF", "RAH"}, {"OERK", "RUH"},
    {"OERR", "RAE"}, {"OERS", "RSI"}, {"OESH", "SHW"}, {"OESK", "AJF"}, {"OESL", "SLF"}, {"OETB", "TUU"},
    {"OETF", "TIF"}, {"OETR", "TUI"}, {"OEWD", "WAE"}, {"OEWJ", "EJH"}, {"OEYN", "YNB"}, {"OEZL", "ZUL"},
    {"OIAA", "ABD"}, {"OIAD", "DEF"}, {"OIAG", "AKW"}, {"OIAH", "GCH"}, {"OIAJ", "OMI"}, {"OIAM", "MRX"},
    {"OIAW", "AWZ"}, {"OIBA", "AEU"}, {"OIBB", "BUZ"}, {"OIBJ", "KNR"}, {"OIBK", "KIH"}, {"OIBL", "BDH"},
    {"OIBP", "PGU"}, {"OIBQ", "KHK"}, {"OIBS", "SXI"}, {"OIBV", "LVP"}, {"OICC", "KSH"}, {"OICI", "IIL"},
    {"OICK", "KHD"}, {"OICS", "SDG"}, {"OIFE", "IFH"}, {"OIFK", "KKS"}, {"OIFM", "IFN"}, {"OIFS", "CQD"},
    {"OIGG", "RAS"}, {"OIHH", "HDM"}, {"OIHR", "AJK"}, {"OIHS", "NUJ"}, {"OIIE", "IKA"}, {"OIII", "THR"},
    {"OIIK", "GZW"}, {"OIIP", "PYK"}, {"OIIS", "SNX"}, {"OIKB", "BND"}, {"OIKJ", "JYR"}, {"OIKK", "KER"},
    {"OIKM", "BXR"}, {"OIKP", "HDR"}, {"OIKQ", "GSM"}, {"OIKR", "RJN"}, {"OIKY", "SYJ"}, {"OIMB", "XBJ"},
    {"OIMC", "CKT"}, {"OIMJ", "RUD"}, {"OIMM", "MHD"}, {"OIMN", "BJB"}, {"OIMS", "AFZ"}, {"OIMT", "TCX"},
    {"OINE", "KLM"}, {"OING", "GBT"}, {"OINJ", "BSM"}, {"OINN", "NSH"}, {"OINR", "RZR"}, {"OINZ", "SRY"},
    {"OISF", "FAZ"}, {"OISJ", "JAR"}, {"OISL", "LRR"}, {"OISR", "LFM"}, {"OISS", "SYZ"}, {"OISY", "YES"},
    {"OITH", "KHA"}, {"OITK", "KHY"}, {"OITL", "ADU"}, {"OITM", "ACP"}, {"OITP", "PFQ"}, {"OITR", "OMH"},
    {"OITT", "TBZ"}, {"OITU", "IMQ"}, {"OITZ", "JWN"}, {"OIYY", "AZD"}, {"OIZB", "ACZ"}, {"OIZC", "ZBR"},
    {"OIZH", "ZAH"}, {"OIZI", "IHR"}, {"OIZJ", "JSK"}, {"OJAI", "AMM"}, {"OJAM", "ADJ"}, {"OJAQ", "AQJ"},
    {"OJMF", "OMF"}, {"OKAJ", "XIJ"}, {"OKKK", "KWI"}, {"OLBA", "BEY"}, {"OLKA", "KYE"}, {"OMAA", "AUH"},
    {"OMAD", "AZI"}, {"OMAL", "AAN"}, {"OMAM", "DHF"}, {"OMBY", "XSB"}, {"OMDB", "DXB"}, {"OMDL", "ZDY"},
    {"OMDM", "NHD"}, {"OMDW", "DWC"}, {"OMFJ", "FJR"}, {"OMRK", "RKT"}, {"OMSJ", "SHJ"}, {"OOBR", "RMB"},
    {"OODQ", "DQM"}, {"OOFD", "FAU"}, {"OOGB", "RNM"}, {"OOKB", "KHS"}, {"OOLK", "LKW"}, {"OOMA", "MSH"},
    {"OOMS", "MCT"}, {"OOMX", "OMM"}, {"OOSA", "SLL"}, {"OOSH", "OHS"}, {"OOTH", "TTH"}, {"OPBN", "BNP"},
    {"OPBW", "BHV"}, {"OPCH", "CJL"}, {"OPCL", "CHB"}, {"OPDB", "DBA"}, {"OPDG", "DEA"}, {"OPDI", "DSK"},
    {"OPFA", "LYP"}, {"OPGT", "GIL"}, {"OPGW", "GWD"}, {"OPIS", "ISB"}, {"OPJA", "JAG"}, {"OPKC", "KHI"},
    {"OPKD", "HDD"}, {"OPKH", "KDD"}, {"OPKT", "OHT"}, {"OPKW", "KCF"}, {"OPLA", "LHE"}, {"OPLL", "LRG"},
    {"OPMA", "XJM"}, {"OPMF", "MFG"}, {"OPMI", "MWD"}, {"OPMJ", "MJD"}, {"OPMP", "MPD"}, {"OPMT", "MUX"},
    {"OPNH", "WNS"}, {"OPOR", "ORW"}, {"OPPC", "PAJ"}, {"OPPG", "PJG"}, {"OPPI", "PSI"}, {"OPPS", "PEW"},
    {"OPQT", "UET"}, {"OPRK", "RYK"}, {"OPRT", "RAZ"}, {"OPSB", "SBQ"}, {"OPSD", "KDU"}, {"OPSK", "SKZ"},
    {"OPSN", "SYW"}, {"OPSR", "SGI"}, {"OPSS", "SDT"}, {"OPST", "SKT"}, {"OPSU", "SUL"}, {"OPSW", "RZS"},
    {"OPTA", "TLB"}, {"OPTH", "BDN"}, {"OPTU", "TUK"}, {"OPWN", "WAF"}, {"OPZB", "PZH"}, {"OPZM", "ZIZ"},
    {"ORAA", "IQA"}, {"ORAT", "TQD"}, {"ORBB", "BMN"}, {"ORBI", "BGW"}, {"ORBM", "OSM"}, {"ORER", "EBL"},
    {"ORKK", "KIK"}, {"ORMM", "BSR"}, {"ORNI", "NJF"}, {"ORSJ", "ISU"}, {"OSAP", "ALP"}, {"OSDI", "DAM"},
    {"OSDZ", "DEZ"}, {"OSKL", "KAC"}, {"OSLK", "LTK"}, {"OSPR", "PMS"}, {"OTBD", "DIA"}, {"OTBH", "XJD"},
    {"OTHH", "DOH"}, {"OYAA", "ADE"}, {"OYAT", "AXK"}, {"OYBN", "BHN"}, {"OYGD", "AAY"}, {"OYKM", "KAM"},
    {"OYMB", "MYN"}, {"OYMS", "UKR"}, {"OYQN", "IHN"}, {"OYRN", "RIY"}, {"OYSH", "SYE"}, {"OYSN", "SAH"},
    {"OYSQ", "SCT"}, {"OYSY", "GXF"}, {"OYTZ", "TAI"}, {"PAAK", "AKB"}, {"PAAL", "PML"}, {"PAAP", "PTD"},
    {"PAAQ", "PAQ"}, {"PAAT", "ATU"}, {"PABA", "BTI"}, {"PABE", "BET"}, {"PABG", "BVU"}, {"PABI", "BIG"},
    {"PABL", "BKC"}, {"PABM", "BMX"}, {"PABR", "BRW"}, {"PABT", "BTT"}, {"PACD", "CDB"}, {"PACE", "CEM"},
    {"PACH", "CHU"}, {"PACI", "CIK"}, {"PACJ", "CKD"}, {"PACK", "CYF"}, {"PACM", "SCM"}, {"PACR", "IRC"},
    {"PACS", "WSF"}, {"PACV", "CDV"}, {"PACX", "CXF"}, {"PACY", "CYT"}, {"PACZ", "CZF"}, {"PADE", "DRG"},
    {"PADG", "RDB"}, {"PADK", "ADK"}, {"PADL", "DLG"}, {"PADM", "MLL"}, {"PADQ", "ADQ"}, {"PADU", "DUT"},
    {"PADY", "KKH"}, {"PAED", "EDF"}, {"PAEE", "EEK"}, {"PAEG", "EAA"}, {"PAEH", "EHM"}, {"PAEI", "EIL"},
    {"PAEL", "ELV"}, {"PAEM", "EMK"}, {"PAEN", "ENA"}, {"PAEW", "WWT"}, {"PAFA", "FAI"}, {"PAFB", "FBK"},
    {"PAFM", "ABL"}, {"PAFR", "FRN"}, {"PAFS", "NIB"}, {"PAGA", "GAL"}, {"PAGB", "GBH"}, {"PAGG", "KWK"},
    {"PAGH", "SHG"}, {"PAGK", "GKN"}, {"PAGL", "GLV"}, {"PAGM", "GAM"}, {"PAGN", "AGN"}, {"PAGQ", "BGQ"},
    {"PAGS", "GST"}, {"PAGT", "NME"}, {"PAGX", "KGX"}, {"PAGY", "SGY"}, {"PAGZ", "GMT"}, {"PAHC", "HCR"},
    {"PAHL", "HSL"}, {"PAHN", "HNS"}, {"PAHO", "HOM"}, {"PAHP", "HPB"}, {"PAHU", "HUS"}, {"PAHX", "SHX"},
    {"PAHY", "HYG"}, {"PAIG", "IGG"}, {"PAII", "EGX"}, {"PAIK", "IAN"}, {"PAIL", "ILI"}, {"PAIM", "UTO"},
    {"PAIN", "MCL"}, {"PAIW", "WAA"}, {"PAJC", "KCG"}, {"PAJN", "JNU"}, {"PAJZ", "KGK"}, {"PAKA", "TEK"},
    {"PAKC", "KCC"}, {"PAKD", "KDK"}, {"PAKF", "KFP"}, {"PAKH", "AKK"}, {"PAKI", "KPN"}, {"PAKK", "KKA"},
    {"PAKL", "LKK"}, {"PAKN", "AKN"}, {"PAKO", "IKO"}, {"PAKP", "AKP"}, {"PAKT", "KTN"}, {"PAKU", "UUK"},
    {"PAKV", "KAL"}, {"PAKW", "KLW"}, {"PAKY", "KYK"}, {"PALB", "KLN"}, {"PALG", "KLG"}, {"PALJ", "PTA"},
    {"PALN", "LNI"}, {"PALR", "WCR"}, {"PALU", "LUR"}, {"PAMB", "KMO"}, {"PAMC", "MCG"}, {"PAMD", "MDO"},
    {"PAMH", "LMA"}, {"PAMK", "SMK"}, {"PAML", "MLY"}, {"PAMM", "MTM"}, {"PAMO", "MOU"}, {"PAMR", "MRI"},
    {"PAMX", "MXY"}, {"PAMY", "MYU"}, {"PANA", "WNA"}, {"PANC", "ANC"}, {"PANI", "ANI"}, {"PANN", "ENN"},
    {"PANO", "NNL"}, {"PANR", "FNR"}, {"PANT", "ANN"}, {"PANU", "NUL"}, {"PANV", "ANV"}, {"PANW", "KNW"},
    {"PAOB", "OBU"}, {"PAOC", "PCA"}, {"PAOH", "HNH"}, {"PAOM", "OME"}, {"PAOO", "OOK"}, {"PAOR", "ORT"},
    {"PAOT", "OTZ"}, {"PAOU", "NLG"}, {"PAPB", "STG"}, {"PAPC", "KPC"}, {"PAPE", "KPV"}, {"PAPG", "PSG"},
    {"PAPH", "PTH"}, {"PAPK", "PKA"}, {"PAPM", "PTU"}, {"PAPN", "PIP"}, {"PAPO", "PHO"}, {"PAPR", "PPC"},
    {"PAQH", "KWN"}, {"PAQT", "NUI"}, {"PARC", "ARC"}, {"PARS", "RSH"}, {"PARY", "RBY"}, {"PASA", "SVA"},
    {"PASC", "SCC"}, {"PASD", "SDP"}, {"PASH", "SHH"}, {"PASI", "SIT"}, {"PASK", "WLK"}, {"PASL", "SLQ"},
    {"PASM", "KSM"}, {"PASN", "SNP"}, {"PASO", "SOV"}, {"PASP", "SMU"}, {"PAST", "UMM"}, {"PASV", "SVW"},
    {"PASW", "SKW"}, {"PASX", "SXQ"}, {"PASY", "SYA"}, {"PATA", "TAL"}, {"PATC", "TNC"}, {"PATE", "TLA"},
    {"PATG", "TOG"}, {"PATK", "TKA"}, {"PATL", "TLJ"}, {"PATQ", "ATK"}, {"PAUK", "AUK"}, {"PAUM", "UMT"},
    {"PAUN", "UNK"}, {"PAUO", "WOW"}, {"PAUT", "KQA"}, {"PAVA", "VAK"}, {"PAVC", "KVC"}, {"PAVD", "VDZ"},
    {"PAVE", "VEE"}, {"PAVL", "KVL"}, {"PAWB", "WBQ"}, {"PAWD", "SWD"}, {"PAWG", "WRG"}, {"PAWI", "AIN"},
    {"PAWM", "WMO"}, {"PAWN", "WTK"}, {"PAWS", "WWA"}, {"PAYA", "YAK"}, {"PCIS", "CIS"}, {"PFAK", "AKI"},
    {"PFAL", "AET"}, {"PFCB", "NCN"}, {"PFCL", "CLP"}, {"PFEL", "ELI"}, {"PFKA", "KUK"}, {"PFKK", "KNK"},
    {"PFKO", "KOT"}, {"PFKT", "KTS"}, {"PFKU", "KYU"}, {"PFKW", "KWT"}, {"PFMP", "RMP"}, {"PFNO", "ORV"},
    {"PFSH", "SKK"}, {"PFTO", "TKJ"}, {"PFWS", "WSN"}, {"PFYU", "FYU"}, {"PFZK", "KKI"}, {"PGRO", "ROP"},
    {"PGSN", "SPN"}, {"PGUA", "UAM"}, {"PGUM", "GUM"}, {"PGWT", "TIQ"}, {"PHBK", "BKH"}, {"PHDH", "HDH"},
    {"PHHI", "HHI"}, {"PHHN", "HNM"}, {"PHJH", "JHM"}, {"PHJR", "JRF"}, {"PHKO", "KOA"}, {"PHLI", "LIH"},
    {"PHLU", "LUP"}, {"PHMK", "MKK"}, {"PHMU", "MUE"}, {"PHNG", "NGF"}, {"PHNL", "HNL"}, {"PHNY", "LNY"},
    {"PHOG", "OGG"}, {"PHPA", "PAK"}, {"PHSF", "BSF"}, {"PHTO", "ITO"}, {"PHUP", "UPP"}, {"PKMA", "ENT"},
    {"PKMJ", "MAJ"}, {"PKWA", "KWA"}, {"PLCH", "CXI"}, {"PLFA", "TNV"}, {"PLWN", "TNQ"}, {"PMDY", "MDY"},
    {"PPCT", "TCT"}, {"PPIT", "NUP"}, {"PPIZ", "PIZ"}, {"PTFK", "TKL"}, {"PTKK", "TKK"}, {"PTPN", "PNI"},
    {"PTRO", "ROR"}, {"PTSA", "KSA"}, {"PTYA", "YAP"}, {"PWAK", "AWK"}, {"RCBS", "KNH"}, {"RCCM", "CMJ"},
    {"RCFG", "LZN"}, {"RCFN", "TTT"}, {"RCGI", "GNI"}, {"RCKH", "KHH"}, {"RCKU", "CYI"}, {"RCKW", "HCN"},
    {"RCLM", "DSX"}, {"RCLY", "KYD"}, {"RCMQ", "RMQ"}, {"RCMT", "MFK"}, {"RCNN", "TNN"}, {"RCPO", "HSZ"},
    {"RCQC", "MZG"}, {"RCSS", "TSA"}, {"RCTP", "TPE"}, {"RCWA", "WOT"}, {"RCYU", "HUN"}, {"RJAA", "NRT"},
    {"RJAF", "MMJ"}, {"RJAH", "IBR"}, {"RJAM", "MUS"}, {"RJAW", "IWO"}, {"RJBB", "KIX"}, {"RJBD", "SHM"},
    {"RJBE", "UKB"}, {"RJBH", "HIW"}, {"RJBT", "TJH"}, {"RJCB", "OBO"}, {"RJCC", "CTS"}, {"RJCH", "HKD"},
    {"RJCK", "KUH"}, {"RJCM", "MMB"}, {"RJCN", "SHB"}, {"RJCO", "OKD"}, {"RJCR", "RBJ"}, {"RJCW", "WKJ"},
    {"RJDA", "AXJ"}, {"RJDB", "IKI"}, {"RJDC", "UBJ"}, {"RJDT", "TSJ"}, {"RJDU", "OMJ"}, {"RJEB", "MBE"},
    {"RJEC", "AKJ"}, {"RJEO", "OIR"}, {"RJER", "RIS"}, {"RJFC", "KUM"}, {"RJFE", "FUJ"}, {"RJFF", "FUK"},
    {"RJFG", "TNE"}, {"RJFK", "KOJ"}, {"RJFM", "KMI"}, {"RJFO", "OIT"}, {"RJFR", "KKJ"}, {"RJFS", "HSG"},
    {"RJFT", "KMJ"}, {"RJFU", "NGS"}, {"RJGG", "NGO"}, {"RJKA", "ASJ"}, {"RJKB", "OKE"}, {"RJKI", "KKX"},
    {"RJKN", "TKN"}, {"RJNA", "NKM"}, {"RJNF", "FKJ"}, {"RJNK", "KMQ"}, {"RJNO", "OKI"}, {"RJNS", "FSZ"},
    {"RJNT", "TOY"}, {"RJNW", "NTQ"}, {"RJOA", "HIJ"}, {"RJOB", "OKJ"}, {"RJOC", "IZO"}, {"RJOH", "YGJ"},
    {"RJOI", "IWK"}, {"RJOK", "KCZ"}, {"RJOM", "MYJ"}, {"RJOO", "ITM"}, {"RJOR", "TTJ"}, {"RJOS", "TKS"},
    {"RJOT", "TAK"}, {"RJOW", "IWJ"}, {"RJSA", "AOJ"}, {"RJSC", "GAJ"}, {"RJSD", "SDS"}, {"RJSF", "FKS"},
    {"RJSH", "HHE"}, {"RJSI", "HNA"}, {"RJSK", "AXT"}, {"RJSM", "MSJ"}, {"RJSN", "KIJ"}, {"RJSR", "ONJ"},
    {"RJSS", "SDJ"}, {"RJSY", "SYO"}, {"RJTA", "NJA"}, {"RJTH", "HAC"}, {"RJTO", "OIM"}, {"RJTQ", "MYE"},
    {"RJTT", "HND"}, {"RJTY", "OKO"}, {"RKJB", "MWX"}, {"RKJJ", "KWJ"}, {"RKJK", "KUV"}, {"RKJU", "CHN"},
    {"RKJY", "RSU"}, {"RKNN", "KAG"}, {"RKNW", "WJU"}, {"RKNY", "YNY"}, {"RKPC", "CJU"}, {"RKPD", "JDG"},
    {"RKPE", "CHF"}, {"RKPK", "PUS"}, {"RKPS", "HIN"}, {"RKPU", "USN"}, {"RKSI", "ICN"}, {"RKSO", "OSN"},
    {"RKSS", "GMP"}, {"RKSW", "SWU"}, {"RKTH", "KPO"}, {"RKTI", "JWO"}, {"RKTL", "UJN"}, {"RKTN", "TAE"},
    {"RKTP", "HMY"}, {"RKTU", "CJJ"}, {"RKTY", "YEC"}, {"ROAH", "OKA"}, {"RODN", "DNA"}, {"ROIG", "ISG"},
    {"ROKJ", "UEO"}, {"ROKR", "KJP"}, {"ROMD", "MMD"}, {"ROMY", "MMY"}, {"RORA", "AGJ"}, {"RORE", "IEJ"},
    {"RORH", "HTR"}, {"RORK", "KTD"}, {"RORS", "SHI"}, {"RORT", "TRA"}, {"RORY", "RNJ"}, {"ROYN", "OGN"},
    {"RPEN", "ENI"}, {"RPLB", "SFS"}, {"RPLC", "CRK"}, {"RPLE", "BSI"}, {"RPLH", "LLC"}, {"RPLI", "LAO"},
    {"RPLK", "DRP"}, {"RPLL", "MNL"}, {"RPLO", "CYU"}, {"RPLS", "SGL"}, {"RPLU", "LBX"}, {"RPMA", "AAV"},
    {"RPMC", "CBO"}, {"RPMD", "DVO"}, {"RPME", "BXU"}, {"RPMF", "BPH"}, {"RPMG", "DPL"}, {"RPMH", "CGM"},
    {"RPMI", "IGN"}, {"RPMJ", "JOL"}, {"RPMM", "MLP"}, {"RPMN", "TWT"}, {"RPMO", "OZC"}, {"RPMP", "PAG"},
    {"RPMQ", "MXI"}, {"RPMR", "GES"}, {"RPMS", "SUG"}, {"RPMU", "CDY"}, {"RPMV", "IPE"}, {"RPMW", "TDG"},
    {"RPMY", "CGY"}, {"RPMZ", "ZAM"}, {"RPNS", "IAO"}, {"RPSD", "RZP"}, {"RPSP", "TAG"}, {"RPSV", "SWL"},
    {"RPUB", "BAG"}, {"RPUD", "DTE"}, {"RPUH", "SJI"}, {"RPUM", "MBO"}, {"RPUN", "WNP"}, {"RPUO", "BSO"},
    {"RPUR", "BQA"}, {"RPUS", "SFE"}, {"RPUT", "TUG"}, {"RPUV", "VRC"}, {"RPUW", "MRQ"}, {"RPUY", "CYZ"},
    {"RPVA", "TAC"}, {"RPVB", "BCD"}, {"RPVC", "CYP"}, {"RPVD", "DGT"}, {"RPVE", "MPH"}, {"RPVF", "CRM"},
    {"RPVI", "ILO"}, {"RPVJ", "MBT"}, {"RPVK", "KLO"}, {"RPVM", "CEB"}, {"RPVO", "OMC"}, {"RPVP", "PPS"},
    {"RPVR", "RXS"}, {"RPVS", "EUQ"}, {"RPVU", "TBH"}, {"RPVV", "USU"}, {"SAAC", "COC"}, {"SAAG", "GHU"},
    {"SAAP", "PRA"}, {"SAAR", "ROS"}, {"SAAV", "SFN"}, {"SABE", "AEP"}, {"SACC", "LCM"}, {"SACO", "COR"},
    {"SADL", "LPG"}, {"SADP", "EPA"}, {"SAEZ", "EZE"}, {"SAFR", "RAF"}, {"SAFS", "NCJ"}, {"SAHC", "HOS"},
    {"SAHR", "GNR"}, {"SAHS", "RDS"}, {"SAHZ", "APZ"}, {"SAME", "MDZ"}, {"SAMM", "LGS"}, {"SAMR", "AFA"},
    {"SANC", "CTC"}, {"SANE", "SDE"}, {"SANL", "IRJ"}, {"SANR", "RHD"}, {"SANT", "TUC"}, {"SANU", "UAQ"},
    {"SANW", "CRR"}, {"SAOC", "RCU"}, {"SAOD", "VDR"}, {"SAOR", "VME"}, {"SAOS", "RLO"}, {"SAOU", "LUQ"},
    {"SARC", "CNQ"}, {"SARE", "RES"}, {"SARF", "FMA"}, {"SARI", "IGR"}, {"SARL", "AOL"}, {"SARM", "MCS"},
    {"SARP", "PSS"}, {"SARS", "PRQ"}, {"SASA", "SLA"}, {"SASJ", "JUJ"}, {"SASO", "ORA"}, {"SAST", "TTG"},
    {"SATC", "CLX"}, {"SATD", "ELO"}, {"SATG", "OYA"}, {"SATK", "LLS"}, {"SATM", "MDX"}, {"SATR", "RCQ"},
    {"SATU", "UZU"}, {"SAVB", "EHL"}, {"SAVC", "CRD"}, {"SAVD", "EMX"}, {"SAVE", "EQS"}, {"SAVH", "LHS"},
    {"SAVJ", "IGB"}, {"SAVM", "OLN"}, {"SAVN", "OES"}, {"SAVQ", "MQD"}, {"SAVR", "ARR"}, {"SAVS", "SGV"},
    {"SAVT", "REL"}, {"SAVV", "VDM"}, {"SAVY", "PMY"}, {"SAWC", "FTE"}, {"SAWD", "PUD"}, {"SAWE", "RGA"},
    {"SAWG", "RGL"}, {"SAWH", "USH"}, {"SAWJ", "ULA"}, {"SAWM", "ROY"}, {"SAWP", "PMQ"}, {"SAWR", "GGS"},
    {"SAWS", "JSM"}, {"SAWT", "RYO"}, {"SAWU", "RZA"}, {"SAZB", "BHI"}, {"SAZC", "CSZ"}, {"SAZF", "OVR"},
    {"SAZG", "GPO"}, {"SAZH", "OYO"}, {"SAZL", "SST"}, {"SAZM", "MDQ"}, {"SAZN", "NQN"}, {"SAZO", "NEC"},
    {"SAZP", "PEH"}, {"SAZR", "RSA"}, {"SAZS", "BRC"}, {"SAZT", "TDL"}, {"SAZV", "VLG"}, {"SAZW", "CUT"},
    {"SAZY", "CPC"}, {"SBAA", "CDJ"}, {"SBAC", "ARX"}, {"SBAE", "JTC"}, {"SBAQ", "AQA"}, {"SBAR", "AJU"},
    {"SBAT", "AFL"}, {"SBAU", "ARU"}, {"SBAX", "AAX"}, {"SBBE", "BEL"}, {"SBBG", "BGX"}, {"SBBH", "PLU"},
    {"SBBI", "BFH"}, {"SBBP", "BJP"}, {"SBBR", "BSB"}, {"SBBV", "BVB"}, {"SBBW", "BPG"}, {"SBCA", "CAC"},
    {"SBCB", "CFB"}, {"SBCD", "CFC"}, {"SBCF", "CNF"}, {"SBCG", "CGR"}, {"SBCH", "XAP"}, {"SBCI", "CLN"},
    {"SBCJ", "CKS"}, {"SBCN", "CLV"}, {"SBCP", "CAW"}, {"SBCR", "CMG"}, {"SBCT", "CWB"}, {"SBCX", "CXJ"},
    {"SBCY", "CGB"}, {"SBCZ", "CZS"}, {"SBDB", "BYO"}, {"SBDN", "PPB"}, {"SBEG", "MAO"}, {"SBEK", "JCR"},
    {"SBFI", "IGU"}, {"SBFL", "FLN"}, {"SBFN", "FEN"}, {"SBFZ", "FOR"}, {"SBGL", "GIG"}, {"SBGM", "GJM"},
    {"SBGO", "GYN"}, {"SBGR", "GRU"}, {"SBGV", "GVR"}, {"SBGW", "GUJ"}, {"SBHT", "ATM"}, {"SBIC", "ITA"},
    {"SBIH", "ITB"}, {"SBIL", "IOS"}, {"SBIP", "IPN"}, {"SBIT", "ITR"}, {"SBIZ", "IMP"}, {"SBJA", "JJG"},
    {"SBJE", "JJD"}, {"SBJF", "JDF"}, {"SBJH", "JHF"}, {"SBJI", "JPR"}, {"SBJP", "JPA"}, {"SBJR", "RRJ"},
    {"SBJU", "JDO"}, {"SBJV", "JOI"}, {"SBKG", "CPV"}, {"SBKP", "VCP"}, {"SBLE", "LEC"}, {"SBLJ", "LAJ"},
    {"SBLO", "LDB"}, {"SBLP", "LAZ"}, {"SBMA", "MAB"}, {"SBMD", "MEU"}, {"SBME", "MEA"}, {"SBMG", "MGF"},
    {"SBMK", "MOC"}, {"SBML", "MII"}, {"SBMN", "PLL"}, {"SBMO", "MCZ"}, {"SBMQ", "MCP"}, {"SBMS", "MVF"},
    {"SBMY", "MNX"}, {"SBNF", "NVT"}, {"SBNM", "GEL"}, {"SBOI", "OYK"}, {"SBPA", "POA"}, {"SBPB", "PHB"},
    {"SBPC", "POO"}, {"SBPF", "PFB"}, {"SBPG", "PGZ"}, {"SBPJ", "PMW"}, {"SBPK", "PET"}, {"SBPL", "PNZ"},
    {"SBPO", "PTO"}, {"SBPP", "PMG"}, {"SBPS", "BPS"}, {"SBPV", "PVH"}, {"SBRB", "RBR"}, {"SBRD", "ROO"},
    {"SBRF", "REC"}, {"SBRJ", "SDU"}, {"SBRP", "RAO"}, {"SBSG", "NAT"}, {"SBSI", "OPS"}, {"SBSJ", "SJK"},
    {"SBSL", "SLZ"}, {"SBSM", "RIA"}, {"SBSN", "STM"}, {"SBSO", "SMT"}, {"SBSP", "CGH"}, {"SBSR", "SJP"},
    {"SBST", "SSZ"}, {"SBSV", "SSA"}, {"SBTB", "TMT"}, {"SBTC", "UNA"}, {"SBTD", "TOW"}, {"SBTE", "THE"},
    {"SBTF", "TFF"}, {"SBTG", "TJL"}, {"SBTK", "TRQ"}, {"SBTT", "TBT"}, {"SBTU", "TUR"}, {"SBUA", "SJL"},
    {"SBUF", "PAV"}, {"SBUG", "URG"}, {"SBUL", "UDI"}, {"SBUR", "UBA"}, {"SBVC", "VDC"}, {"SBVG", "VAG"},
    {"SBVH", "BVH"}, {"SBVT", "VIX"}, {"SBZM", "IZA"}, {"SCAC", "ZUD"}, {"SCAN", "LOB"}, {"SCAP", "WAP"},
    {"SCAR", "ARI"}, {"SCAS", "WPA"}, {"SCAT", "CPO"}, {"SCBA", "BBA"}, {"SCBE", "TOQ"}, {"SCCC", "CCH"},
    {"SCCF", "CJC"}, {"SCCH", "YAI"}, {"SCCI", "PUQ"}, {"SCCY", "GXQ"}, {"SCDA", "IQQ"}, {"SCEL", "SCL"},
    {"SCES", "ESR"}, {"SCFA", "ANF"}, {"SCFM", "WPR"}, {"SCFT", "FFU"}, {"SCGC", "UGL"}, {"SCGE", "LSQ"},
    {"SCGZ", "WPU"}, {"SCHR", "LGR"}, {"SCIE", "CCP"}, {"SCIP", "IPC"}, {"SCJO", "ZOS"}, {"SCKP", "CPP"},
    {"SCLL", "VLR"}, {"SCNT", "PNT"}, {"SCOV", "OVL"}, {"SCPC", "ZPC"}, {"SCPQ", "MHC"}, {"SCPV", "PUX"},
    {"SCQP", "ZCO"}, {"SCRA", "CNR"}, {"SCRD", "VAP"}, {"SCRM", "TNM"}, {"SCSB", "SMB"}, {"SCSE", "LSC"},
    {"SCSF", "SSD"}, {"SCST", "WCA"}, {"SCTC", "PZS"}, {"SCTE", "PMC"}, {"SCTL", "TLX"}, {"SCTN", "WCH"},
    {"SCTO", "ZIC"}, {"SCTT", "TTC"}, {"SCVD", "ZAL"}, {"SCVM", "KNA"}, {"SDCG", "OLC"}, {"SDCO", "SOD"},
    {"SDIY", "FEC"}, {"SDJL", "JLS"}, {"SDOU", "OUS"}, {"SDOW", "OIA"}, {"SDRS", "REZ"}, {"SDSC", "QSC"},
    {"SDTK", "JPY"}, {"SDUB", "UBT"}, {"SDUN", "ITP"}, {"SDVG", "VOT"}, {"SEAM", "ATF"}, {"SECA", "LOH"},
    {"SECO", "OCC"}, {"SECU", "CUE"}, {"SEGS", "GPS"}, {"SEGU", "GYE"}, {"SEII", "IBB"}, {"SEJD", "TNW"},
    {"SEJI", "JIP"}, {"SELT", "LTX"}, {"SEMA", "MRR"}, {"SEMC", "XMS"}, {"SEMT", "MEC"}, {"SENL", "LGQ"},
    {"SEPT", "PYO"}, {"SEPV", "PVO"}, {"SEQM", "UIO"}, {"SERO", "ETR"}, {"SESA", "SNC"}, {"SESC", "SUQ"},
    {"SESM", "PTZ"}, {"SEST", "SCY"}, {"SESV", "BHA"}, {"SETH", "TSC"}, {"SETI", "TPN"}, {"SETN", "ESM"},
    {"SETR", "TPC"}, {"SETU", "TUA"}, {"SFAL", "PSY"}, {"SGAS", "ASU"}, {"SGAY", "AYO"}, {"SGBN", "BFA"},
    {"SGCO", "CIO"}, {"SGEN", "ENO"}, {"SGES", "AGT"}, {"SGFI", "FLM"}, {"SGME", "ESG"}, {"SGOL", "OLK"},
    {"SGPI", "PIL"}, {"SGPJ", "PJC"}, {"SILC", "LVR"}, {"SIMK", "FRC"}, {"SIRI", "MUU"}, {"SIZX", "JUA"},
    {"SJNP", "NPR"}, {"SJZA", "CJZ"}, {"SKAC", "ACR"}, {"SKAD", "ACD"}, {"SKAG", "HAY"}, {"SKAM", "AFI"},
    {"SKAP", "API"}, {"SKAR", "AXM"}, {"SKAS", "PUU"}, {"SKAT", "ARQ"}, {"SKBC", "ELB"}, {"SKBG", "BGA"},
    {"SKBM", "NBB"}, {"SKBO", "BOG"}, {"SKBQ", "BAQ"}, {"SKBS", "BSC"}, {"SKBU", "BUN"}, {"SKCA", "CPB"},
    {"SKCC", "CUC"}, {"SKCD", "COG"}, {"SKCG", "CTG"}, {"SKCI", "CCO"}, {"SKCL", "CLO"}, {"SKCM", "CIM"},
    {"SKCN", "RAV"}, {"SKCO", "TCO"}, {"SKCP", "BHF"}, {"SKCR", "CUO"}, {"SKCU", "CAQ"}, {"SKCV", "CVE"},
    {"SKCZ", "CZU"}, {"SKEB", "EBG"}, {"SKEH", "ECR"}, {"SKEJ", "EJA"}, {"SKFL", "FLA"}, {"SKGA", "LGT"},
    {"SKGI", "GIR"}, {"SKGO", "CRC"}, {"SKGP", "GPI"}, {"SKHA", "CPL"}, {"SKHC", "HTZ"}, {"SKIB", "IBE"},
    {"SKIG", "IGO"}, {"SKIM", "LPE"}, {"SKIP", "IPI"}, {"SKJU", "JUO"}, {"SKLC", "APO"}, {"SKLG", "LQM"},
    {"SKLM", "MCJ"}, {"SKLP", "LPD"}, {"SKLT", "LET"}, {"SKMB", "TBD"}, {"SKMD", "EOH"}, {"SKMF", "MFS"},
    {"SKMG", "MGN"}, {"SKML", "MTB"}, {"SKMP", "MMP"}, {"SKMR", "MTR"}, {"SKMU", "MVP"}, {"SKMZ", "MZL"},
    {"SKNA", "LMC"}, {"SKNC", "NCI"}, {"SKNQ", "NQU"}, {"SKNV", "NVA"}, {"SKOC", "OCV"}, {"SKOE", "ORC"},
    {"SKOT", "OTU"}, {"SKPA", "RON"}, {"SKPC", "PCR"}, {"SKPD", "PDA"}, {"SKPE", "PEI"}, {"SKPI", "PTX"},
    {"SKPL", "PLT"}, {"SKPN", "NAR"}, {"SKPP", "PPN"}, {"SKPQ", "PAL"}, {"SKPR", "PBE"}, {"SKPS", "PSO"},
    {"SKPV", "PVA"}, {"SKPZ", "PZA"}, {"SKQU", "MQU"}, {"SKRA", "TCD"}, {"SKRG", "MDE"}, {"SKRH", "RCH"},
    {"SKRU", "SNT"}, {"SKSA", "RVE"}, {"SKSJ", "SJE"}, {"SKSL", "SSL"}, {"SKSM", "SMR"}, {"SKSO", "SOX"},
    {"SKSP", "ADZ"}, {"SKSV", "SVI"}, {"SKTA", "TAU"}, {"SKTB", "TIB"}, {"SKTD", "TDA"}, {"SKTL", "TLU"},
    {"SKTM", "TME"}, {"SKTQ", "TQS"}, {"SKTU", "TRB"}, {"SKUB", "URI"}, {"SKUC", "AUC"}, {"SKUI", "UIB"},
    {"SKUL", "ULQ"}, {"SKUR", "URR"}, {"SKVG", "VGZ"}, {"SKVL", "PYA"}, {"SKVP", "VUP"}, {"SKVV", "VVC"},
    {"SKYA", "AYG"}, {"SKYP", "EYP"}, {"SLAG", "MHW"}, {"SLAL", "SRE"}, {"SLAP", "APB"}, {"SLAS", "ASC"},
    {"SLBJ", "BJO"}, {"SLCA", "CAM"}, {"SLCB", "CBB"}, {"SLCO", "CIJ"}, {"SLCP", "CEP"}, {"SLET", "SRZ"},
    {"SLGM", "GYA"}, {"SLHI", "CCA"}, {"SLHJ", "BVK"}, {"SLJE", "SJS"}, {"SLJO", "SJB"}, {"SLJV", "SJV"},
    {"SLLP", "LPB"}, {"SLMG", "MGD"}, {"SLOR", "ORU"}, {"SLPO", "POI"}, {"SLPR", "PUR"}, {"SLPS", "PSZ"},
    {"SLRA", "SRD"}, {"SLRB", "RBO"}, {"SLRI", "RIB"}, {"SLRQ", "RBQ"}, {"SLRY", "REY"}, {"SLSA", "SBL"},
    {"SLSB", "SRJ"}, {"SLSI", "SNG"}, {"SLSM", "SNM"}, {"SLSR", "SRB"}, {"SLTI", "MQK"}, {"SLTJ", "TJA"},
    {"SLTR", "TDD"}, {"SLUY", "UYU"}, {"SLVG", "VAH"}, {"SLVM", "VLM"}, {"SLVR", "VVI"}, {"SLYA", "BYC"},
    {"SMBN", "ABN"}, {"SMCA", "AAJ"}, {"SMCO", "TOT"}, {"SMDA", "DRJ"}, {"SMDO", "LDO"}, {"SMEG", "EAX"},
    {"SMJP", "PBM"}, {"SMMO", "MOJ"}, {"SMNI", "ICK"}, {"SMPA", "OEM"}, {"SMST", "SMZ"}, {"SMTP", "KCB"},
    {"SMWA", "AGI"}, {"SMWS", "WSO"}, {"SMZO", "ORG"}, {"SNAL", "APQ"}, {"SNAR", "AMJ"}, {"SNBC", "BDC"},
    {"SNBR", "BRA"}, {"SNBS", "BSS"}, {"SNBX", "BQQ"}, {"SNCP", "EEA"}, {"SNDC", "RDC"}, {"SNDT", "DTI"},
    {"SNDV", "DIQ"}, {"SNEB", "JPE"}, {"SNED", "CNV"}, {"SNFX", "SXX"}, {"SNGA", "GUZ"}, {"SNGD", "GDP"},
    {"SNGI", "GNM"}, {"SNGN", "QGP"}, {"SNHS", "SET"}, {"SNIC", "IRE"}, {"SNIU", "IPU"}, {"SNJB", "JCM"},
    {"SNJK", "JEQ"}, {"SNJN", "JNA"}, {"SNJR", "JDR"}, {"SNKI", "CDI"}, {"SNLO", "SSO"}, {"SNMA", "MTE"},
    {"SNMU", "MVS"}, {"SNMX", "SBJ"}, {"SNMZ", "PTQ"}, {"SNNU", "NNU"}, {"SNOU", "FEJ"}, {"SNOX", "ORX"},
    {"SNPC", "PCS"}, {"SNPD", "POJ"}, {"SNPX", "PIV"}, {"SNQG", "FLB"}, {"SNRD", "PDF"}, {"SNRU", "CAU"},
    {"SNSM", "OPP"}, {"SNTF", "TXF"}, {"SNTI", "OBI"}, {"SNTO", "TFL"}, {"SNVB", "VAL"}, {"SNVS", "BVS"},
    {"SNWC", "CMC"}, {"SNYA", "GGF"}, {"SNYE", "PHI"}, {"SNZA", "PPY"}, {"SNZR", "PYT"}, {"SNZW", "ITE"},
    {"SOCA", "CAY"}, {"SOGS", "GSI"}, {"SOOA", "MPY"}, {"SOOG", "OYP"}, {"SOOM", "LDX"}, {"SOOR", "REI"},
    {"SOOS", "XAU"}, {"SPAR", "ALD"}, {"SPAY", "AYX"}, {"SPBB", "MBP"}, {"SPBR", "IBP"}, {"SPCL", "PCL"},
    {"SPDR", "TDP"}, {"SPEO", "CHM"}, {"SPGL", "CGL"}, {"SPGM", "TGI"}, {"SPHI", "CIX"}, {"SPHO", "AYP"},
    {"SPHY", "ANS"}, {"SPHZ", "ATA"}, {"SPIL", "UMI"}, {"SPJA", "RIJ"}, {"SPJC", "LIM"}, {"SPJE", "JAE"},
    {"SPJI", "JJI"}, {"SPJJ", "JAU"}, {"SPJL", "JUL"}, {"SPJN", "SJA"}, {"SPJR", "CJA"}, {"SPLN", "RIM"},
    {"SPLO", "ILQ"}, {"SPME", "TBP"}, {"SPMF", "MZA"}, {"SPMS", "YMS"}, {"SPNC", "HUU"}, {"SPOA", "SQU"},
    {"SPPY", "CHH"}, {"SPQT", "IQT"}, {"SPQU", "AQP"}, {"SPRU", "TRU"}, {"SPSO", "PIO"}, {"SPST", "TPP"},
    {"SPSY", "SYC"}, {"SPTN", "TCQ"}, {"SPTU", "PEM"}, {"SPUR", "PIU"}, {"SPYL", "TYL"}, {"SPZA", "NZC"},
    {"SPZO", "CUZ"}, {"SSAP", "APU"}, {"SSBL", "BNU"}, {"SSCK", "CCI"}, {"SSCL", "CSS"}, {"SSCN", "CEL"},
    {"SSCP", "CKO"}, {"SSCT", "GGH"}, {"SSER", "ERM"}, {"SSFB", "FBE"}, {"SSGG", "GPB"}, {"SSGY", "GGJ"},
    {"SSHZ", "HRZ"}, {"SSIJ", "IJU"}, {"SSIM", "CCM"}, {"SSIQ", "ITQ"}, {"SSJA", "JCB"}, {"SSKM", "CBW"},
    {"SSKW", "OAL"}, {"SSLN", "LOI"}, {"SSLT", "ALQ"}, {"SSOE", "SQX"}, {"SSOG", "APX"}, {"SSOU", "AIR"},
    {"SSPG", "PNG"}, {"SSPI", "PVI"}, {"SSPN", "PBB"}, {"SSRS", "BRB"}, {"SSRU", "SQY"}, {"SSSC", "CSU"},
    {"SSUM", "UMU"}, {"SSUV", "UVI"}, {"SSVI", "VIA"}, {"SSXH", "BMS"}, {"SSZR", "SRA"}, {"SUAG", "ATI"},
    {"SUBU", "BUV"}, {"SUCA", "CYR"}, {"SUDU", "DZO"}, {"SULS", "PDP"}, {"SUMO", "MLZ"}, {"SUMU", "MVD"},
    {"SUPU", "PDU"}, {"SURV", "RVY"}, {"SUSO", "STY"}, {"SUTB", "TAW"}, {"SUTR", "TYT"}, {"SUVO", "VCH"},
    {"SVAC", "AGV"}, {"SVAN", "AAO"}, {"SVBC", "BLA"}, {"SVBI", "BNS"}, {"SVBM", "BRM"}, {"SVBS", "MYC"},
    {"SVCB", "CBL"}, {"SVCD", "CXA"}, {"SVCG", "CUV"}, {"SVCL", "CLZ"}, {"SVCN", "CAJ"}, {"SVCP", "CUP"},
    {"SVCR", "CZE"}, {"SVCU", "CUM"}, {"SVED", "EOR"}, {"SVEZ", "EOZ"}, {"SVGD", "GDO"}, {"SVGI", "GUI"},
    {"SVGU", "GUQ"}, {"SVHG", "HGE"}, {"SVIC", "ICA"}, {"SVIE", "ICC"}, {"SVJC", "LSP"}, {"SVKA", "KAV"},
    {"SVKM", "KTV"}, {"SVLF", "LFR"}, {"SVMC", "MAR"}, {"SVMD", "MRD"}, {"SVMG", "PMV"}, {"SVMI", "CCS"},
    {"SVMT", "MUN"}, {"SVON", "CBS"}, {"SVPA", "PYH"}, {"SVPC", "PBL"}, {"SVPE", "PDZ"}, {"SVPM", "SCI"},
    {"SVPP", "PPZ"}, {"SVPR", "PZO"}, {"SVPT", "PTM"}, {"SVPX", "PPH"}, {"SVRS", "LRV"}, {"SVSA", "SVZ"},
    {"SVSB", "SBB"}, {"SVSE", "SNV"}, {"SVSO", "STD"}, {"SVSP", "SNF"}, {"SVSR", "SFD"}, {"SVST", "SOM"},
    {"SVSZ", "STB"}, {"SVTC", "TUV"}, {"SVTM", "TMO"}, {"SVUM", "URM"}, {"SVUQ", "WOK"}, {"SVVA", "VLN"},
    {"SVVG", "VIG"}, {"SVVL", "VLV"}, {"SVVP", "VDP"}, {"SWBC", "BAZ"}, {"SWBG", "LCB"}, {"SWBR", "RBB"},
    {"SWCA", "CAF"}, {"SWCQ", "CQS"}, {"SWDM", "DMT"}, {"SWDN", "DNO"}, {"SWEI", "ERN"}, {"SWEK", "CQA"},
    {"SWFX", "SXO"}, {"SWGI", "GRP"}, {"SWGN", "AUX"}, {"SWHP", "GGB"}, {"SWHT", "HUW"}, {"SWII", "IPG"},
    {"SWIY", "IDO"}, {"SWJN", "JIA"}, {"SWJW", "JTI"}, {"SWKC", "CCX"}, {"SWKO", "CIZ"}, {"SWKT", "TLZ"},
    {"SWLB", "LBR"}, {"SWLC", "RVD"}, {"SWMW", "MBZ"}, {"SWNA", "NVP"}, {"SWNK", "BCR"}, {"SWNQ", "NQL"},
    {"SWNS", "APS"}, {"SWOB", "FBA"}, {"SWPI", "PIN"}, {"SWPM", "PBQ"}, {"SWPQ", "PBX"}, {"SWTP", "IRZ"},
    {"SWTS", "TGQ"}, {"SWTU", "AZL"}, {"SWUA", "SQM"}, {"SWVC", "VLP"}, {"SWXM", "MBK"}, {"SWXV", "NOK"},
    {"SYAH", "AHL"}, {"SYAN", "NAI"}, {"SYBE", "BCG"}, {"SYBR", "BMJ"}, {"SYBT", "GFO"}, {"SYCJ", "GEO"},
    {"SYEC", "OGL"}, {"SYIB", "IMB"}, {"SYKA", "KAI"}, {"SYKM", "KAR"}, {"SYKR", "KRM"}, {"SYKS", "KRG"},
    {"SYKT", "KTO"}, {"SYKZ", "KKG"}, {"SYLP", "LUB"}, {"SYLT", "LTM"}, {"SYMB", "USI"}, {"SYMD", "MHA"},
    {"SYMK", "VEG"}, {"SYMM", "MYM"}, {"SYMR", "MWJ"}, {"SYOR", "ORJ"}, {"SYPK", "PKM"}, {"SYPM", "PMT"},
    {"SYPR", "PRR"}, {"SYSC", "SDC"}, {"SYSK", "SKM"}, {"TAPA", "ANU"}, {"TAPB", "BBQ"}, {"TBPB", "BGI"},
    {"TDCF", "DCF"}, {"TDPD", "DOM"}, {"TFFA", "DSD"}, {"TFFB", "BBR"}, {"TFFC", "SFC"}, {"TFFF", "FDF"},
    {"TFFG", "SFG"}, {"TFFJ", "SBH"}, {"TFFM", "GBJ"}, {"TFFR", "PTP"}, {"TFFS", "LSS"}, {"TGPY", "GND"},
    {"TGPZ", "CRU"}, {"TIST", "STT"}, {"TISX", "STX"}, {"TJAB", "ARE"}, {"TJBQ", "BQN"}, {"TJCP", "CPX"},
    {"TJIG", "SIG"}, {"TJMZ", "MAZ"}, {"TJPS", "PSE"}, {"TJRV", "NRR"}, {"TJSJ", "SJU"}, {"TJVQ", "VQS"},
    {"TKPK", "SKB"}, {"TKPN", "NEV"}, {"TLPC", "SLU"}, {"TLPL", "UVF"}, {"TNCA", "AUA"}, {"TNCB", "BON"},
    {"TNCC", "CUR"}, {"TNCE", "EUX"}, {"TNCM", "SXM"}, {"TNCS", "SAB"}, {"TQPF", "AXA"}, {"TRPG", "MNI"},
    {"TTCP", "TAB"}, {"TTPP", "POS"}, {"TUPA", "NGD"}, {"TUPJ", "EIS"}, {"TUPW", "VIJ"}, {"TVSA", "SVD"},
    {"TVSB", "BQU"}, {"TVSC", "CIW"}, {"TVSM", "MQS"}, {"TVSU", "UNI"}, {"TXKF", "BDA"}, {"UAAA", "ALA"},
    {"UAAH", "BXH"}, {"UAAL", "USJ"}, {"UAAR", "BXJ"}, {"UAAT", "TDK"}, {"UACC", "NQZ"}, {"UACK", "KOV"},
    {"UACP", "PPK"}, {"UADD", "DMB"}, {"UAII", "CIT"}, {"UAIT", "HSA"}, {"UAKD", "DZN"}, {"UAKK", "KGF"},
    {"UAOL", "BXY"}, {"UAOO", "KZO"}, {"UARR", "URA"}, {"UASB", "EKB"}, {"UASK", "UKK"}, {"UASP", "PWQ"},
    {"UASS", "PLX"}, {"UASU", "UZR"}, {"UASZ", "SZI"}, {"UATE", "SCO"}, {"UATG", "GUW"}, {"UATT", "AKX"},
    {"UAUR", "AYK"}, {"UAUU", "KSN"}, {"UBBB", "GYD"}, {"UBBF", "FZL"}, {"UBBG", "GNJ"}, {"UBBL", "LLK"},
    {"UBBN", "NAJ"}, {"UBBQ", "GBB"}, {"UBBY", "ZTU"}, {"UBEE", "YLV"}, {"UBLC", "LHL"}, {"UBTT", "ZXT"},
    {"UCFK", "IKG"}, {"UCFL", "IKU"}, {"UCFM", "BSZ"}, {"UCFO", "OSS"}, {"UDCK", "YUK"}, {"UDSG", "LWN"},
    {"UDYZ", "EVN"}, {"UEBB", "BQJ"}, {"UEBS", "SUK"}, {"UEBT", "UKG"}, {"UECT", "TLK"}, {"UEEA", "ADH"},
    {"UEEE", "YKS"}, {"UELL", "NER"}, {"UEMA", "MQJ"}, {"UEMH", "KDY"}, {"UEMM", "GYG"}, {"UEMO", "OLZ"},
    {"UEMT", "USR"}, {"UEMU", "UMS"}, {"UENI", "VHV"}, {"UENN", "NYR"}, {"UENS", "SUY"}, {"UENW", "VYI"},
    {"UERL", "ULK"}, {"UERP", "PYJ"}, {"UERR", "MJZ"}, {"UERS", "SYS"}, {"UESG", "BGN"}, {"UESO", "CKH"},
    {"UESS", "CYX"}, {"UEST", "IKS"}, {"UESU", "ZKP"}, {"UEVV", "ZIX"}, {"UGKO", "KUT"}, {"UGSB", "BUS"},
    {"UGSS", "SUI"}, {"UGTB", "TBS"}, {"UHBB", "BQS"}, {"UHBW", "TYD"}, {"UHHH", "KHV"}, {"UHKK", "KXK"},
    {"UHKM", "GVN"}, {"UHMA", "DYR"}, {"UHMD", "PVS"}, {"UHMK", "KPW"}, {"UHMM", "GDX"}, {"UHMO", "KVM"},
    {"UHMP", "PWE"}, {"UHMW", "SWV"}, {"UHNB", "BQG"}, {"UHNN", "NLI"}, {"UHOO", "OHO"}, {"UHPP", "PKC"},
    {"UHSB", "BVV"}, {"UHSH", "OHH"}, {"UHSI", "ITU"}, {"UHSK", "EKS"}, {"UHSM", "DEE"}, {"UHSO", "ZZO"},
    {"UHSS", "UUS"}, {"UHTG", "AEM"}, {"UHWP", "TLY"}, {"UHWW", "VVO"}, {"UIAA", "HTA"}, {"UIBB", "BTK"},
    {"UIII", "IKT"}, {"UIKB", "ODO"}, {"UIKE", "ERG"}, {"UIKK", "KCK"}, {"UITT", "UKX"}, {"UIUN", "NZG"},
    {"UIUU", "UUD"}, {"UKBB", "KBP"}, {"UKCK", "KRQ"}, {"UKCM", "MPW"}, {"UKDB", "ERD"}, {"UKDD", "DNK"},
    {"UKDE", "OZH"}, {"UKDR", "KWG"}, {"UKFB", "UKS"}, {"UKFF", "SIP"}, {"UKFK", "KHC"}, {"UKHH", "HRK"},
    {"UKHP", "PLV"}, {"UKHS", "UMY"}, {"UKKE", "CKC"}, {"UKKG", "KGO"}, {"UKKV", "ZTR"}, {"UKLC", "UCK"},
    {"UKLH", "HMJ"}, {"UKLI", "IFO"}, {"UKLL", "LWO"}, {"UKLN", "CWC"}, {"UKLR", "RWN"}, {"UKLT", "TNL"},
    {"UKLU", "UDJ"}, {"UKOH", "KHE"}, {"UKOO", "ODS"}, {"UKWW", "VIN"}, {"ULAA", "ARH"}, {"ULAL", "LDG"},
    {"ULAM", "NNM"}, {"ULDD", "AMV"}, {"ULDW", "VRI"}, {"ULKK", "KSZ"}, {"ULLI", "LED"}, {"ULMM", "MMK"},
    {"ULOL", "VLU"}, {"ULOO", "PKV"}, {"ULPB", "PES"}, {"ULWC", "CEE"}, {"ULWU", "VUS"}, {"ULWW", "VGD"},
    {"UMBB", "BQT"}, {"UMGG", "GME"}, {"UMII", "VTB"}, {"UMKK", "KGD"}, {"UMMG", "GNA"}, {"UMMS", "MSQ"},
    {"UMOO", "MVQ"}, {"UNAA", "ABA"}, {"UNBB", "BAX"}, {"UNBG", "RGK"}, {"UNEE", "KEJ"}, {"UNII", "EIE"},
    {"UNIP", "TGP"}, {"UNIS", "VEO"}, {"UNIT", "GOY"}, {"UNIW", "VAQ"}, {"UNKL", "KJA"}, {"UNKM", "KCY"},
    {"UNKS", "ACS"}, {"UNKY", "KYZ"}, {"UNNT", "OVB"}, {"UNOO", "OMS"}, {"UNSS", "SWT"}, {"UNTT", "TOF"},
    {"UNWW", "NOZ"}, {"UODD", "DKS"}, {"UOHH", "HTG"}, {"UOII", "IAA"}, {"UOOO", "NSK"}, {"UOTT", "THX"},
    {"URKA", "AAQ"}, {"URKG", "GDZ"}, {"URKK", "KRR"}, {"URMG", "GRV"}, {"URML", "MCX"}, {"URMM", "MRV"},
    {"URMN", "NAL"}, {"URMO", "OGZ"}, {"URMS", "IGT"}, {"URMT", "STW"}, {"URRP", "ROV"}, {"URRT", "TGK"},
    {"URSS", "AER"}, {"URWA", "ASF"}, {"URWI", "ESL"}, {"URWW", "VOG"}, {"USCC", "CEK"}, {"USCM", "MQF"},
    {"USDA", "SBT"}, {"USDB", "BVJ"}, {"USDD", "SLY"}, {"USDK", "YMK"}, {"USDP", "KKQ"}, {"USDS", "TQL"},
    {"USDU", "UEN"}, {"USHH", "HMA"}, {"USHI", "IRM"}, {"USHK", "KXD"}, {"USHN", "NYA"}, {"USHQ", "EYK"},
    {"USHS", "OVS"}, {"USHU", "URJ"}, {"USII", "IJK"}, {"USKK", "KVX"}, {"USMM", "NYM"}, {"USMU", "NUX"},
    {"USNN", "NJC"}, {"USPP", "PEE"}, {"USRK", "KGP"}, {"USRN", "NFG"}, {"USRO", "NOJ"}, {"USRR", "SGC"},
    {"USSS", "SVX"}, {"USTJ", "RMZ"}, {"USTO", "TOX"}, {"USTR", "TJM"}, {"USUU", "KRO"}, {"UTAA", "ASB"},
    {"UTAE", "KEA"}, {"UTAK", "KRW"}, {"UTAM", "MYP"}, {"UTAN", "BKN"}, {"UTAT", "TAZ"}, {"UTAV", "CRZ"},
    {"UTDD", "DYU"}, {"UTDK", "TJU"}, {"UTDL", "LBD"}, {"UTDT", "KQT"}, {"UUBA", "KMW"}, {"UUBC", "KLF"},
    {"UUBI", "IWA"}, {"UUBK", "RYB"}, {"UUBP", "BZK"}, {"UUBW", "ZIA"}, {"UUDD", "DME"}, {"UUDL", "IAR"},
    {"UUEE", "SVO"}, {"UUEM", "KLD"}, {"UUMU", "CKL"}, {"UUOB", "EGO"}, {"UUOK", "URS"}, {"UUOL", "LPK"},
    {"UUOO", "VOZ"}, {"UUOT", "TBW"}, {"UUWW", "VKO"}, {"UUYH", "UCT"}, {"UUYI", "INA"}, {"UUYP", "PEX"},
    {"UUYS", "USK"}, {"UUYW", "VKT"}, {"UUYX", "UTS"}, {"UUYY", "SCW"}, {"UWGG", "GOJ"}, {"UWKB", "UUA"},
    {"UWKD", "KZN"}, {"UWKE", "NBC"}, {"UWKJ", "JOK"}, {"UWKS", "CSY"}, {"UWLL", "ULV"}, {"UWLW", "ULY"},
    {"UWOO", "REN"}, {"UWOR", "OSW"}, {"UWPP", "PEZ"}, {"UWPS", "SKX"}, {"UWSB", "BWO"}, {"UWSG", "GSV"},
    {"UWUB", "BCX"}, {"UWUK", "OKT"}, {"UWUU", "UFA"}, {"UWWW", "KUF"}, {"UZFA", "AZN"}, {"UZFF", "FEG"},
    {"UZFN", "NMA"}, {"UZKK", "OQN"}, {"UZNM", "MOK"}, {"UZNN", "NCU"}, {"UZNU", "UGC"}, {"UZSA", "NVI"},
    {"UZSB", "BHK"}, {"UZSK", "KSQ"}, {"UZSN", "AFS"}, {"UZSS", "SKD"}, {"UZST", "TMJ"}, {"UZTP", "TVT"},
    {"UZTT", "TAS"}, {"UZTZ", "OMN"}, {"VAAH", "AMD"}, {"VAAK", "AKD"}, {"VAAU", "IXU"}, {"VABB", "BOM"},
    {"VABJ", "BHJ"}, {"VABO", "BDQ"}, {"VABP", "BHO"}, {"VABV", "BHU"}, {"VADN", "NMB"}, {"VADU", "DIU"},
    {"VAGD", "GDB"}, {"VAGN", "GUX"}, {"VAHS", "HSR"}, {"VAID", "IDR"}, {"VAJB", "JLR"}, {"VAJL", "JLG"},
    {"VAJM", "JGA"}, {"VAKE", "IXY"}, {"VAKP", "KLH"}, {"VAKS", "IXK"}, {"VALT", "LTU"}, {"VAND", "NDC"},
    {"VANM", "NMI"}, {"VANP", "NAG"}, {"VAOZ", "ISK"}, {"VAPO", "PNQ"}, {"VAPR", "PBD"}, {"VARG", "RTC"},
    {"VARK", "RAJ"}, {"VASD", "SAG"}, {"VASL", "SSE"}, {"VASU", "STV"}, {"VAUD", "UDR"}, {"VCBI", "CMB"},
    {"VCCA", "ACJ"}, {"VCCB", "BTC"}, {"VCCC", "RML"}, {"VCCG", "ADP"}, {"VCCH", "HIM"}, {"VCCJ", "JAF"},
    {"VCCK", "KCT"}, {"VCCN", "KTY"}, {"VCCS", "GIU"}, {"VCCT", "TRR"}, {"VCCW", "WRZ"}, {"VCRI", "HRI"},
    {"VDBG", "BBM"}, {"VDDS", "DSY"}, {"VDKK", "KKZ"}, {"VDMK", "MWV"}, {"VDPP", "PNH"}, {"VDRK", "RBE"},
    {"VDSA", "SAI"}, {"VDSV", "KOS"}, {"VDTI", "KTI"}, {"VEAB", "IXD"}, {"VEAN", "IXV"}, {"VEAP", "AHA"},
    {"VEAT", "IXA"}, {"VEAY", "AYJ"}, {"VEBD", "IXB"}, {"VEBG", "RGH"}, {"VEBI", "SHL"}, {"VEBN", "VNS"},
    {"VEBS", "BBI"}, {"VEBU", "PAB"}, {"VECC", "CCU"}, {"VECO", "COH"}, {"VECX", "KNU"}, {"VEDB", "DBD"},
    {"VEDG", "RDP"}, {"VEDH", "DBR"}, {"VEDO", "DGH"}, {"VEDZ", "DEP"}, {"VEGK", "GOP"}, {"VEGT", "GAU"},
    {"VEGY", "GAY"}, {"VEHO", "HGI"}, {"VEIM", "IMF"}, {"VEJH", "JRG"}, {"VEJP", "PYB"}, {"VEJR", "JGB"},
    {"VEJS", "IXW"}, {"VEJT", "JRH"}, {"VEKI", "KBK"}, {"VEKM", "IXQ"}, {"VEKO", "HJR"}, {"VEKR", "IXH"},
    {"VEKU", "IXS"}, {"VEKW", "IXN"}, {"VELP", "AJL"}, {"VELR", "IXI"}, {"VEMH", "LDA"}, {"VEMN", "DIB"},
    {"VEMR", "DMU"}, {"VEMZ", "MZU"}, {"VEPG", "IXT"}, {"VEPT", "PAT"}, {"VEPY", "PYG"}, {"VERC", "IXR"},
    {"VERK", "RRK"}, {"VERP", "RPR"}, {"VERU", "RUP"}, {"VERW", "REW"}, {"VETJ", "TEI"}, {"VETZ", "TEZ"},
    {"VEUK", "UKE"}, {"VEZO", "ZER"}, {"VGBR", "BZL"}, {"VGCB", "CXB"}, {"VGCM", "CLA"}, {"VGEG", "CGP"},
    {"VGHS", "DAC"}, {"VGIS", "IRD"}, {"VGJR", "JSR"}, {"VGRJ", "RJH"}, {"VGSD", "SPD"}, {"VGSG", "TKR"},
    {"VGSH", "ZHM"}, {"VGSY", "ZYL"}, {"VHHH", "HKG"}, {"VHSS", "HHP"}, {"VIAG", "AGR"}, {"VIAH", "HRH"},
    {"VIAR", "ATQ"}, {"VIAX", "AIP"}, {"VIBK", "BKB"}, {"VIBR", "KUU"}, {"VIBT", "BUP"}, {"VIBY", "BEK"},
    {"VICG", "IXC"}, {"VIDN", "DED"}, {"VIDP", "DEL"}, {"VIDX", "HDO"}, {"VIGG", "DHM"}, {"VIGR", "GWL"},
    {"VIHR", "HSS"}, {"VIHX", "HWR"}, {"VIJO", "JDH"}, {"VIJP", "JAI"}, {"VIJR", "JSA"}, {"VIJU", "IXJ"},
    {"VIKG", "KQH"}, {"VIKO", "KTU"}, {"VILD", "LUH"}, {"VILH", "IXL"}, {"VILK", "LKO"}, {"VIMB", "MZS"},
    {"VIND", "DXN"}, {"VIPK", "IXP"}, {"VIPT", "PGH"}, {"VISM", "SLV"}, {"VISR", "SXR"}, {"VISV", "VSV"},
    {"VLAP", "AOU"}, {"VLBK", "BOR"}, {"VLHS", "HOE"}, {"VLLB", "LPQ"}, {"VLLN", "LXG"}, {"VLOS", "ODY"},
    {"VLPS", "PKZ"}, {"VLSB", "ZBY"}, {"VLSK", "ZVK"}, {"VLSN", "NEU"}, {"VLSV", "VNA"}, {"VLTK", "THK"},
    {"VLVT", "VTE"}, {"VLXK", "XKH"}, {"VMMC", "MFM"}, {"VNBG", "BJH"}, {"VNBJ", "BHP"}, {"VNBL", "BGL"},
    {"VNBP", "BHR"}, {"VNBR", "BJU"}, {"VNBT", "BIT"}, {"VNBW", "BWA"}, {"VNCG", "BDP"}, {"VNDG", "DNP"},
    {"VNDH", "DHI"}, {"VNDL", "DAP"}, {"VNDP", "DOP"}, {"VNDT", "SIH"}, {"VNGK", "GKH"}, {"VNJI", "JIR"},
    {"VNJL", "JUM"}, {"VNJP", "JKR"}, {"VNJS", "JMO"}, {"VNKT", "KTM"}, {"VNLD", "LDN"}, {"VNLK", "LUA"},
    {"VNLT", "LTG"}, {"VNMA", "NGX"}, {"VNMG", "MEY"}, {"VNMN", "XMG"}, {"VNNG", "KEP"}, {"VNPK", "PKR"},
    {"VNPL", "PPL"}, {"VNPR", "PHH"}, {"VNRB", "RJB"}, {"VNRC", "RHP"}, {"VNRP", "RPA"}, {"VNRT", "RUM"},
    {"VNSB", "SYH"}, {"VNSI", "SIF"}, {"VNSK", "SKH"}, {"VNSR", "FEB"}, {"VNST", "IMK"}, {"VNTJ", "TPJ"},
    {"VNTP", "TPU"}, {"VNTR", "TMI"}, {"VNVT", "BIR"}, {"VOAT", "AGX"}, {"VOBI", "BEP"}, {"VOBL", "BLR"},
    {"VOBM", "IXG"}, {"VOBR", "IXX"}, {"VOBZ", "VGA"}, {"VOCB", "CJB"}, {"VOCI", "COK"}, {"VOCL", "CCJ"},
    {"VOCP", "CDP"}, {"VOCX", "CBD"}, {"VOGA", "GOX"}, {"VOGB", "GBI"}, {"VOGO", "GOI"}, {"VOHB", "HBX"},
    {"VOHS", "HYD"}, {"VOHY", "BPM"}, {"VOJV", "VDY"}, {"VOKN", "CNN"}, {"VOKU", "KJB"}, {"VOMD", "IXM"},
    {"VOML", "IXE"}, {"VOMM", "MAA"}, {"VOMY", "MYQ"}, {"VONV", "NVY"}, {"VOPB", "IXZ"}, {"VOPC", "PNY"},
    {"VOPN", "PUT"}, {"VORG", "RMD"}, {"VORY", "RJA"}, {"VOSH", "RQY"}, {"VOSM", "SXV"}, {"VOSR", "SDW"},
    {"VOTJ", "TJV"}, {"VOTK", "TCR"}, {"VOTP", "TIR"}, {"VOTR", "TRZ"}, {"VOTV", "TRV"}, {"VOVZ", "VTZ"},
    {"VOWA", "WGC"}, {"VQBT", "BUT"}, {"VQGP", "GLU"}, {"VQPR", "PBH"}, {"VQTY", "YON"}, {"VRAH", "HRF"},
    {"VRBK", "HDK"}, {"VRCF", "FND"}, {"VRDA", "NMF"}, {"VREI", "IFU"}, {"VRMD", "DRV"}, {"VRMG", "GAN"},
    {"VRMH", "HAQ"}, {"VRMK", "KDO"}, {"VRMM", "MLE"}, {"VRMO", "GKK"}, {"VRMT", "KDM"}, {"VRMU", "DDD"},
    {"VRMV", "VAM"}, {"VRNT", "TMF"}, {"VRQF", "FMT"}, {"VRQM", "RUL"}, {"VTBD", "DMK"}, {"VTBK", "KDT"},
    {"VTBL", "KKM"}, {"VTBO", "TDX"}, {"VTBS", "BKK"}, {"VTBU", "UTP"}, {"VTCC", "CNX"}, {"VTCH", "HGN"},
    {"VTCL", "LPT"}, {"VTCN", "NNT"}, {"VTCP", "PRH"}, {"VTCT", "CEI"}, {"VTPB", "PHY"}, {"VTPH", "HHQ"},
    {"VTPI", "TKH"}, {"VTPM", "MAQ"}, {"VTPO", "THS"}, {"VTPP", "PHS"}, {"VTPT", "TKT"}, {"VTSB", "URT"},
    {"VTSC", "NAW"}, {"VTSE", "CJM"}, {"VTSF", "NST"}, {"VTSG", "KBV"}, {"VTSH", "SGZ"}, {"VTSK", "PAN"},
    {"VTSM", "USM"}, {"VTSP", "HKT"}, {"VTSR", "UNN"}, {"VTSS", "HDY"}, {"VTST", "TST"}, {"VTSY", "BTZ"},
    {"VTUD", "UTH"}, {"VTUI", "SNO"}, {"VTUJ", "PXR"}, {"VTUK", "KKC"}, {"VTUL", "LOE"}, {"VTUO", "BFV"},
    {"VTUQ", "NAK"}, {"VTUU", "UBP"}, {"VTUV", "ROI"}, {"VTUW", "KOP"}, {"VVBM", "BMV"}, {"VVCA", "VCL"},
    {"VVCI", "HPH"}, {"VVCM", "CAH"}, {"VVCR", "CXR"}, {"VVCS", "VCS"}, {"VVCT", "VCA"}, {"VVDB", "DIN"},
    {"VVDH", "VDH"}, {"VVDL", "DLI"}, {"VVDN", "DAD"}, {"VVLT", "LTH"}, {"VVNB", "HAN"}, {"VVNS", "SQH"},
    {"VVPB", "HUI"}, {"VVPC", "UIH"}, {"VVPK", "PXU"}, {"VVPQ", "PQC"}, {"VVPR", "PHA"}, {"VVRG", "VKG"},
    {"VVTH", "TBB"}, {"VVTS", "SGN"}, {"VVTX", "THD"}, {"VVVD", "VDO"}, {"VVVH", "VII"}, {"VVVT", "VTG"},
    {"VYAN", "VBA"}, {"VYBG", "NYU"}, {"VYBM", "BMO"}, {"VYBP", "VBP"}, {"VYCZ", "VBC"}, {"VYDW", "TVY"},
    {"VYGG", "GAW"}, {"VYGW", "GWA"}, {"VYHH", "HEH"}, {"VYHL", "HOX"}, {"VYHN", "TIO"}, {"VYKG", "KET"},
    {"VYKI", "KHM"}, {"VYKL", "KMV"}, {"VYKP", "KYP"}, {"VYKT", "KAW"}, {"VYKU", "KYT"}, {"VYLK", "LIW"},
    {"VYLS", "LSH"}, {"VYMD", "MDL"}, {"VYME", "MGZ"}, {"VYMK", "MYT"}, {"VYMM", "MNU"}, {"VYMN", "MGU"},
    {"VYMO", "MOE"}, {"VYMS", "MOG"}, {"VYMT", "MGK"}, {"VYMW", "MWQ"}, {"VYMY", "NYW"}, {"VYNS", "NMS"},
    {"VYNT", "NYT"}, {"VYPA", "PAA"}, {"VYPK", "PAU"}, {"VYPN", "BSX"}, {"VYPP", "PPU"}, {"VYPT", "PBU"},
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
