NZFunGi/micro-radar/include/EmbeddedCoastline.h

#pragma once

// Real land/sea data for one specific location and radar radius, computed
// entirely offline using the companion desktop app's coastline pipeline
// (MicroRadarCompanion/CoastlineGenerator.cs) against real OSM data:
//  1. Coastline ways are reprojected into local meters, merged into a line
//     network, closed against a bounding box slightly larger than the actual
//     configured radar radius so every way forms a proper closed ring.
//  2. NetTopologySuite's Polygonizer reconstructs actual closed land/sea
//     polygons from that network.
//  3. Each polygon is classified land or sea by voting across many points
//     along its own real-coastline boundary edges (offset slightly into the
//     polygon's interior, and only counted if genuinely close to a real
//     segment) - not by testing a single interior/representative point,
//     which turned out to be unreliable for large, complex regions (a
//     whole harbour system, an isthmus): different points within the SAME
//     connected region can be nearest to entirely unrelated stretches of
//     coastline, giving contradictory answers for what should be one
//     consistent classification.
//  4. For each of the device's actual 60x60 render grid cells (matching
//     CoastlineManager::GRID_SIZE/CELL_PX and the Projection::ToScreen
//     formula exactly), the real-world land area fraction within that cell
//     is computed by exact polygon intersection, and the cell is only
//     recorded here if land covers the MAJORITY of it.
//
// This location (Auckland Airport, NZ) is a public landmark chosen
// specifically so this example data doesn't reveal anyone's real home
// location in this public repository - swap in your own coordinates and
// regenerate via the companion app for your own device.
//
// This is a plain point cloud on the wire: each entry is the center of one
// already-decided device grid cell. Rendering just projects each point onto
// the screen grid and marks that cell as land directly - no segment/nearest-
// neighbor geometry needed on the device, and since the array is flash-
// resident, no heap allocation either.
//
// Regenerate this file if the device is relocated OR the radar radius
// changes (the per-cell majority decision was computed for one specific
// radius - see EMBEDDED_COASTLINE_RADIUS_USED below).

#include <cstdint>

constexpr double EMBEDDED_COASTLINE_LAT = -37.008;
constexpr double EMBEDDED_COASTLINE_LON = 174.792;
constexpr double EMBEDDED_COASTLINE_RADIUS_USED = 1.347467; // radar radius the per-cell majority decision was computed for
constexpr size_t EMBEDDED_LAND_POINT_COUNT = 1333;

// Flat (lat, lon) pairs as microdegrees (real value * 1e6) - the center of
// each already-decided device grid cell.
static const int32_t EMBEDDED_LAND_POINTS[EMBEDDED_LAND_POINT_COUNT * 2] = {
    -35682991, 173511906, -35682991, 173556822, -35682991, 173601737, -35682991, 173646653, -35682991, 173691569, -35682991, 173736484,
    -35682991, 173781400, -35682991, 173826315, -35682991, 173871231, -35682991, 173916146, -35682991, 173961062, -35682991, 174005978,
    -35682991, 174050893, -35682991, 174095809, -35682991, 174140724, -35682991, 174185640, -35682991, 174230555, -35682991, 174275471,
    -35682991, 174320387, -35682991, 174365302, -35682991, 174410218, -35682991, 174455133, -35682991, 174500049, -35727906, 173556822,
    -35727906, 173601737, -35727906, 173646653, -35727906, 173691569, -35727906, 173736484, -35727906, 173781400, -35727906, 173826315,
    -35727906, 173871231, -35727906, 173916146, -35727906, 173961062, -35727906, 174005978, -35727906, 174050893, -35727906, 174095809,
    -35727906, 174140724, -35727906, 174185640, -35727906, 174230555, -35727906, 174275471, -35727906, 174320387, -35727906, 174365302,
    -35727906, 174410218, -35727906, 174455133, -35727906, 174500049, -35772822, 173601737, -35772822, 173646653, -35772822, 173691569,
    -35772822, 173736484, -35772822, 173781400, -35772822, 173826315, -35772822, 173871231, -35772822, 173916146, -35772822, 173961062,
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
    -36221978, 174455133, -36221978, 174500049, -36221978, 174544964, -36221978, 174589880, -36221978, 174634796, -36221978, 174679711,
    -36221978, 175083951, -36221978, 175353445, -36221978, 175398360, -36221978, 175443276, -36266893, 174005978, -36266893, 174050893,
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
};
