NZFunGi/micro-radar/src/AircraftManager.h

#pragma once

#include <map>

#include "models/TrackedAircraft.h"
#include "ConfigurationWebServer.h"
#include "OpenSkyAuthTokenHandler.h"
#include "RouteLookupManager.h"
#include "LGFX.h"

class AircraftManager
{
private:
    double lat = 0.0;
    double lon = 0.0;
    double rad = 0.2;
    std::map<String, TrackedAircraft> trackedAircraft;

    bool displayInfoText = true;
    bool displayTriangles = true;

    unsigned long fetchInterval = 0;
    unsigned long lastFetch = 999999;

    ConfigurationWebServer& configServer;
    OpenSkyAuthTokenHandler& authHandler;
    HttpRequestManager& http;
    LGFX& tft;
    RouteLookupManager& routeManager;

    void DrawRadarCircles(LGFX_Sprite& backbuffer) const;
    std::pair<int, int> ProjectCoordinateToScreen(float predLat, float predLon) const;
    void DrawAircraftInfo(LGFX_Sprite& backbuffer, int x, int y, const TrackedAircraft& tracked) const;
    void DrawAircraftTriangle(LGFX_Sprite& backbuffer, int x, int y, const TrackedAircraft& tracked) const;

public:
    AircraftManager(ConfigurationWebServer& config, OpenSkyAuthTokenHandler& auth, HttpRequestManager& httpManager, LGFX& tftGfx, RouteLookupManager& routeLookupManager)
        : configServer(config), authHandler(auth), http(httpManager), tft(tftGfx), routeManager(routeLookupManager)
    {
    }
    ~AircraftManager() = default;

    void Initialise();
    void Update();
    void Draw(LGFX_Sprite& backbuffer);
};
